JennyDigital/Tower-of-Eightness/Board Art/ANSI Mono vid board.png

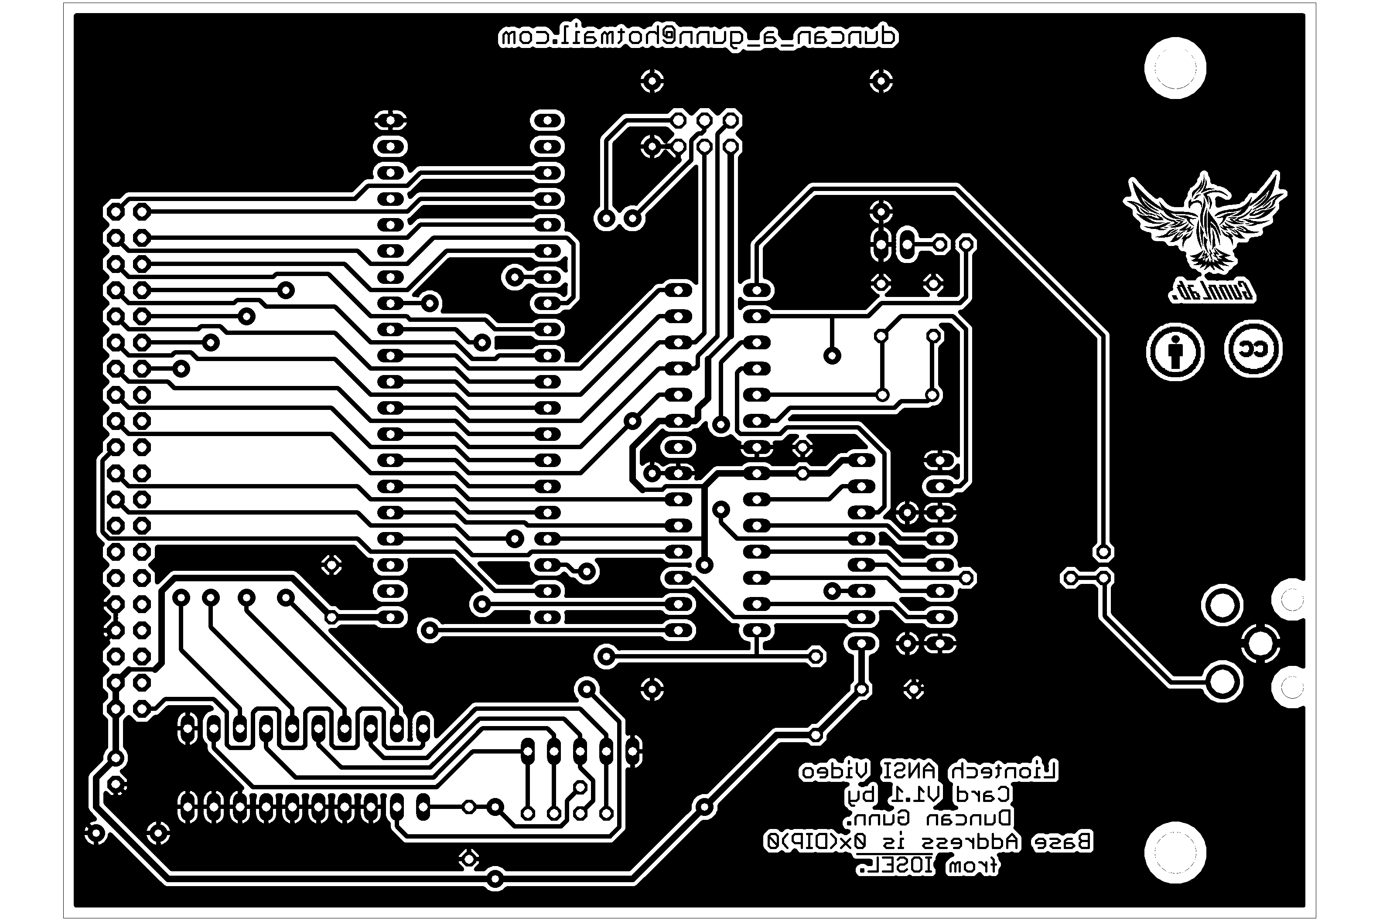
Board Art/ANSI Mono vid board.png
