JennyDigital/Tower-of-Eightness/Board Art/Bus IO Device Simulator.png

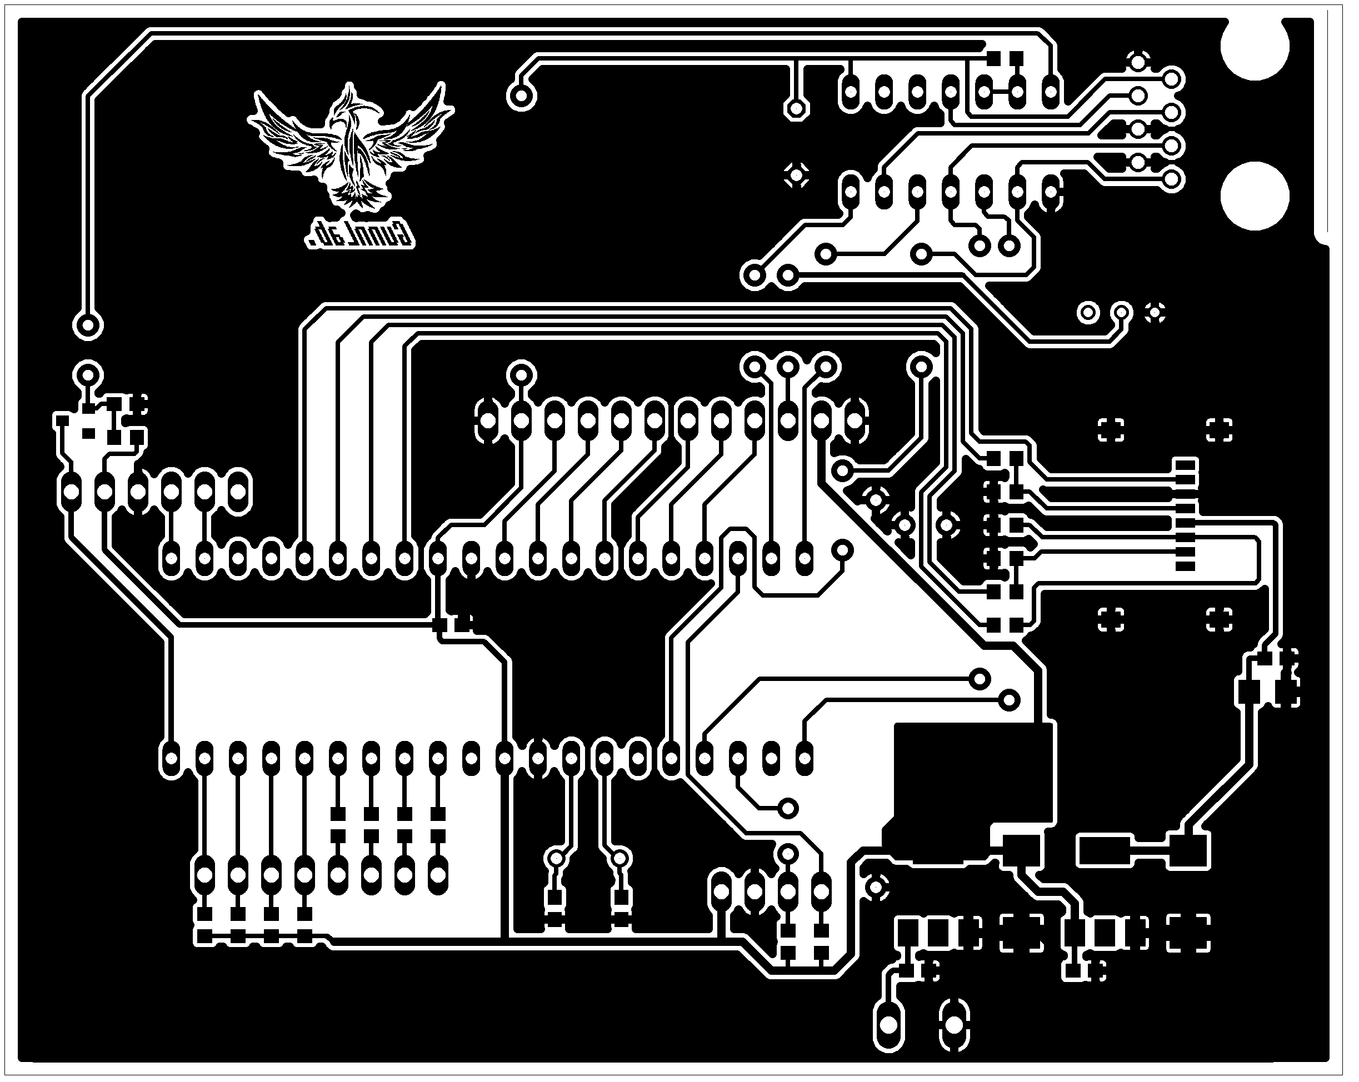
Board Art/Bus IO Device Simulator.png
