JennyDigital/Tower-of-Eightness/Board Art/Cardbus Card Extender.png

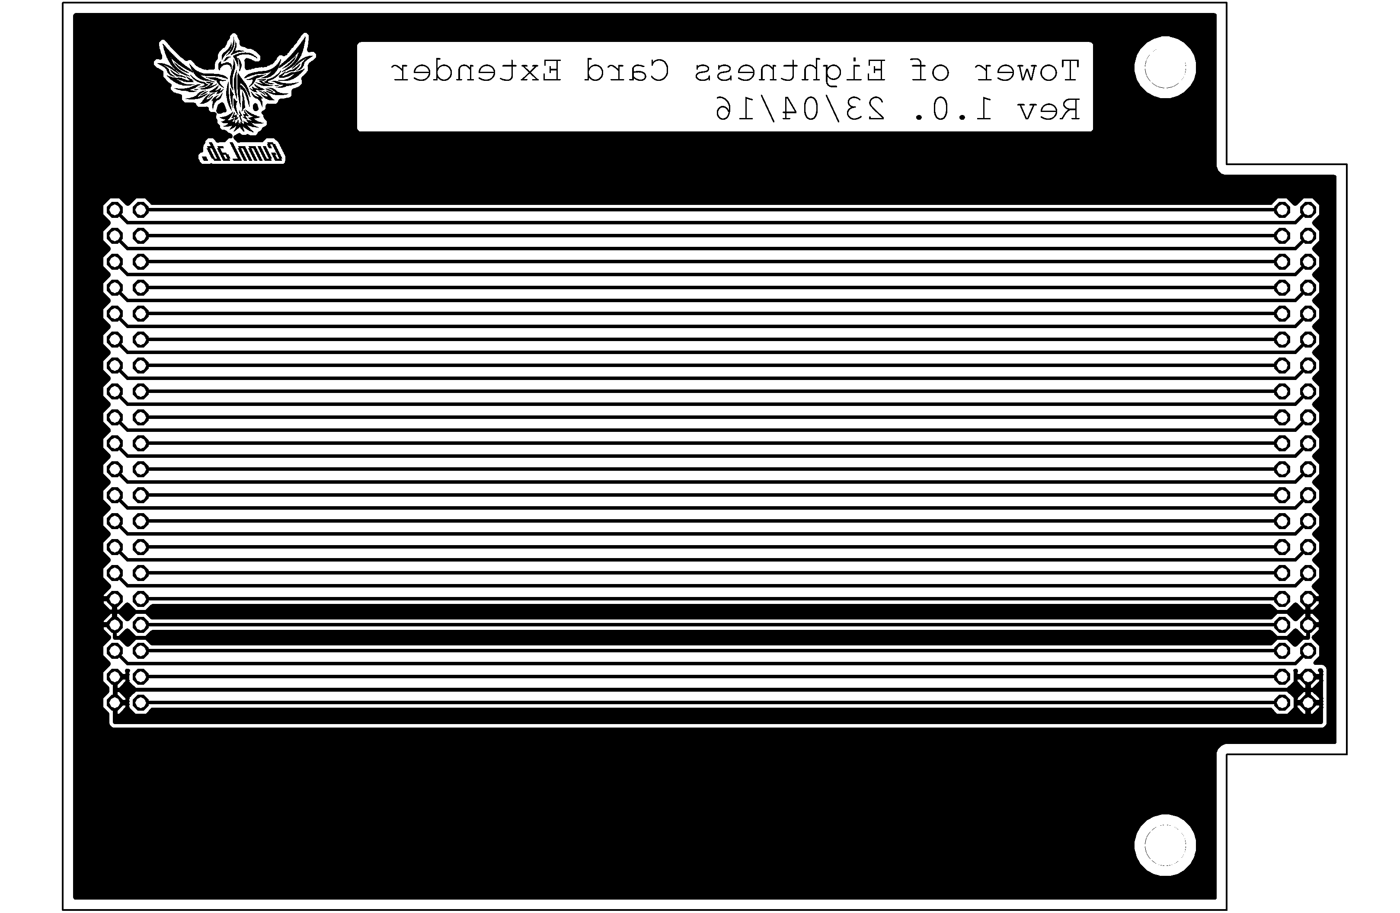
Board Art/Cardbus Card Extender.png
