JennyDigital/Tower-of-Eightness/Board Art/Serial Card V3.png

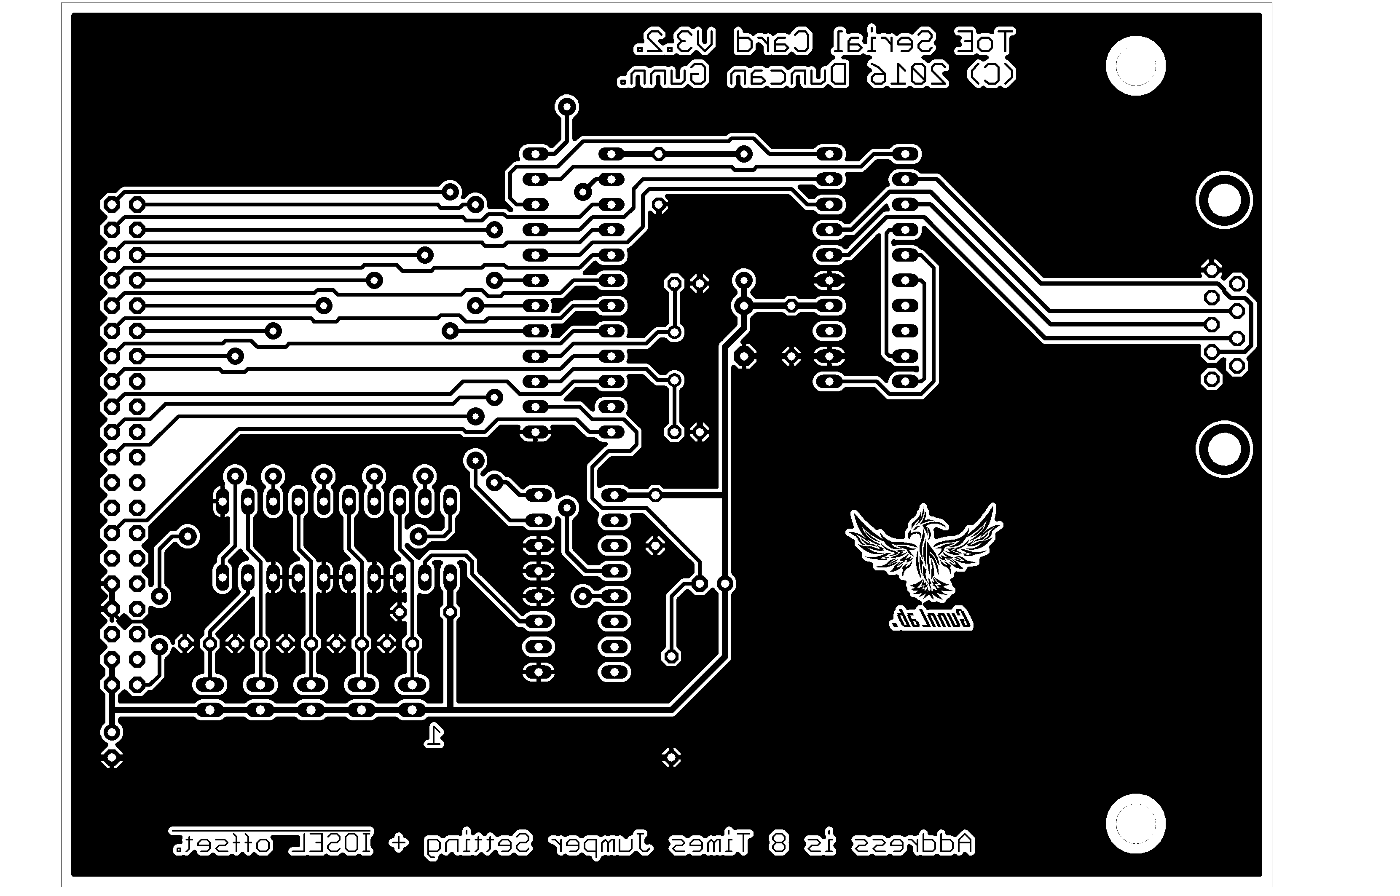
Board Art/Serial Card V3.png
