JennyDigital/Tower-of-Eightness/Board Art/Versatile IO Card.png

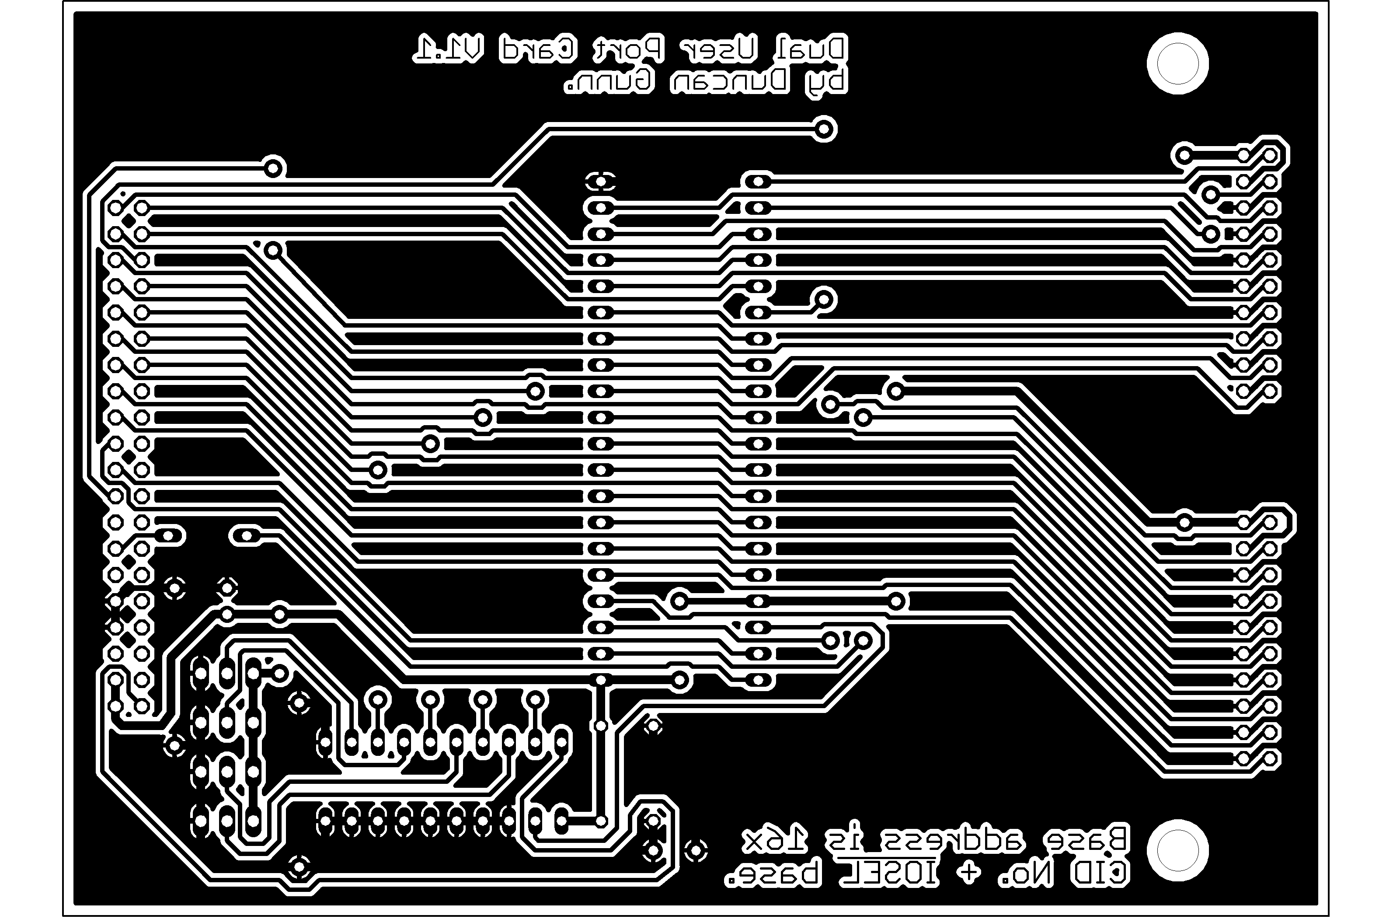
Board Art/Versatile IO Card.png
