JennyDigital/Tower-of-Eightness/Cases/Top Cap Assembly/STLs/Top Cap.stl

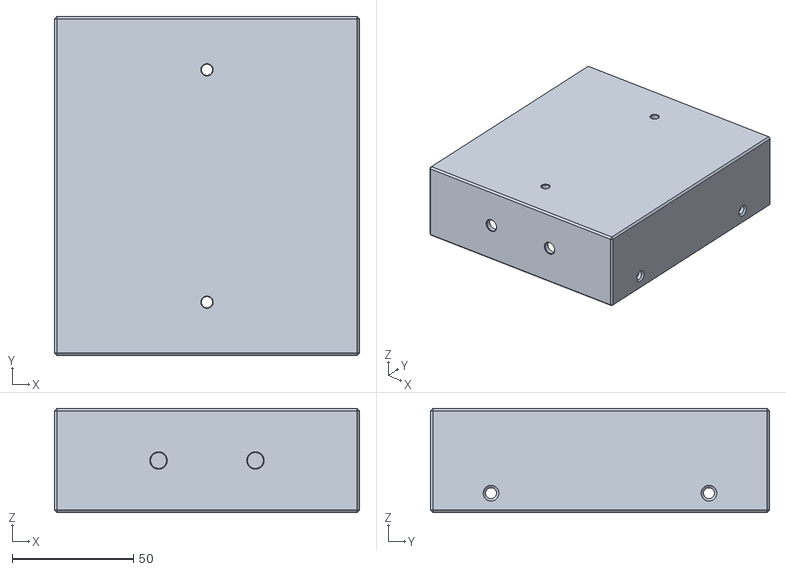
[picture p39: CAD file, 2021-09-05]
Cases/Top Cap Assembly/STLs/Top Cap.stl
126.0 x 140.0 x 43.0
