JennyDigital/Tower-of-Eightness/Cases/V3 Basetray/V3 Basetray.FCStd

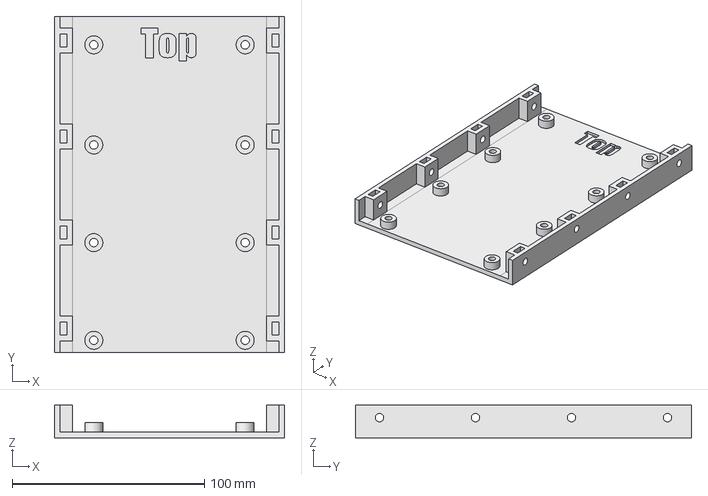
[picture p40: CAD file, 2021-09-05]
Cases/V3 Basetray/V3 Basetray.FCStd
120.0 x 175.0 x 17.0 mm
