JennyDigital/Tower-of-Eightness/Cases/Bottom cap assembly/Decorative Hoop.FCStd

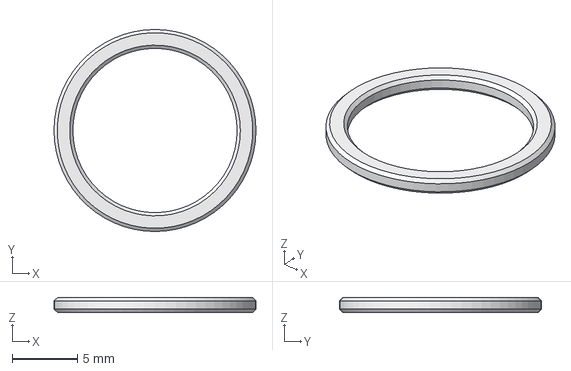
[picture p41: CAD file, 2021-09-05]
Cases/Bottom cap assembly/Decorative Hoop.FCStd
15.5 x 15.5 x 1.12 mm
