JennyDigital/Tower-of-Eightness/Cases/Bottom cap assembly/STLs/Frontplate.stl

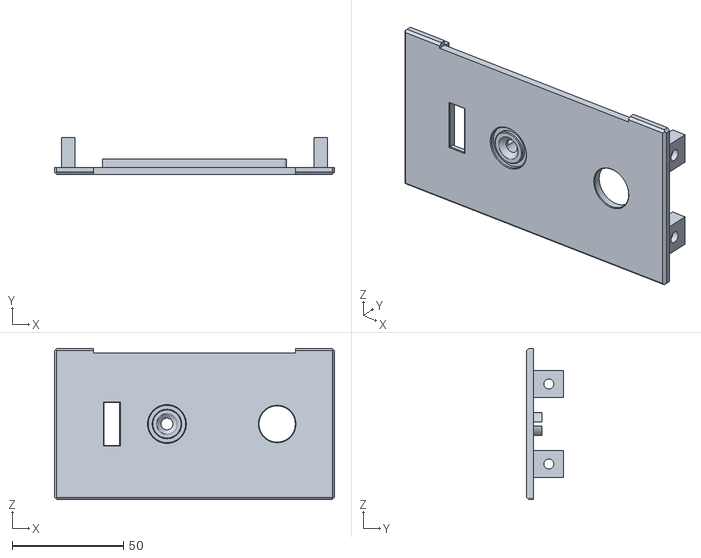
[picture p42: CAD file, 2023-03-17]
Cases/Bottom cap assembly/STLs/Frontplate.stl
126.0 x 16.5 x 68.0
