JennyDigital/Tower-of-Eightness/Cases/Faceplates/Bus Card Faceplate.fcstd

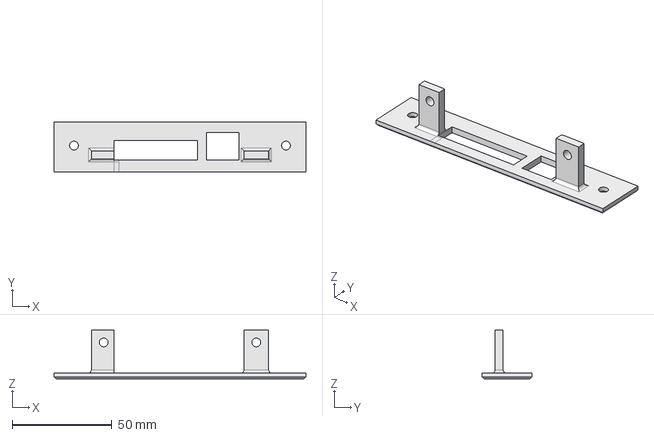
[picture p43: CAD file, 2018-06-14]
Cases/Faceplates/Bus Card Faceplate.fcstd
126.0 x 25.0 x 24.5 mm
