JennyDigital/Tower-of-Eightness/Cases/PS2 to RS232 kb adaptor (compact)/PS2 to RS232 base.FCStd

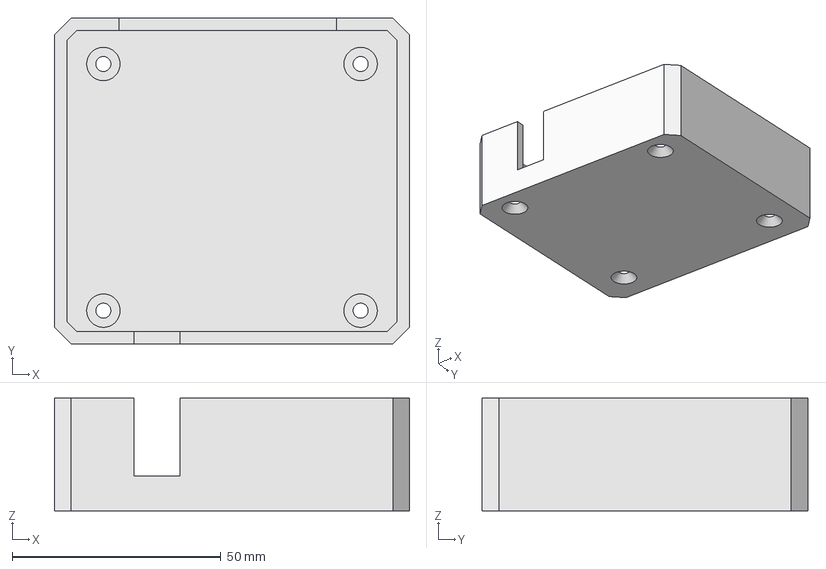
[picture p44: CAD file, 2023-03-17]
Cases/PS2 to RS232 kb adaptor (compact)/PS2 to RS232 base.FCStd
85.0 x 78.0 x 27.0 mm
