JennyDigital/Tower-of-Eightness/Cases/PS2 to Serial KB Adapter Enclosure (larger)/Foot.stl

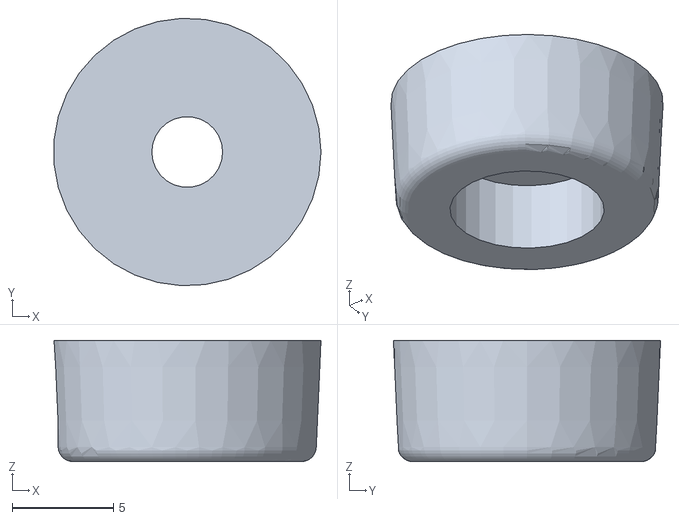
[picture p45: CAD file, 2023-03-17]
Cases/PS2 to Serial KB Adapter Enclosure (larger)/Foot.stl
13.2 x 13.2 x 6.00
