JennyDigital/Tower-of-Eightness/Cases/Sideplate/Sideplate with support edge.FCStd

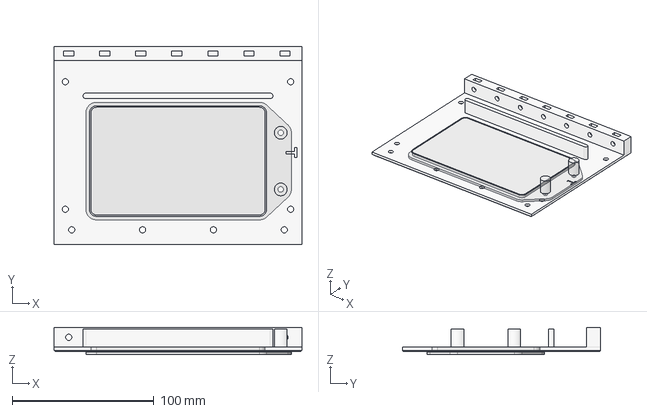
[picture p46: CAD file, 2023-03-17]
Cases/Sideplate/Sideplate with support edge.FCStd
175.0 x 140.0 x 19.2 mm
Sideplate
Vented cover
