JennyDigital/Tower-of-Eightness/Cases/Tape and Joystick Interface V1/Lid.stl

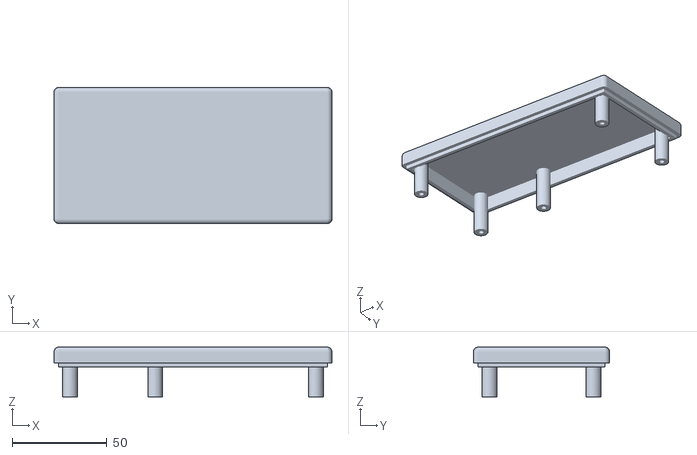
[picture p47: CAD file, 2021-09-05]
Cases/Tape and Joystick Interface V1/Lid.stl
147.0 x 72.0 x 26.4
