JennyDigital/Tower-of-Eightness/Cases/Assembly model (WIP)/Badge frame.stl

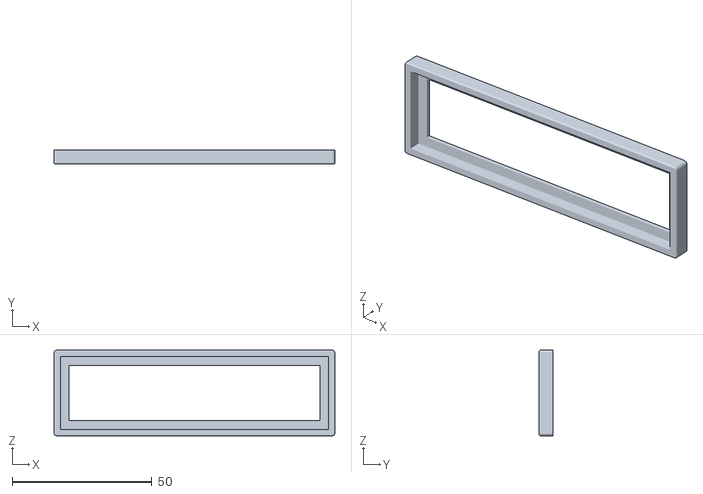
[picture p48: CAD file, 2023-03-17]
Cases/Assembly model (WIP)/Badge frame.stl
100.7 x 5.00 x 30.7
