JennyDigital/Tower-of-Eightness/Cases/Faceplates/Faceplate Blank V2.stl

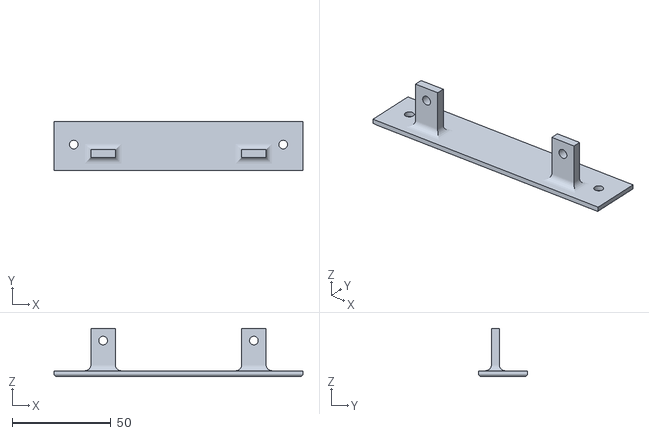
[picture p49: CAD file, 2018-06-14]
Cases/Faceplates/Faceplate Blank V2.stl
126.0 x 25.0 x 24.5
