JennyDigital/Tower-of-Eightness/Cases/PS2 to Serial KB Adapter Enclosure (larger)/Adapter.FCStd

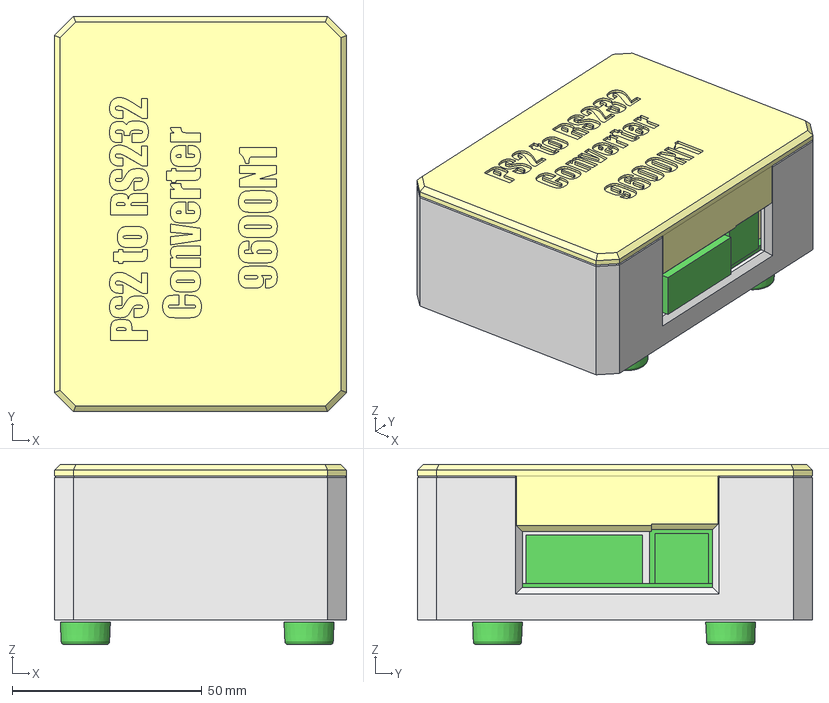
[picture p50: CAD file, 2023-03-17]
Cases/PS2 to Serial KB Adapter Enclosure (larger)/Adapter.FCStd
77.0 x 104.2 x 47.5 mm
PCB
Case base
Lid
Set of feet
