JennyDigital/Tower-of-Eightness/Cases/Sideplate/Tab.stl

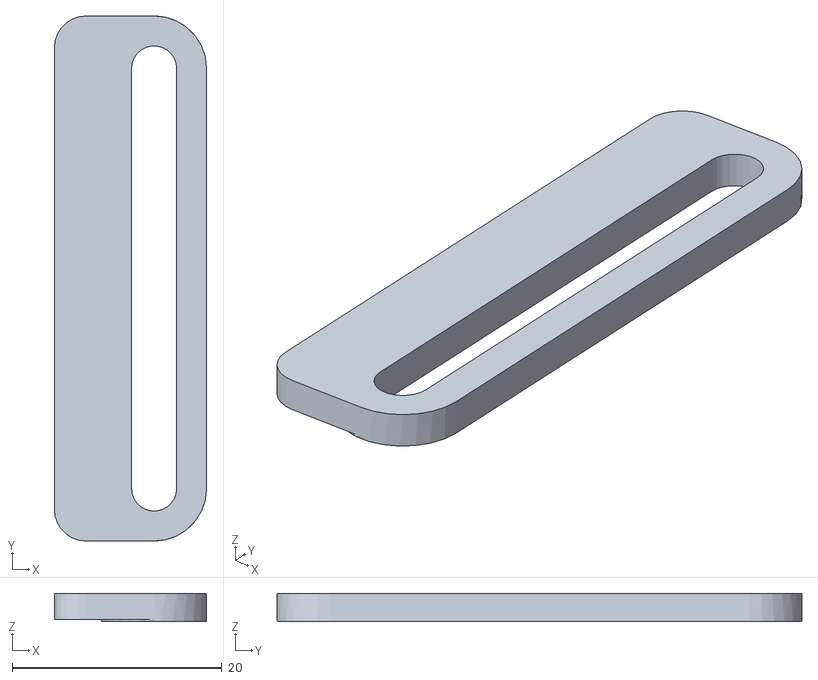
[picture p51: CAD file, 2023-03-17]
Cases/Sideplate/Tab.stl
14.5 x 50.0 x 2.70
