JennyDigital/Tower-of-Eightness/Cases/Bottom cap assembly/STLs/Backplate.stl

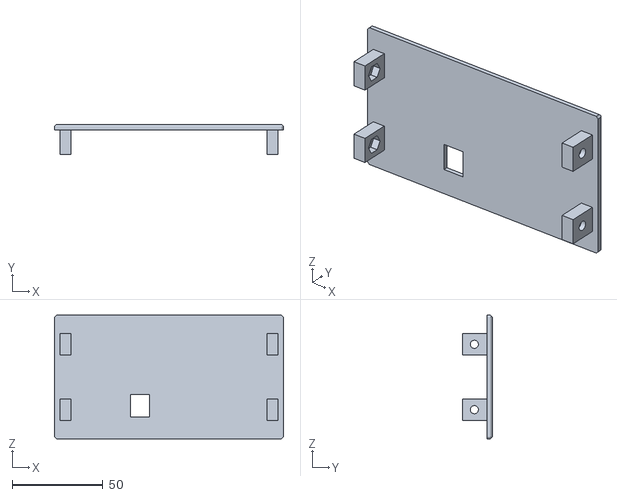
[picture p52: CAD file, 2021-09-05]
Cases/Bottom cap assembly/STLs/Backplate.stl
126.0 x 16.5 x 68.0
