JennyDigital/Tower-of-Eightness/Cases/Faceplates/Serial Faceplate.stl

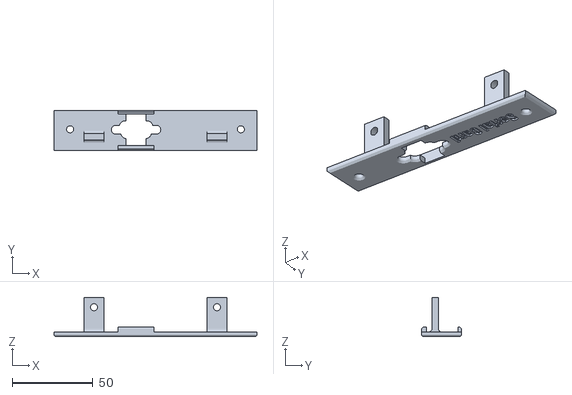
[picture p53: CAD file, 2018-06-14]
Cases/Faceplates/Serial Faceplate.stl
126.0 x 25.0 x 24.5
