JennyDigital/Tower-of-Eightness/Cases/PS2 to Serial KB Adapter Enclosure (larger)/Base.stl

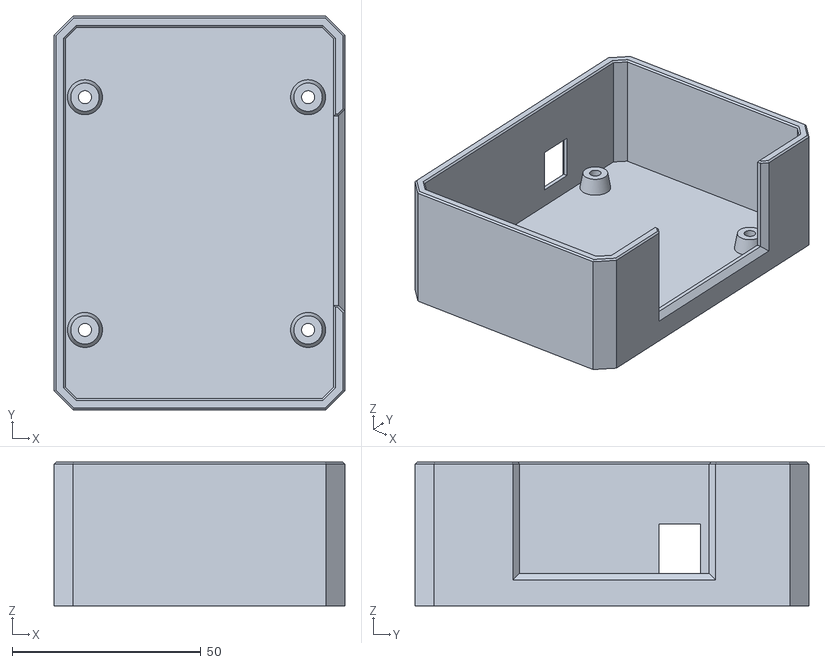
[picture p54: CAD file, 2023-03-17]
Cases/PS2 to Serial KB Adapter Enclosure (larger)/Base.stl
77.0 x 104.2 x 38.0
