JennyDigital/Tower-of-Eightness/Cases/Sideplate/Sideplate with support edges.step

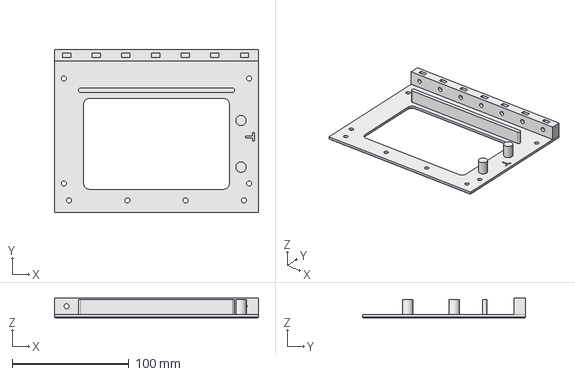
[picture p55: CAD file, 2023-03-17]
Cases/Sideplate/Sideplate with support edges.step
175.0 x 140.0 x 17.0 mm
