JennyDigital/Tower-of-Eightness/Cases/Tape and Joystick Interface V1/Tape and Joystick Interface V1.FCStd

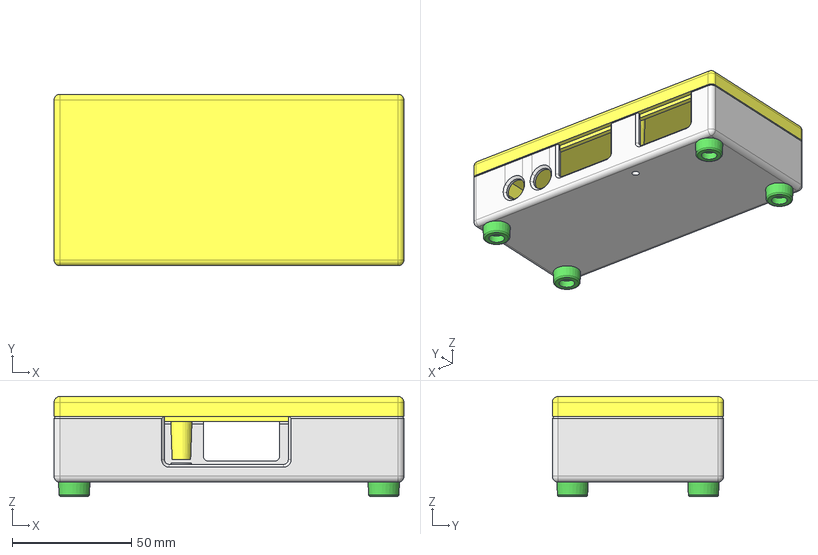
[picture p56: CAD file, 2021-09-05]
Cases/Tape and Joystick Interface V1/Tape and Joystick Interface V1.FCStd
147.0 x 72.0 x 42.0 mm
Box Base
Box Lid
Set of feet
