JennyDigital/Tower-of-Eightness/Cases/Bottom cap assembly/STLs/Hoop.stl

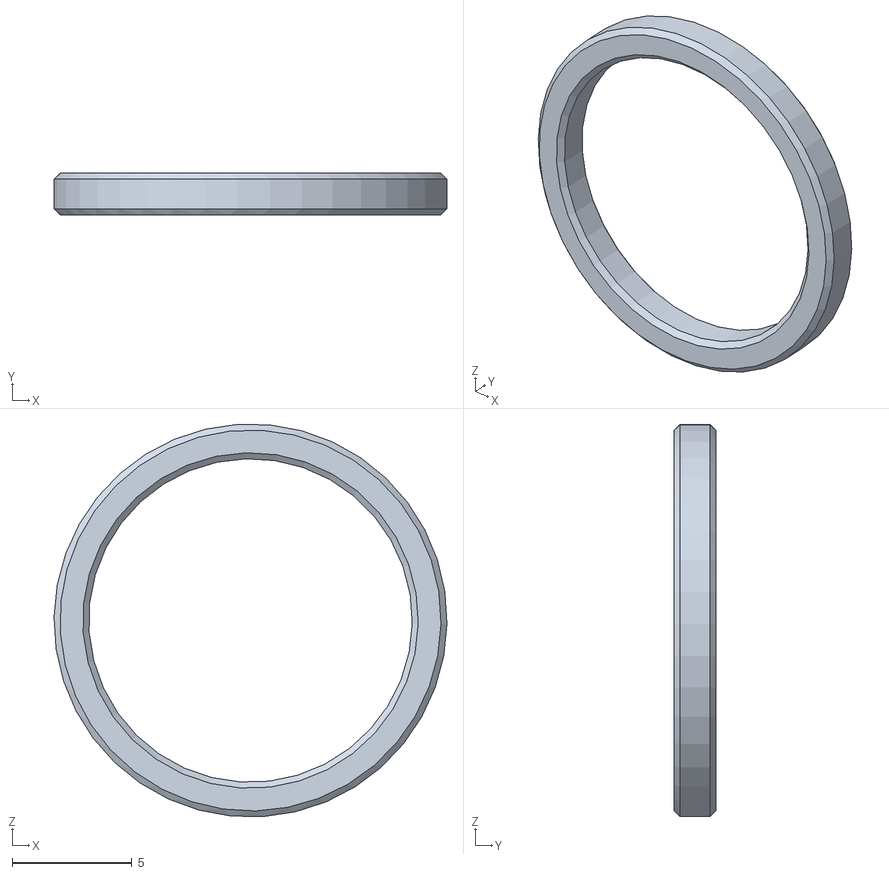
[picture p57: CAD file, 2021-09-05]
Cases/Bottom cap assembly/STLs/Hoop.stl
16.4 x 1.75 x 16.4
