JennyDigital/Tower-of-Eightness/Cases/Faceplates/Status Plate.fcstd

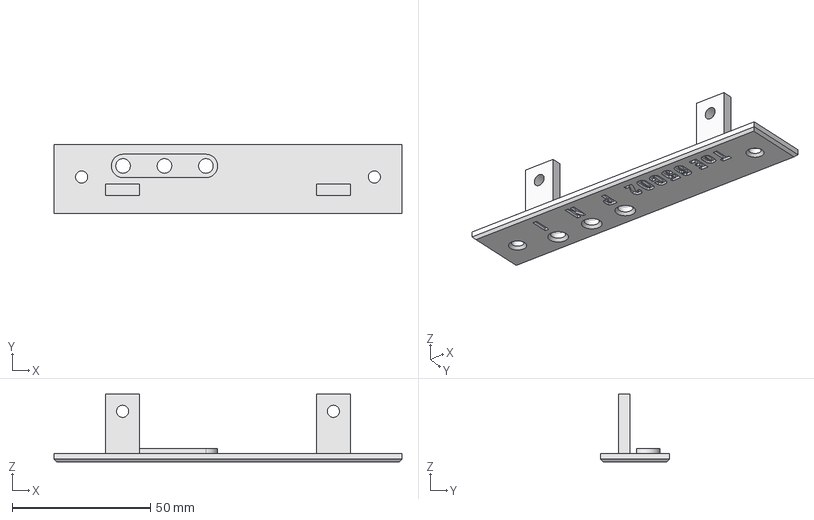
[picture p58: CAD file, 2018-06-14]
Cases/Faceplates/Status Plate.fcstd
126.0 x 25.0 x 24.5 mm
ChamferBody
