JennyDigital/Tower-of-Eightness/Cases/Sideplate/Sideplate with cover.FCStd

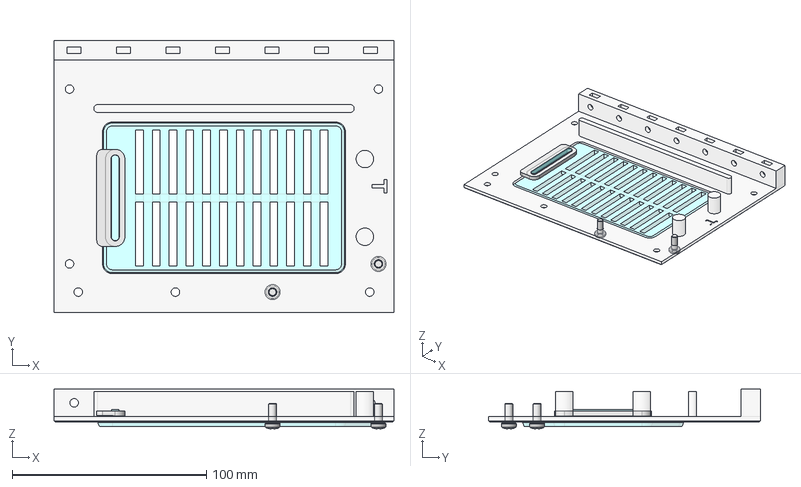
[picture p59: CAD file, 2023-03-17]
Cases/Sideplate/Sideplate with cover.FCStd
175.0 x 140.0 x 20.4 mm
Sideplate
Vented cover
Tab
M4 screw for testing
M4 screw for testing001
