JennyDigital/Tower-of-Eightness/Cases/Bottom cap assembly/STLs/Joining-bar.stl

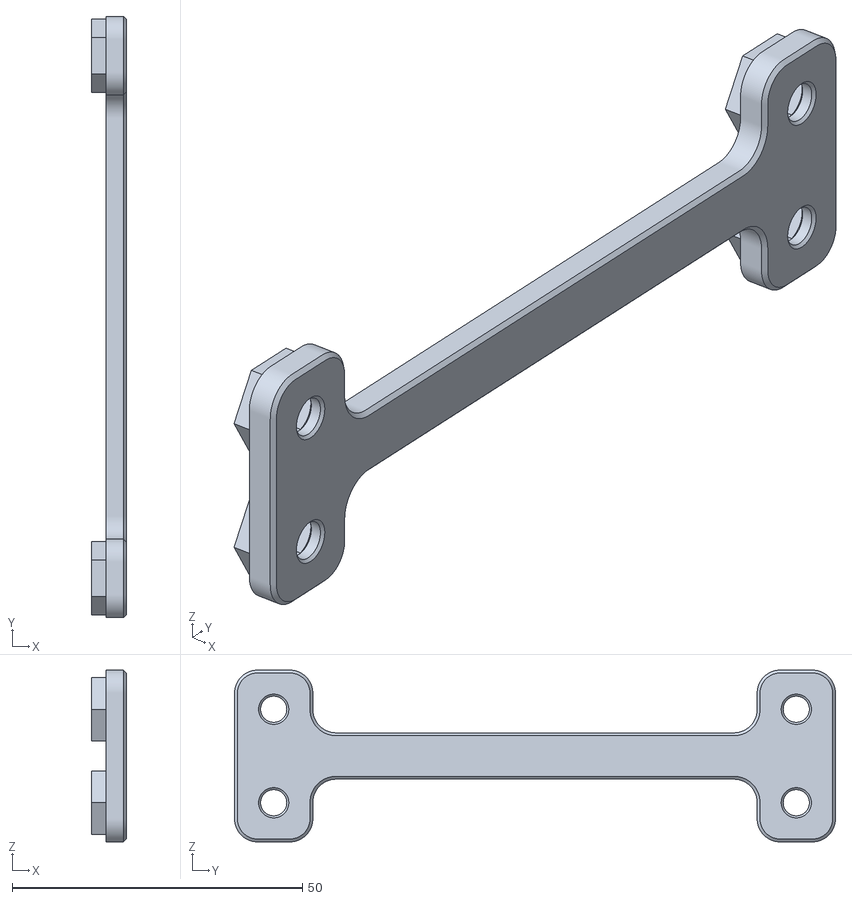
[picture p60: CAD file, 2021-09-05]
Cases/Bottom cap assembly/STLs/Joining-bar.stl
6.00 x 103.5 x 29.6
