JennyDigital/Tower-of-Eightness/Cases/Faceplates/Card Faceplate CPU V2.FCStd

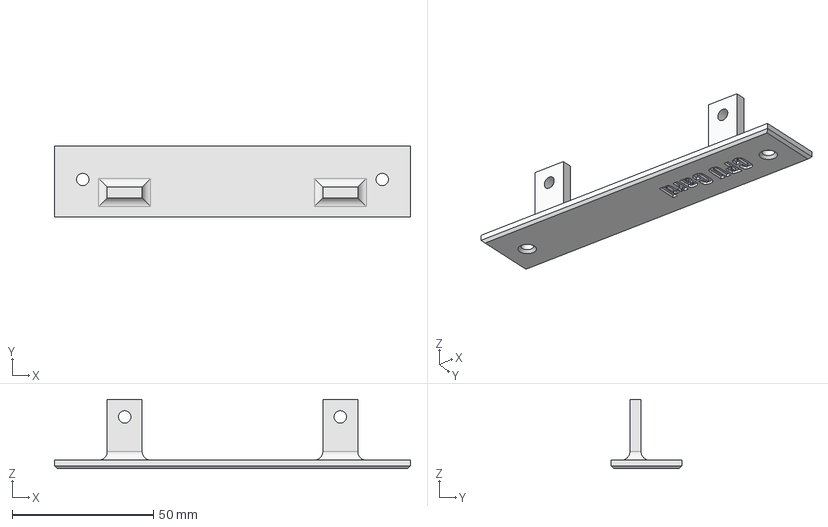
[picture p61: CAD file, 2018-06-14]
Cases/Faceplates/Card Faceplate CPU V2.FCStd
126.0 x 25.0 x 24.5 mm
