JennyDigital/Tower-of-Eightness/Cases/Finished Endcap blank.FCStd

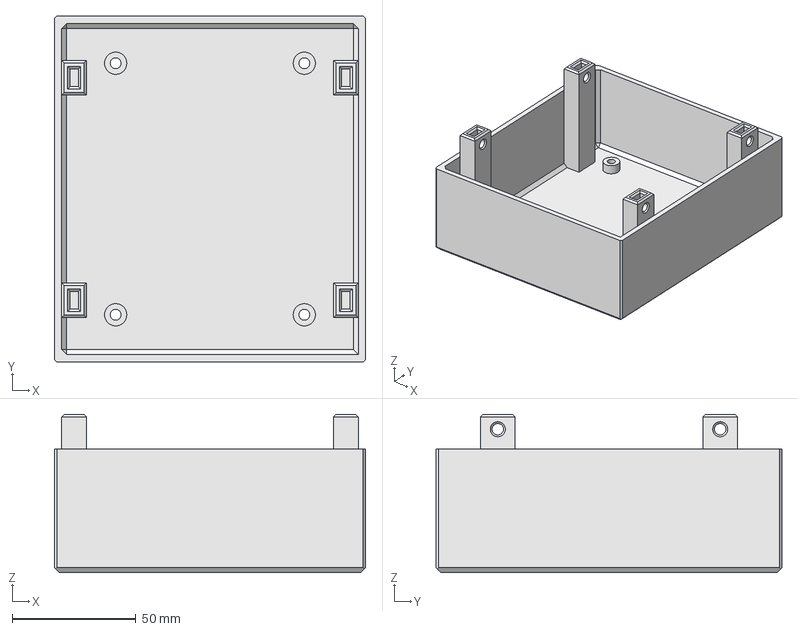
[picture p62: CAD file, 2018-06-14]
Cases/Finished Endcap blank.FCStd
126.0 x 140.0 x 64.0 mm
