JennyDigital/Tower-of-Eightness/Cases/Sideplate/Sideplate.FCStd

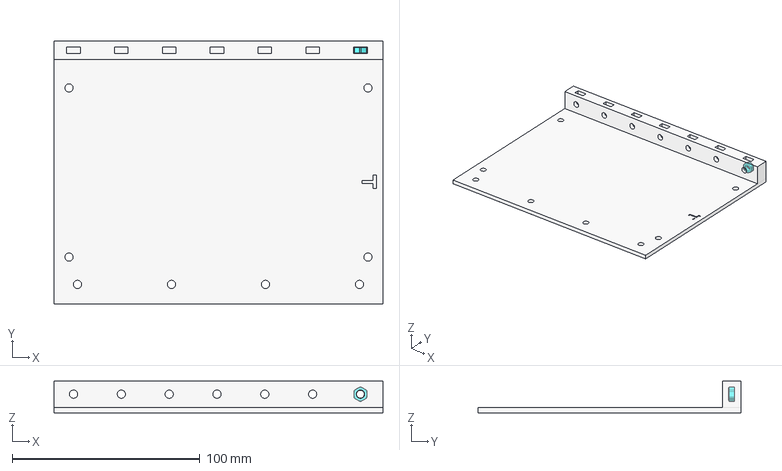
[picture p63: CAD file, 2023-03-17]
Cases/Sideplate/Sideplate.FCStd
175.0 x 140.0 x 17.0 mm
M4 Nut
