JennyDigital/Tower-of-Eightness/Cases/Bottom cap assembly/STLs/Baseplate.stl

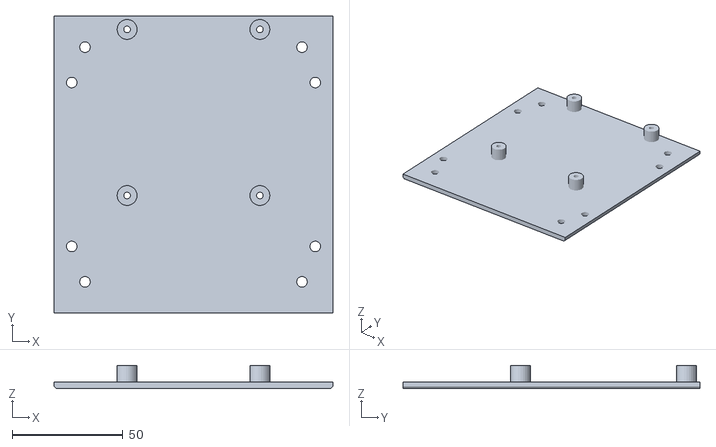
[picture p64: CAD file, 2021-09-05]
Cases/Bottom cap assembly/STLs/Baseplate.stl
126.0 x 134.0 x 10.4
