JennyDigital/Tower-of-Eightness/Cases/Guide Vee.FCStd

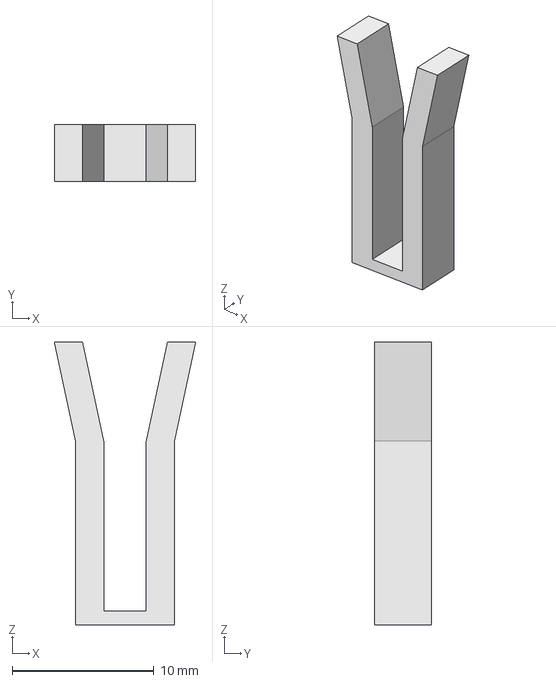
[picture p65: CAD file, 2018-06-14]
Cases/Guide Vee.FCStd
10.0 x 4.00 x 20.0 mm
