JennyDigital/Tower-of-Eightness/Cases/Guide Vee (Deeper).step

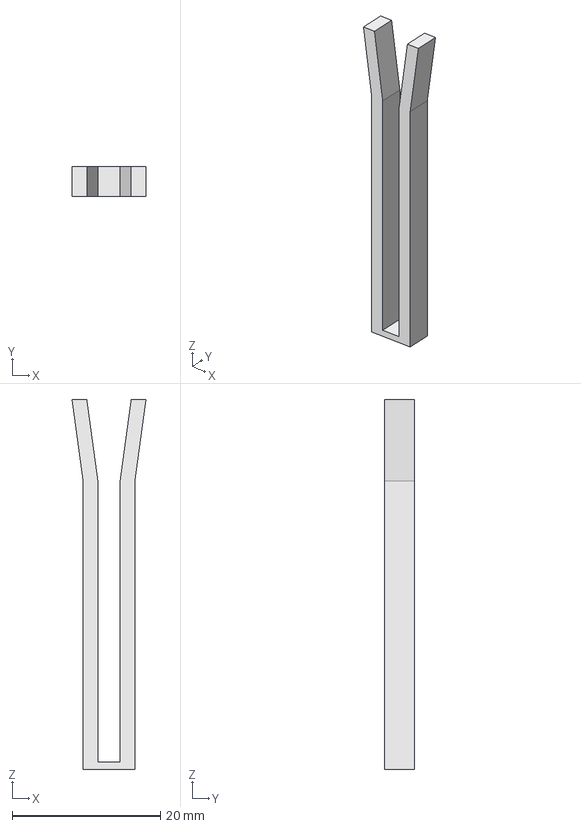
[picture p66: CAD file, 2018-06-14]
Cases/Guide Vee (Deeper).step
10.0 x 4.00 x 50.0 mm
