JennyDigital/Tower-of-Eightness/Cases/Faceplates/Sound Card V1.FCStd

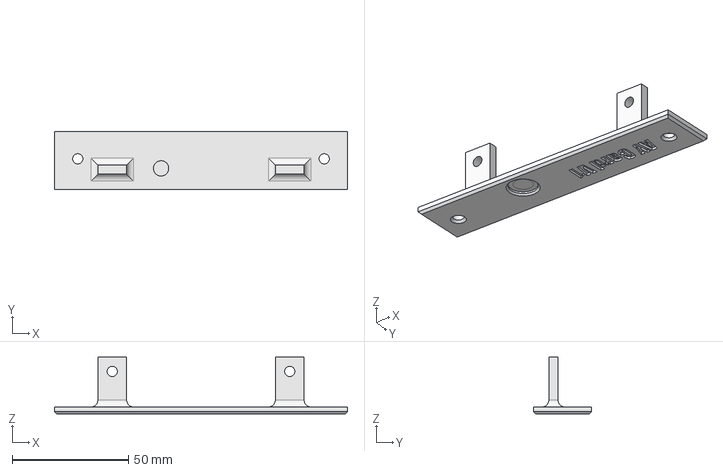
[picture p67: CAD file, 2018-06-14]
Cases/Faceplates/Sound Card V1.FCStd
126.0 x 25.0 x 24.5 mm
