JennyDigital/Tower-of-Eightness/Cases/Taller Card Guide.fcstd

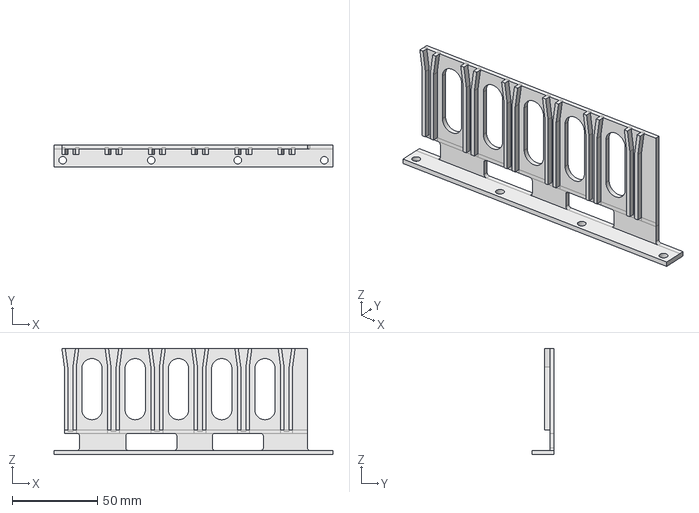
[picture p68: CAD file, 2018-06-14]
Cases/Taller Card Guide.fcstd
164.1 x 13.0 x 62.5 mm
