JennyDigital/Tower-of-Eightness/Cases/Endcap blank.FCStd

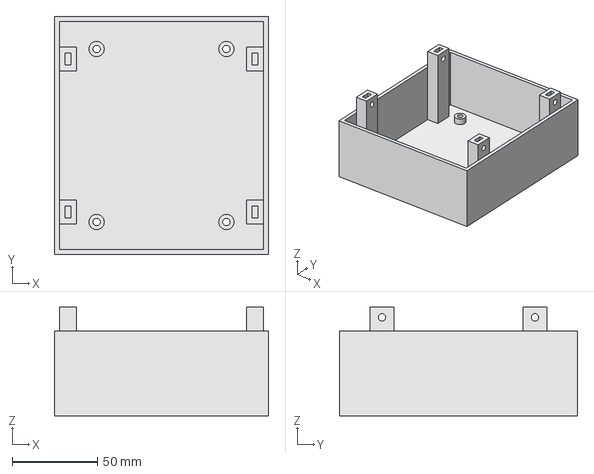
[picture p69: CAD file, 2018-06-14]
Cases/Endcap blank.FCStd
126.0 x 140.0 x 64.0 mm
