JennyDigital/Tower-of-Eightness/Cases/Faceplates/Memory Faceplate V2.FCStd

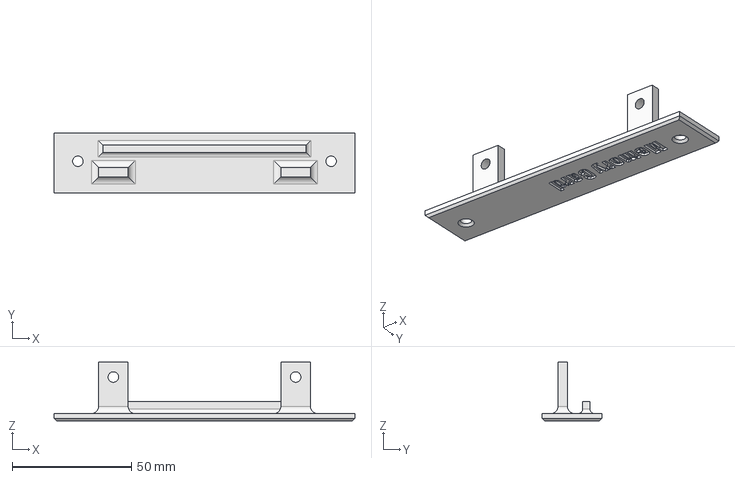
[picture p71: CAD file, 2018-06-14]
Cases/Faceplates/Memory Faceplate V2.FCStd
126.0 x 25.0 x 24.5 mm
