JennyDigital/Tower-of-Eightness/Schematics/ANSI-Video-Board/ANSI Mono vid board.brd

## EAGLE design Schematics/ANSI-Video-Board/ANSI Mono vid board.brd (2021-09-05)

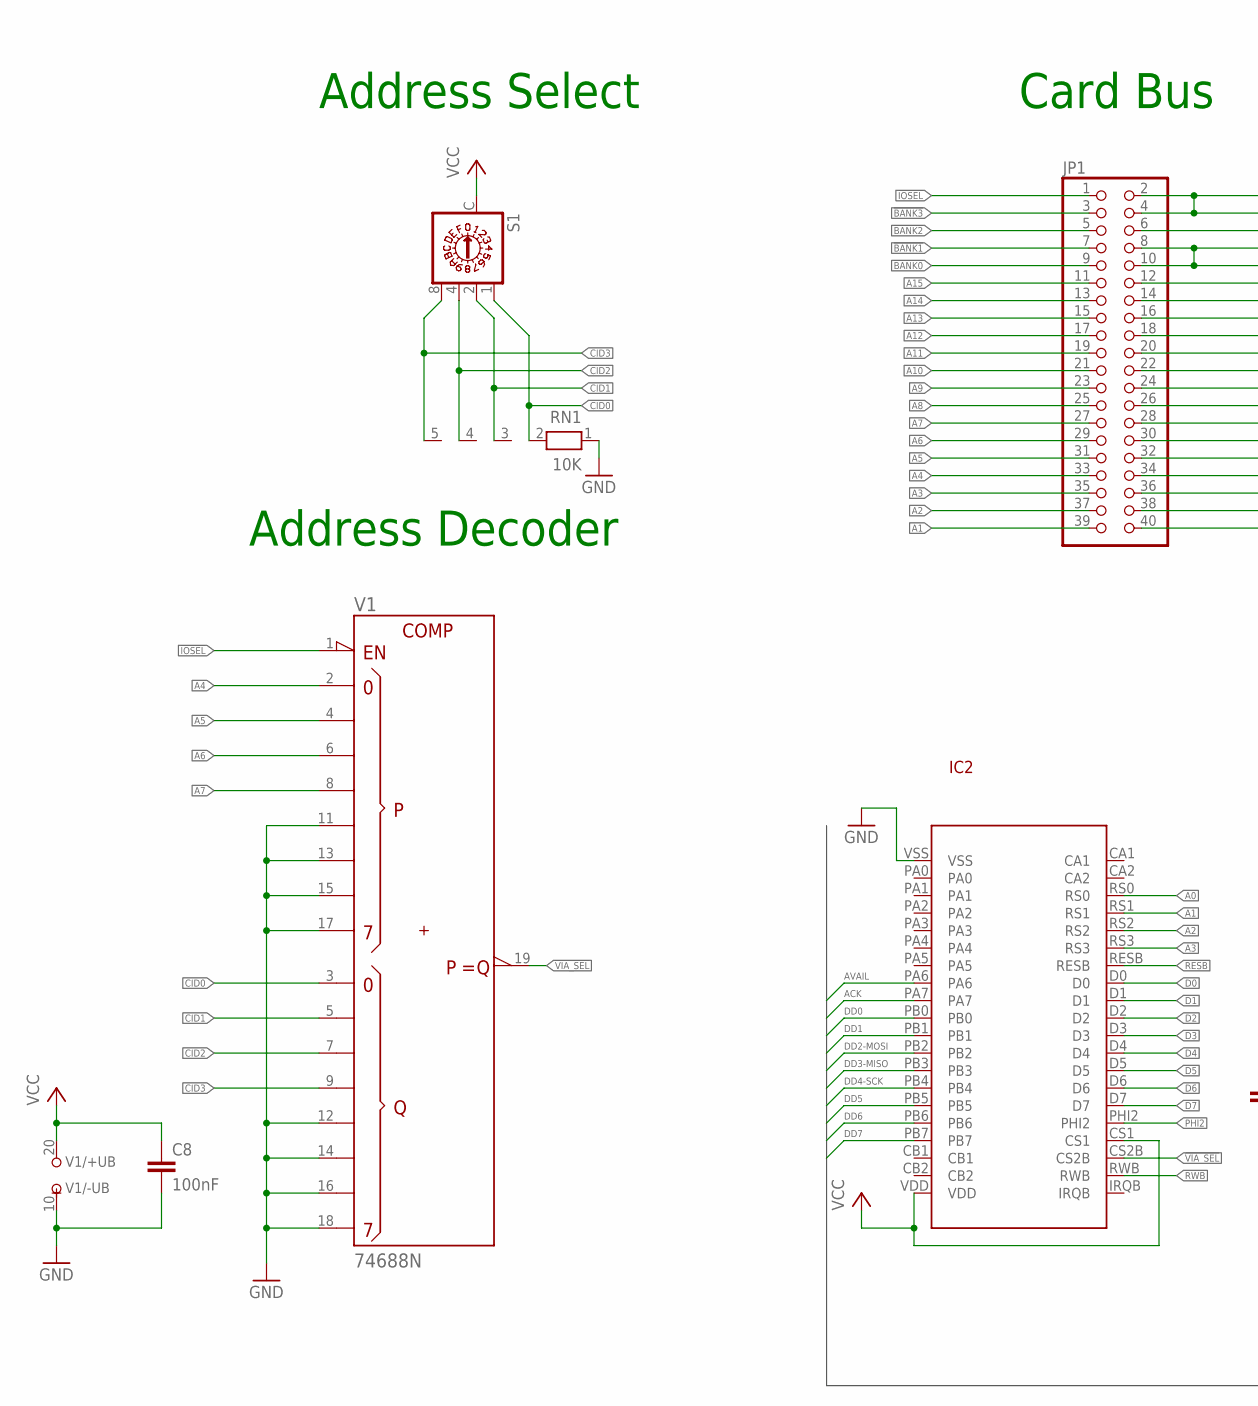
[picture p96: schematic ANSI Mono vid board.sch, part in row 1, column 1]

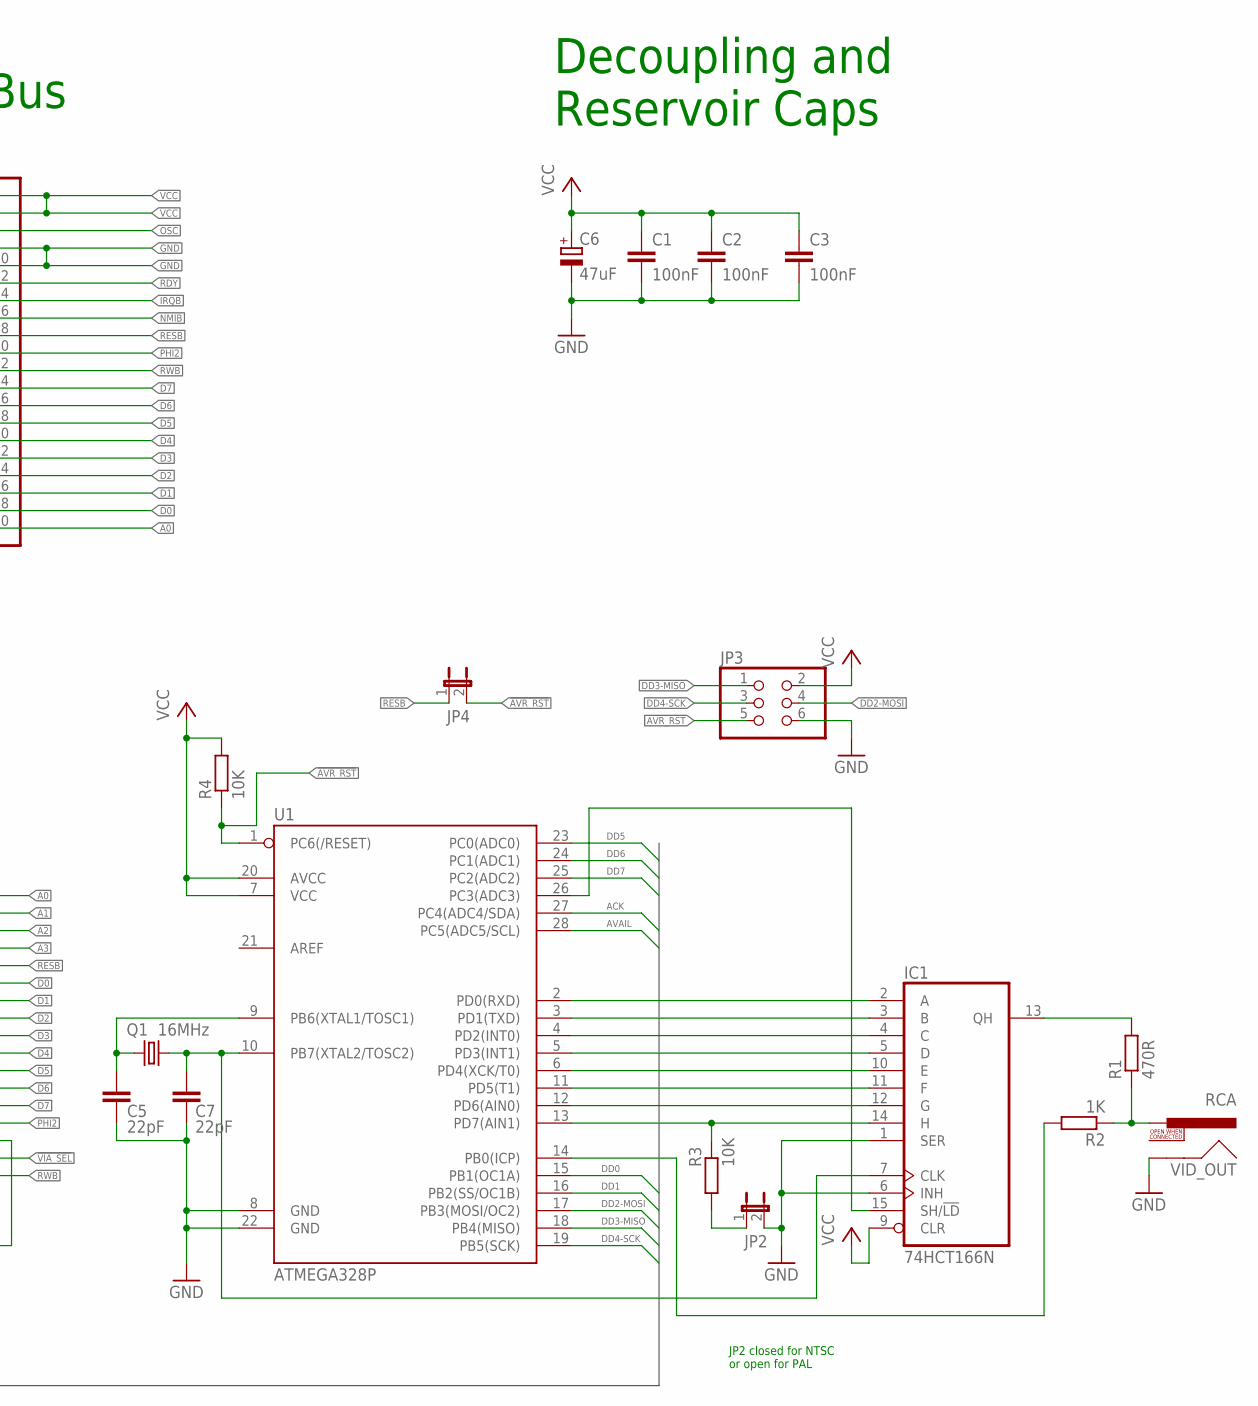
[picture p97: schematic ANSI Mono vid board.sch, part in row 1, column 2]

Parts:
C1, C2, C8: 100nF; C050-025X075
C3: 100nF; C025-025X050
C5, C7: 22pF; C050-025X075
C6: 47uF; E2,5-7
IC1: 74HCT166N; DIL16
IC2: W65C22; W65C22-DIP
JP1: PINHD-2X20/90; 2X20/90
JP2, JP4: JP1E; JP1
JP3: PINHD-2X3; 2X03
Q1: 16MHz; HC49U-V
R1: 470R; 0207/10
R2: 1K; 0207/10
R3: 10K; 0207/2V
R4: 10K; 0207/7
RN1: 10K; RN-5
S1: DRR3016; DRR3010
U1: ATMEGA328P; DIL28-3
V1: 74688N; DIL20
VID_OUT: RCA

Connections:
!AVR_RST: JP3.5, JP4.2, R4.1, U1.1 (PC6(/RESET))
!BANK0: JP1.9
!BANK1: JP1.7
!BANK2: JP1.5
!BANK3: JP1.3
!IOSEL: JP1.1, V1.1 (!G)
!VIA_SEL: IC2.CS2B, V1.19 (!P=Q)
A0: IC2.RS0, JP1.40
A1: IC2.RS1, JP1.39
A2: IC2.RS2, JP1.37
A3: IC2.RS3, JP1.35
A4: JP1.33, V1.2 (P0)
A5: JP1.31, V1.4 (P1)
A6: JP1.29, V1.6 (P2)
A7: JP1.27, V1.8 (P3)
A8: JP1.25
A9: JP1.23
A10: JP1.21
A11: JP1.19
A12: JP1.17
A13: JP1.15
A14: JP1.13
A15: JP1.11
ACK: IC2.PA7, U1.27 (PC4(ADC4/SDA))
AVAIL: IC2.PA6, U1.28 (PC5(ADC5/SCL))
CID0: RN1.2, S1.1, V1.3 (Q0)
CID1: RN1.3, S1.2, V1.5 (Q1)
CID2: RN1.4, S1.4, V1.7 (Q2)
CID3: RN1.5, S1.8, V1.9 (Q3)
D0: IC2.D0, JP1.38
D1: IC2.D1, JP1.36
D2: IC2.D2, JP1.34
D3: IC2.D3, JP1.32
D4: IC2.D4, JP1.30
D5: IC2.D5, JP1.28
D6: IC2.D6, JP1.26
D7: IC2.D7, JP1.24
DD0: IC2.PB0, U1.15 (PB1(OC1A))
DD1: IC2.PB1, U1.16 (PB2(SS/OC1B))
DD2-MOSI: IC2.PB2, JP3.4, U1.17 (PB3(MOSI/OC2))
DD3-MISO: IC2.PB3, JP3.1, U1.18 (PB4(MISO))
DD4-SCK: IC2.PB4, JP3.3, U1.19 (PB5(SCK))
DD5: IC2.PB5, U1.23 (PC0(ADC0))
DD6: IC2.PB6, U1.24 (PC1(ADC1))
DD7: IC2.PB7, U1.25 (PC2(ADC2))
GND: C1.2, C2.2, C3.2, C5.2, C6.-, C7.2, C8.2, IC1.1 (SER), IC1.6 (INH), IC1.8 (GND), IC2.VSS, JP1.8, JP1.10, JP2.2, JP3.6, RN1.1, U1.8 (GND), U1.22 (GND), V1.10 (-UB), V1.11 (P4), V1.12 (Q4), V1.13 (P5), V1.14 (Q5), V1.15 (P6), V1.16 (Q6), V1.17 (P7), V1.18 (Q7), VID_OUT.SHELL
IRQB: JP1.14
unnamed: JP2.1, R3.1
unnamed: C5.1, Q1.2, U1.9 (PB6(XTAL1/TOSC1))
unnamed: C7.1, IC1.7 (CLK), Q1.1, U1.10 (PB7(XTAL2/TOSC2))
unnamed: IC1.2 (A), U1.2 (PD0(RXD))
unnamed: IC1.3 (B), U1.3 (PD1(TXD))
unnamed: IC1.4 (C), U1.4 (PD2(INT0))
unnamed: IC1.5 (D), U1.5 (PD3(INT1))
unnamed: IC1.10 (E), U1.6 (PD4(XCK/T0))
unnamed: IC1.11 (F), U1.11 (PD5(T1))
unnamed: IC1.12 (G), U1.12 (PD6(AIN0))
unnamed: IC1.14 (H), R3.2, U1.13 (PD7(AIN1))
unnamed: IC1.13 (QH), R1.2
unnamed: R2.2, U1.14 (PB0(ICP))
unnamed: IC1.15 (SH/!LD), U1.26 (PC3(ADC3))
unnamed: R1.1, R2.1, VID_OUT.PIN
NMIB: JP1.16
OSC: JP1.6
PHI2: IC2.PHI2, JP1.20
RDY: JP1.12
RESB: IC2.RESB, JP1.18, JP4.1
RWB: IC2.RWB, JP1.22
VCC: C1.1, C2.1, C3.1, C6.+, C8.1, IC1.9 (CLR), IC1.16 (VCC), IC2.CS1, IC2.VDD, JP1.2, JP1.4, JP3.2, R4.2, S1.C, U1.7 (VCC), U1.20 (AVCC), V1.20 (+UB)

Notes on the sheet:
Card Bus
Decoupling and Reservoir Caps
JP2 closed for NTSC or open for PAL
Address Select
Address Decoder

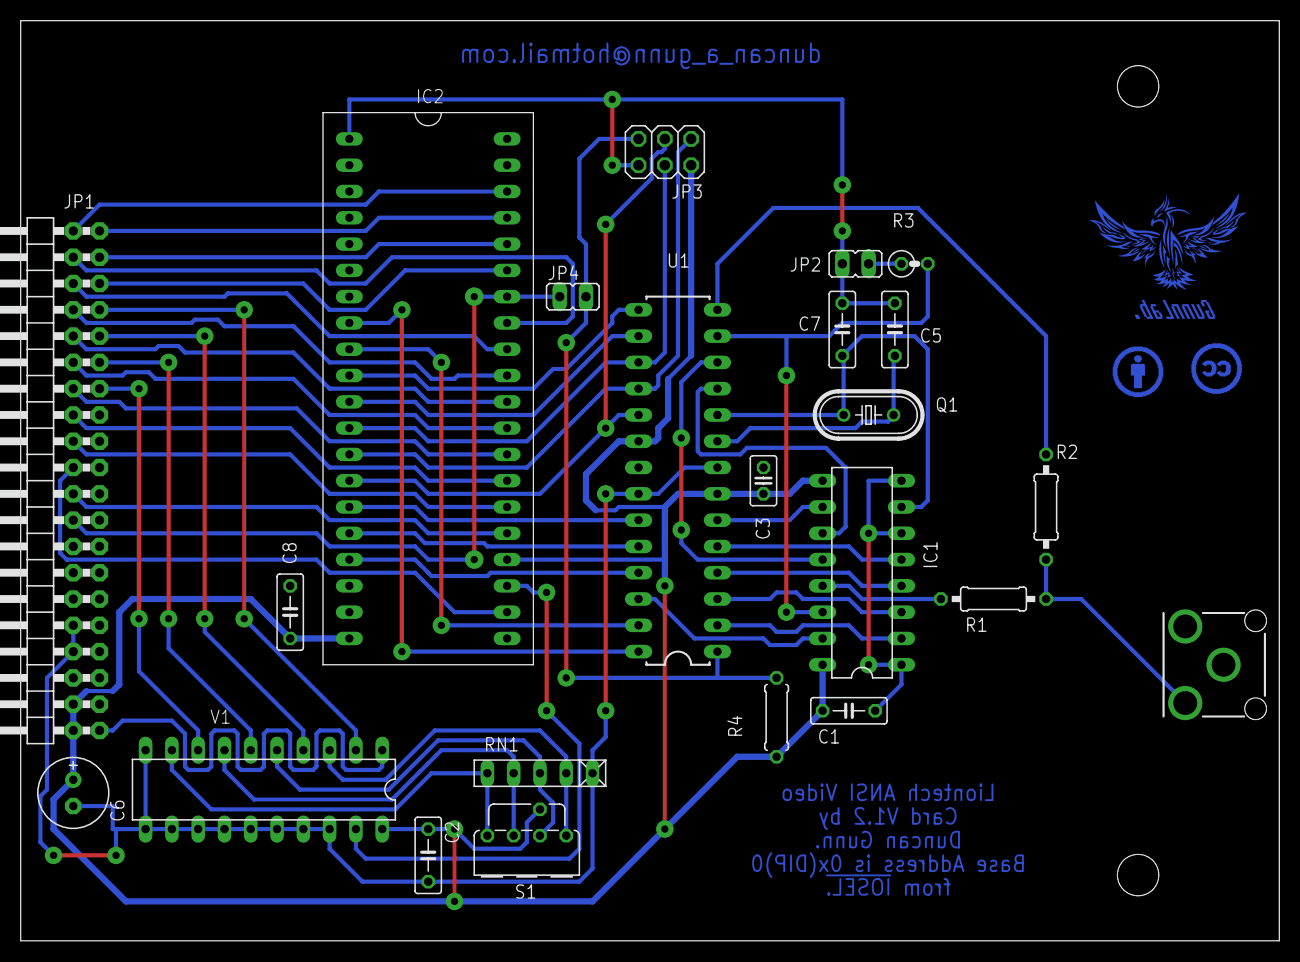
[picture p98: board ANSI Mono vid board.brd from above]

Board: 2 copper layers, 121.6 x 88.9 mm, 26 parts (0 on the bottom side), 53 nets.

Other parts of the board:
U$1: LIONTECH
U$2: CC
U$3: BY
