JennyDigital/Tower-of-Eightness/Schematics/Card-Extender/Cardbus Card Extender.brd

## EAGLE design Schematics/Card-Extender/Cardbus Card Extender.brd (2018-06-14)

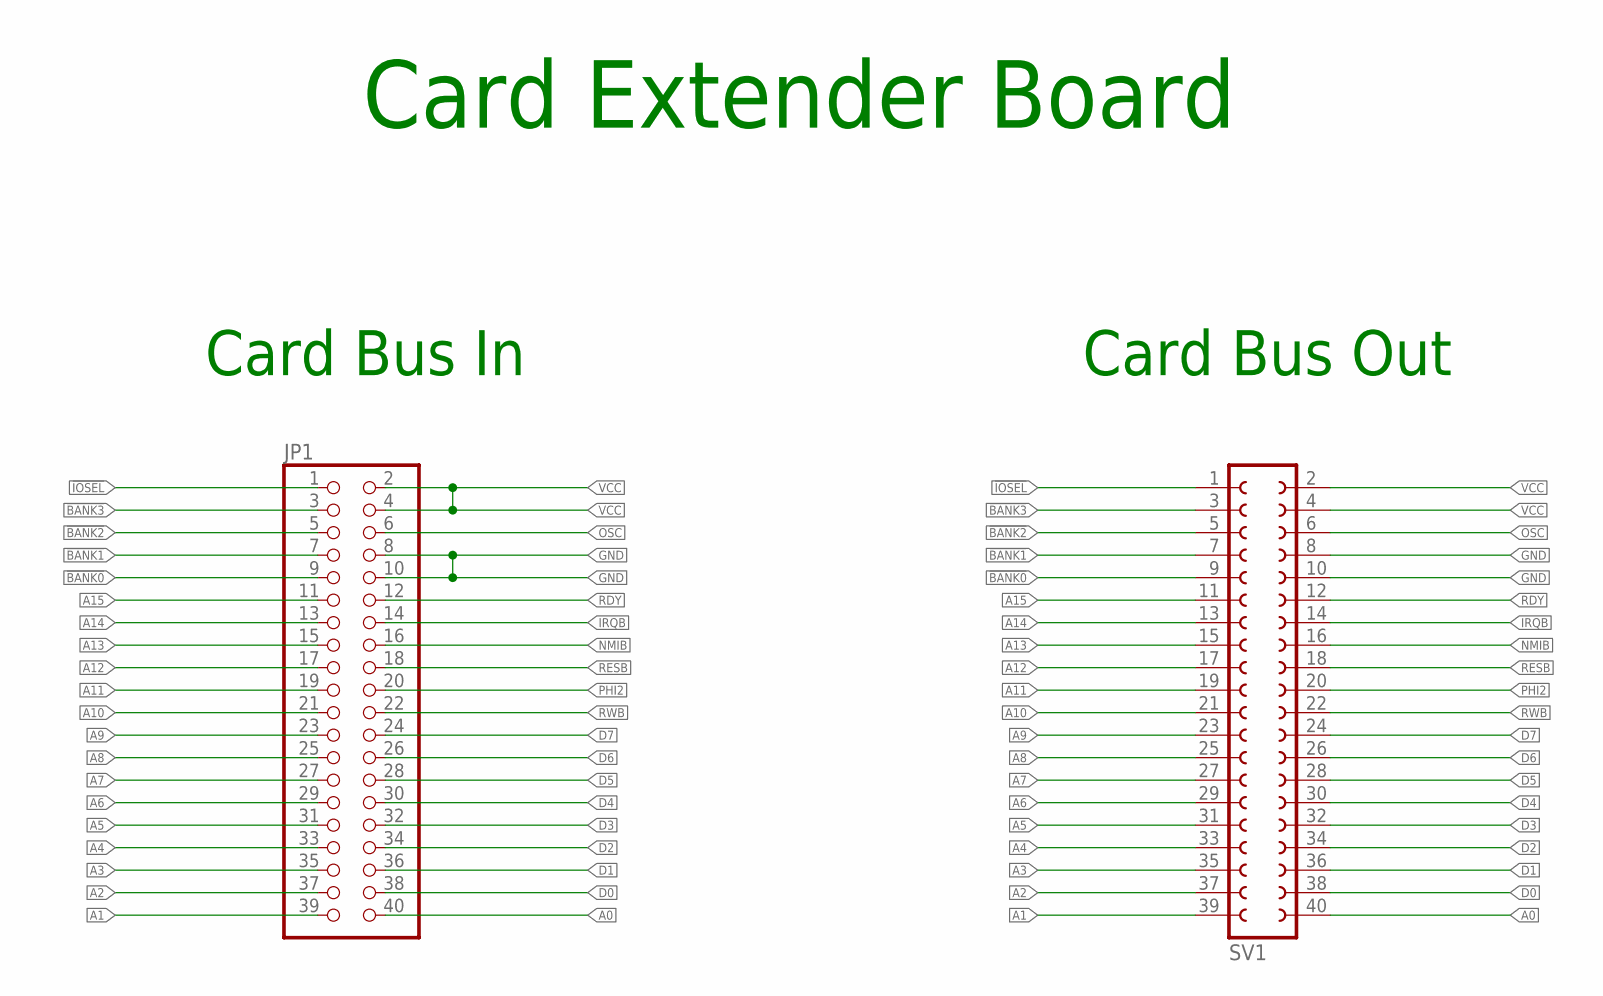
[picture p99: schematic Cardbus Card Extender.sch]

Parts:
JP1: PINHD-2X20/90; 2X20/90
SV1: FE20-2W

Connections:
!BANK0: JP1.9, SV1.9
!BANK1: JP1.7, SV1.7
!BANK2: JP1.5, SV1.5
!BANK3: JP1.3, SV1.3
!IOSEL: JP1.1, SV1.1
A0: JP1.40, SV1.40
A1: JP1.39, SV1.39
A2: JP1.37, SV1.37
A3: JP1.35, SV1.35
A4: JP1.33, SV1.33
A5: JP1.31, SV1.31
A6: JP1.29, SV1.29
A7: JP1.27, SV1.27
A8: JP1.25, SV1.25
A9: JP1.23, SV1.23
A10: JP1.21, SV1.21
A11: JP1.19, SV1.19
A12: JP1.17, SV1.17
A13: JP1.15, SV1.15
A14: JP1.13, SV1.13
A15: JP1.11, SV1.11
D0: JP1.38, SV1.38
D1: JP1.36, SV1.36
D2: JP1.34, SV1.34
D3: JP1.32, SV1.32
D4: JP1.30, SV1.30
D5: JP1.28, SV1.28
D6: JP1.26, SV1.26
D7: JP1.24, SV1.24
GND: JP1.8, JP1.10, SV1.8, SV1.10
IRQB: JP1.14, SV1.14
NMIB: JP1.16, SV1.16
OSC: JP1.6, SV1.6
PHI2: JP1.20, SV1.20
RDY: JP1.12, SV1.12
RESB: JP1.18, SV1.18
RWB: JP1.22, SV1.22
VCC: JP1.2, JP1.4, SV1.2, SV1.4

Notes on the sheet:
Card Bus In
Card Bus Out
Card Extender Board

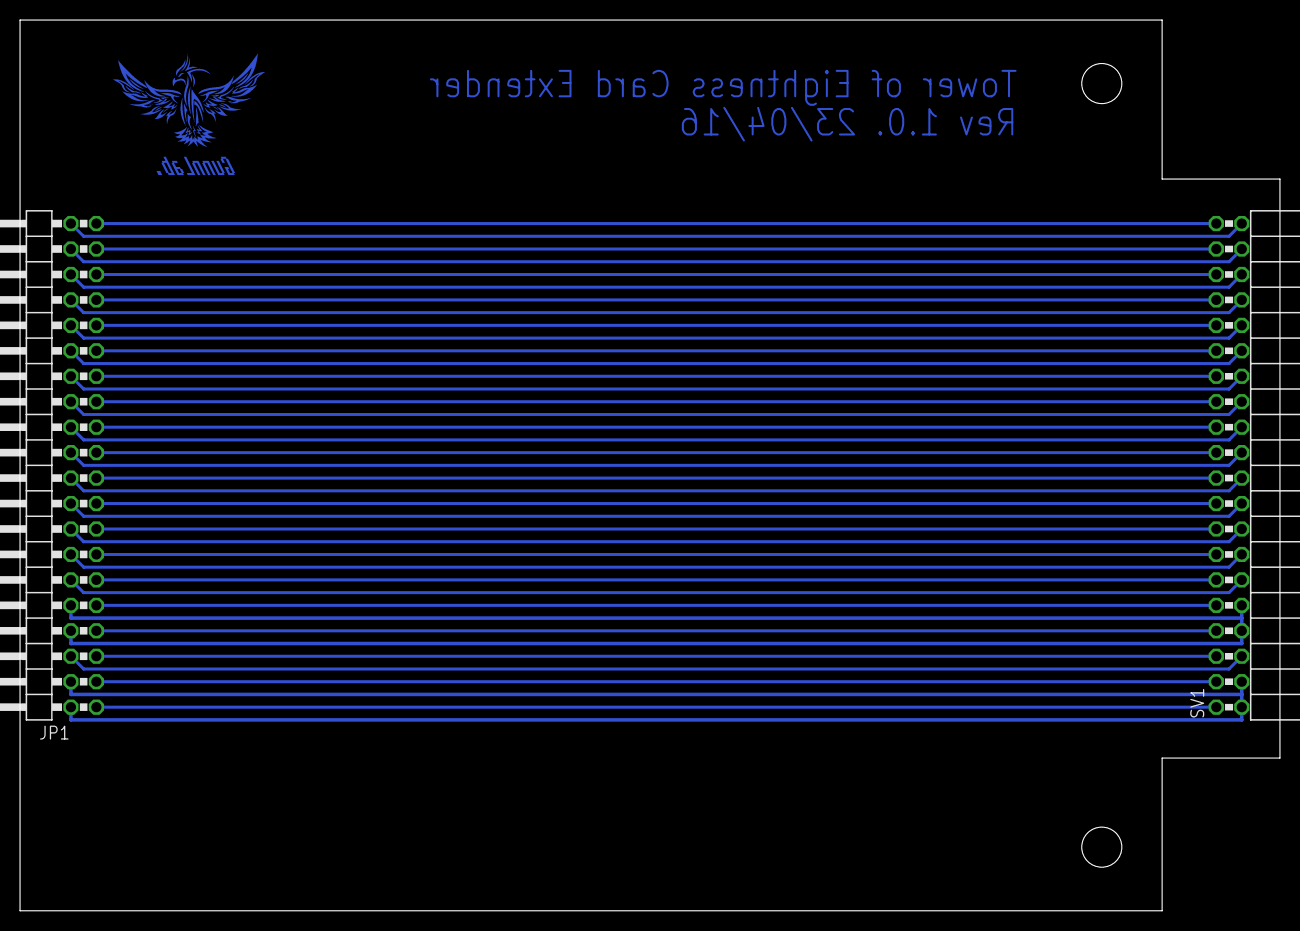
[picture p100: board Cardbus Card Extender.brd from above]

Board: 2 copper layers, 125.7 x 88.9 mm, 3 parts (0 on the bottom side), 38 nets.

Other parts of the board:
U$1: LIONTECH
