JennyDigital/Tower-of-Eightness/Schematics/Bus-IO-and_Centronics-Card/Bus IO and Centronics Card.brd

## EAGLE design Schematics/Bus-IO-and_Centronics-Card/Bus IO and Centronics Card.brd (2021-09-05)

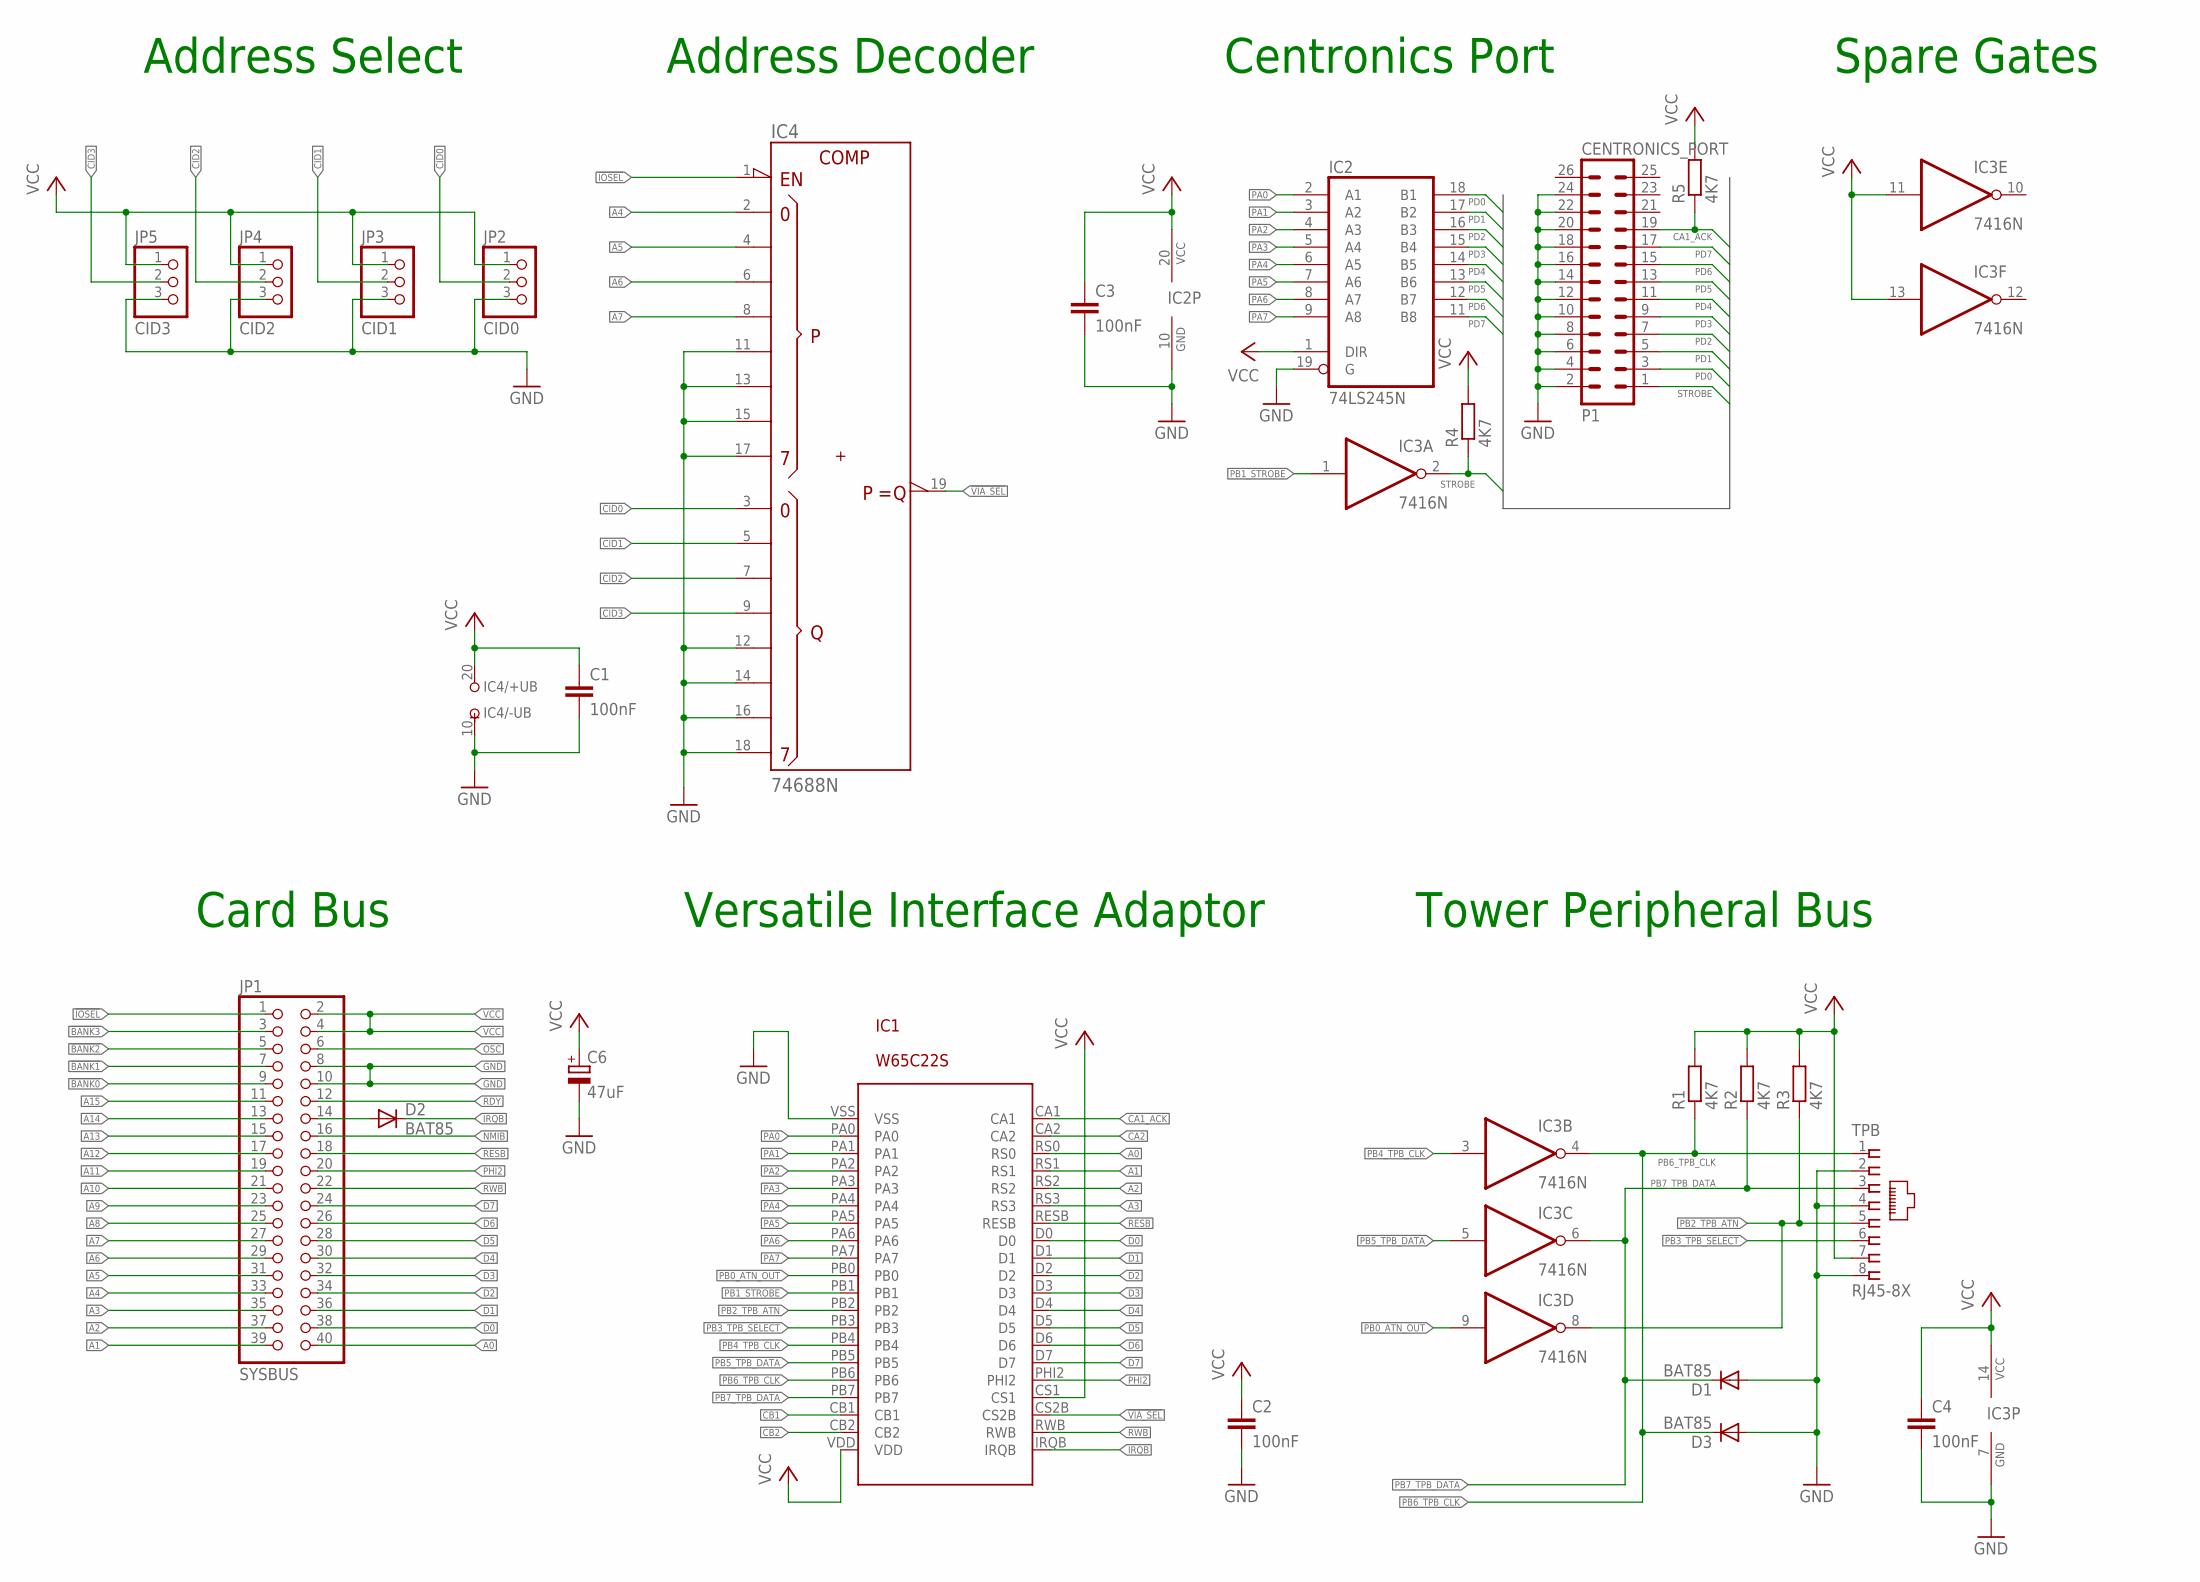
[picture p101: schematic Bus IO and Centronics Card.sch]

Parts:
C1, C2, C3, C4: 100nF; C050-025X075
C6: 47uF; E2,5-7
CENTRONICS_PORT: P1; ML26L
D1, D2, D3: BAT85; DO34-7
IC1: W65C22S; W65C22-DIP
IC2: 74LS245N; DIL20
IC3: 7416N; DIL14
IC4: 74688N; DIL20
JP1: SYSBUS; 2X20/90
JP2: CID0; 1X03
JP3: CID1; 1X03
JP4: CID2; 1X03
JP5: CID3; 1X03
R1, R2, R3, R4, R5: 4K7; 0207/10
TPB: RJ45-8X; RJ45-NO-SHIELD

Connections:
!BANK0: JP1.9
!BANK1: JP1.7
!BANK2: JP1.5
!BANK3: JP1.3
!IOSEL: IC4.1 (!G), JP1.1
!VIA_SEL: IC1.CS2B, IC4.19 (!P=Q)
A0: IC1.RS0, JP1.40
A1: IC1.RS1, JP1.39
A2: IC1.RS2, JP1.37
A3: IC1.RS3, JP1.35
A4: IC4.2 (P0), JP1.33
A5: IC4.4 (P1), JP1.31
A6: IC4.6 (P2), JP1.29
A7: IC4.8 (P3), JP1.27
A8: JP1.25
A9: JP1.23
A10: JP1.21
A11: JP1.19
A12: JP1.17
A13: JP1.15
A14: JP1.13
A15: JP1.11
CA1_ACK: CENTRONICS_PORT.19, IC1.CA1, R5.1
CA2: IC1.CA2
CB1: IC1.CB1
CB2: IC1.CB2
CID0: IC4.3 (Q0), JP2.2
CID1: IC4.5 (Q1), JP3.2
CID2: IC4.7 (Q2), JP4.2
CID3: IC4.9 (Q3), JP5.2
D0: IC1.D0, JP1.38
D1: IC1.D1, JP1.36
D2: IC1.D2, JP1.34
D3: IC1.D3, JP1.32
D4: IC1.D4, JP1.30
D5: IC1.D5, JP1.28
D6: IC1.D6, JP1.26
D7: IC1.D7, JP1.24
GND: C1.2, C2.2, C3.2, C4.2, C6.-, CENTRONICS_PORT.2, CENTRONICS_PORT.4, CENTRONICS_PORT.6, CENTRONICS_PORT.8, CENTRONICS_PORT.10, CENTRONICS_PORT.12, CENTRONICS_PORT.14, CENTRONICS_PORT.16, CENTRONICS_PORT.18, CENTRONICS_PORT.20, CENTRONICS_PORT.22, CENTRONICS_PORT.24, D1.A, D3.A, IC1.VSS, IC2.10 (GND), IC2.19 (G), IC3.7 (GND), IC4.10 (-UB), IC4.11 (P4), IC4.12 (Q4), IC4.13 (P5), IC4.14 (Q5), IC4.15 (P6), IC4.16 (Q6), IC4.17 (P7), IC4.18 (Q7), JP1.8, JP1.10, JP2.3, JP3.3, JP4.3, JP5.3, TPB.2, TPB.4, TPB.8
IRQB: D2.C, IC1.IRQB
unnamed: D2.A, JP1.14
NMIB: JP1.16
OSC: JP1.6
PA0: IC1.PA0, IC2.2 (A1)
PA1: IC1.PA1, IC2.3 (A2)
PA2: IC1.PA2, IC2.4 (A3)
PA3: IC1.PA3, IC2.5 (A4)
PA4: IC1.PA4, IC2.6 (A5)
PA5: IC1.PA5, IC2.7 (A6)
PA6: IC1.PA6, IC2.8 (A7)
PA7: IC1.PA7, IC2.9 (A8)
PB0_ATN_OUT: IC1.PB0, IC3.9 (I)
PB1_STROBE: IC1.PB1, IC3.1 (I)
PB2_TPB_ATN: IC1.PB2, IC3.8 (O), R3.1, TPB.5
PB3_TPB_SELECT: IC1.PB3, TPB.6
PB4_TPB_CLK: IC1.PB4, IC3.3 (I)
PB5_TPB_DATA: IC1.PB5, IC3.5 (I)
PB6_TPB_CLK: D3.C, IC1.PB6, IC3.4 (O), R1.1, TPB.1
PB7_TPB_DATA: D1.C, IC1.PB7, IC3.6 (O), R2.1, TPB.3
PD0: CENTRONICS_PORT.3, IC2.18 (B1)
PD1: CENTRONICS_PORT.5, IC2.17 (B2)
PD2: CENTRONICS_PORT.7, IC2.16 (B3)
PD3: CENTRONICS_PORT.9, IC2.15 (B4)
PD4: CENTRONICS_PORT.11, IC2.14 (B5)
PD5: CENTRONICS_PORT.13, IC2.13 (B6)
PD6: CENTRONICS_PORT.15, IC2.12 (B7)
PD7: CENTRONICS_PORT.17, IC2.11 (B8)
PHI2: IC1.PHI2, JP1.20
RDY: JP1.12
RESB: IC1.RESB, JP1.18
RWB: IC1.RWB, JP1.22
STROBE: CENTRONICS_PORT.1, IC3.2 (O), R4.1
VCC: C1.1, C2.1, C3.1, C4.1, C6.+, IC1.CS1, IC1.VDD, IC2.1 (DIR), IC2.20 (VCC), IC3.11 (I), IC3.13 (I), IC3.14 (VCC), IC4.20 (+UB), JP1.2, JP1.4, JP2.1, JP3.1, JP4.1, JP5.1, R1.2, R2.2, R3.2, R4.2, R5.2, TPB.7

Notes on the sheet:
Card Bus
Address Select
Address Decoder
Versatile Interface Adaptor
Centronics Port
Tower Peripheral Bus
Spare Gates

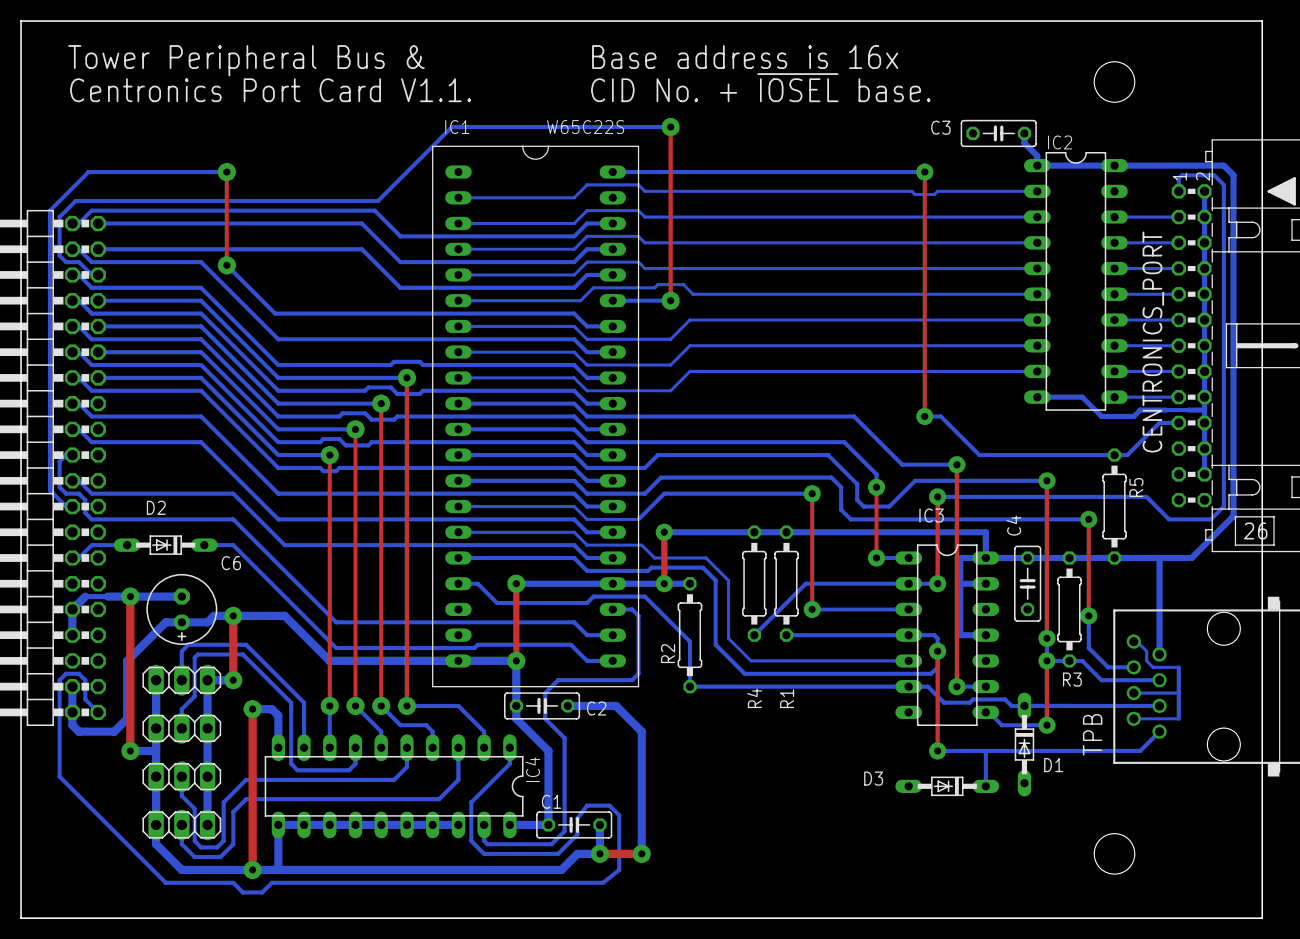
[picture p102: board Bus IO and Centronics Card.brd from above]

Board: 2 copper layers, 124.3 x 88.6 mm, 24 parts (0 on the bottom side), 55 nets.
