JennyDigital/Tower-of-Eightness/Schematics/Serial Card V2/Serial Card V2.brd

## EAGLE design Schematics/Serial Card V2/Serial Card V2.brd (2018-06-14, an earlier design)

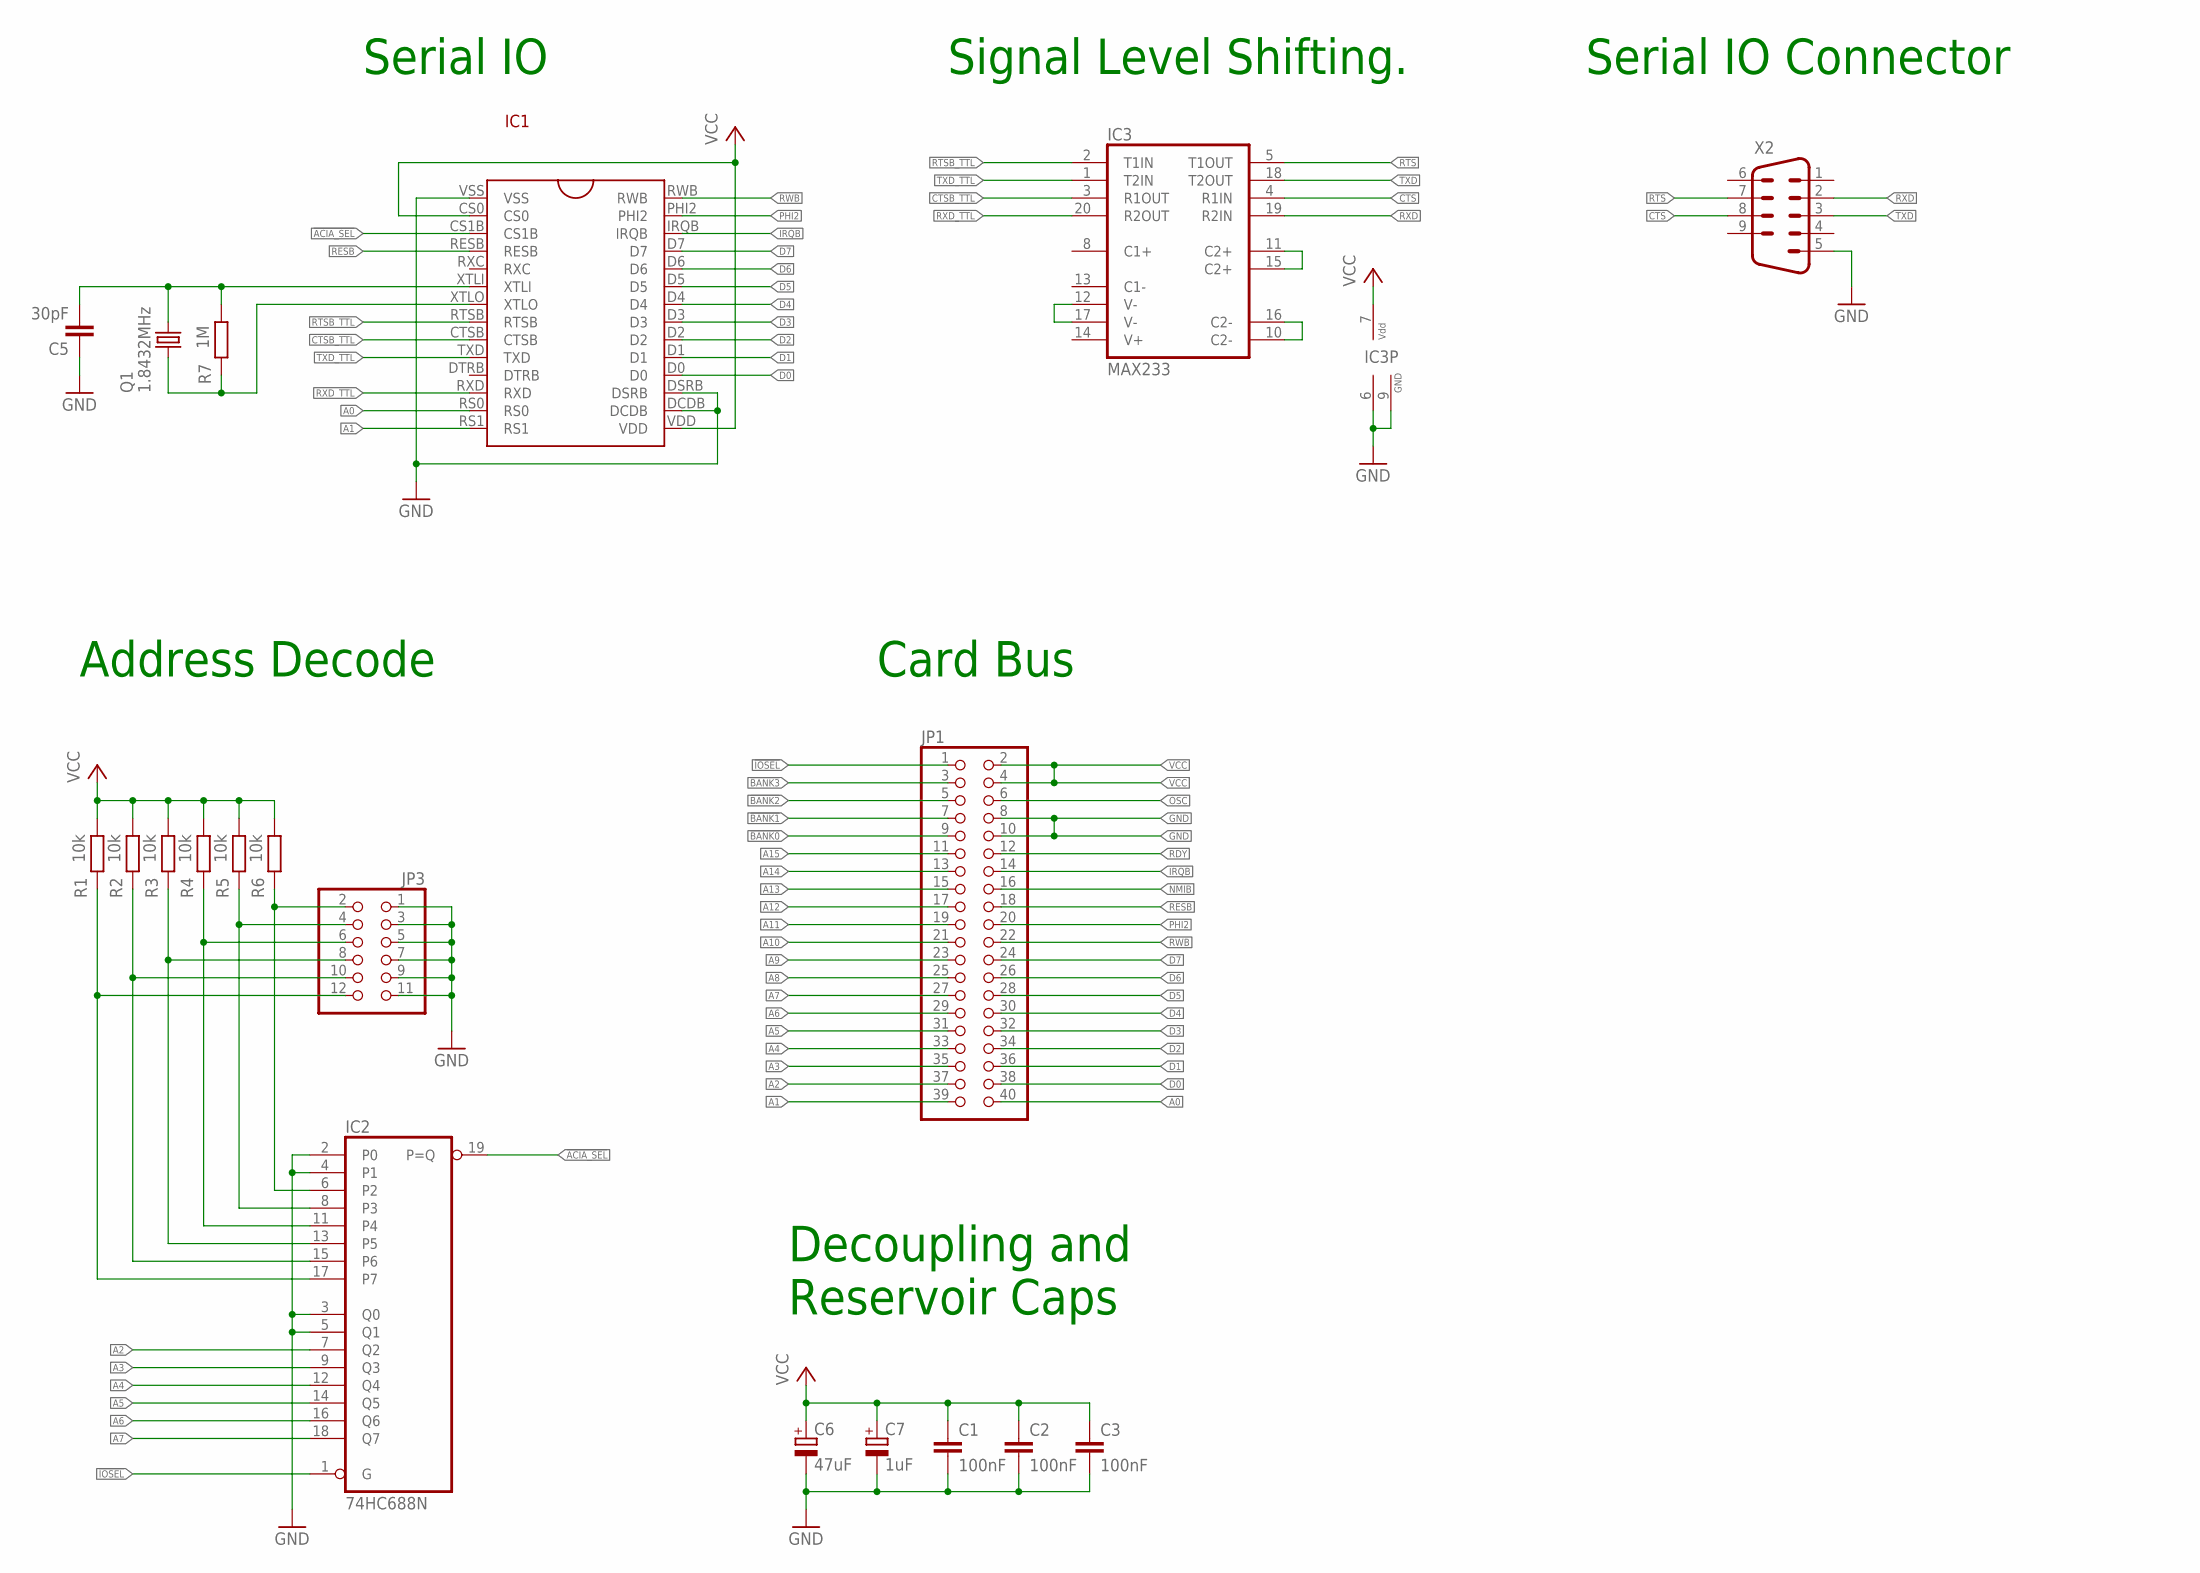
[picture p103: schematic Serial Card V2.sch]

Parts:
C1, C2, C3: 100nF; C050-025X075
C5: 30pF; C050-025X075
C6: 47uF; E2,5-7
C7: 1uF; E2,5-5
IC1: W65C51N-DIP
IC2: 74HC688N; DIL20
IC3: MAX233; DIL20
JP1: PINHD-2X20/90; 2X20/90
JP3: PINHD-2X6; 2X06
Q1: 1.8432MHz; HC49/S
R1, R2, R3, R4, R5, R6: 10k; 0207/2V
R7: 1M; 0207/2V
X2: M09HP

Connections:
!ACIA_SEL: IC1.CS1B, IC2.19 (P=Q)
!BANK0: JP1.9
!BANK1: JP1.7
!BANK2: JP1.5
!BANK3: JP1.3
!IOSEL: IC2.1 (G), JP1.1
A0: IC1.RS0, JP1.40
A1: IC1.RS1, JP1.39
A2: IC2.7 (Q2), JP1.37
A3: IC2.9 (Q3), JP1.35
A4: IC2.12 (Q4), JP1.33
A5: IC2.14 (Q5), JP1.31
A6: IC2.16 (Q6), JP1.29
A7: IC2.18 (Q7), JP1.27
A8: JP1.25
A9: JP1.23
A10: JP1.21
A11: JP1.19
A12: JP1.17
A13: JP1.15
A14: JP1.13
A15: JP1.11
CTS: IC3.4 (R1IN), X2.8
CTSB_TTL: IC1.CTSB, IC3.3 (R1OUT)
D0: IC1.D0, JP1.38
D1: IC1.D1, JP1.36
D2: IC1.D2, JP1.34
D3: IC1.D3, JP1.32
D4: IC1.D4, JP1.30
D5: IC1.D5, JP1.28
D6: IC1.D6, JP1.26
D7: IC1.D7, JP1.24
GND: C1.2, C2.2, C3.2, C5.1, C6.-, C7.-, IC1.DCDB, IC1.DSRB, IC1.VSS, IC2.2 (P0), IC2.3 (Q0), IC2.4 (P1), IC2.5 (Q1), IC2.10 (GND), IC3.6 (GND), IC3.9 (GND), JP1.8, JP1.10, JP3.1, JP3.3, JP3.5, JP3.7, JP3.9, JP3.11, X2.5
IRQB: IC1.IRQB, JP1.14
unnamed: C5.2, IC1.XTLI, Q1.2, R7.2
unnamed: IC1.XTLO, Q1.1, R7.1
unnamed: IC3.12 (V-), IC3.17 (V-)
unnamed: IC3.11 (C2+), IC3.15 (C2+)
unnamed: IC3.10 (C2-), IC3.16 (C2-)
NMIB: JP1.16
OSC: JP1.6
P2: IC2.6 (P2), JP3.2, R6.1
P3: IC2.8 (P3), JP3.4, R5.1
P4: IC2.11 (P4), JP3.6, R4.1
P5: IC2.13 (P5), JP3.8, R3.1
P6: IC2.15 (P6), JP3.10, R2.1
P7: IC2.17 (P7), JP3.12, R1.1
PHI2: IC1.PHI2, JP1.20
RDY: JP1.12
RESB: IC1.RESB, JP1.18
RTS: IC3.5 (T1OUT), X2.7
RTSB_TTL: IC1.RTSB, IC3.2 (T1IN)
RWB: IC1.RWB, JP1.22
RXD: IC3.19 (R2IN), X2.2
RXD_TTL: IC1.RXD, IC3.20 (R2OUT)
TXD: IC3.18 (T2OUT), X2.3
TXD_TTL: IC1.TXD, IC3.1 (T2IN)
VCC: C1.1, C2.1, C3.1, C6.+, C7.+, IC1.CS0, IC1.VDD, IC2.20 (VCC), IC3.7 (VDD), JP1.2, JP1.4, R1.2, R2.2, R3.2, R4.2, R5.2, R6.2

Notes on the sheet:
Card Bus
Decoupling and Reservoir Caps
Address Decode
Serial IO
Signal Level Shifting.
Serial IO Connector

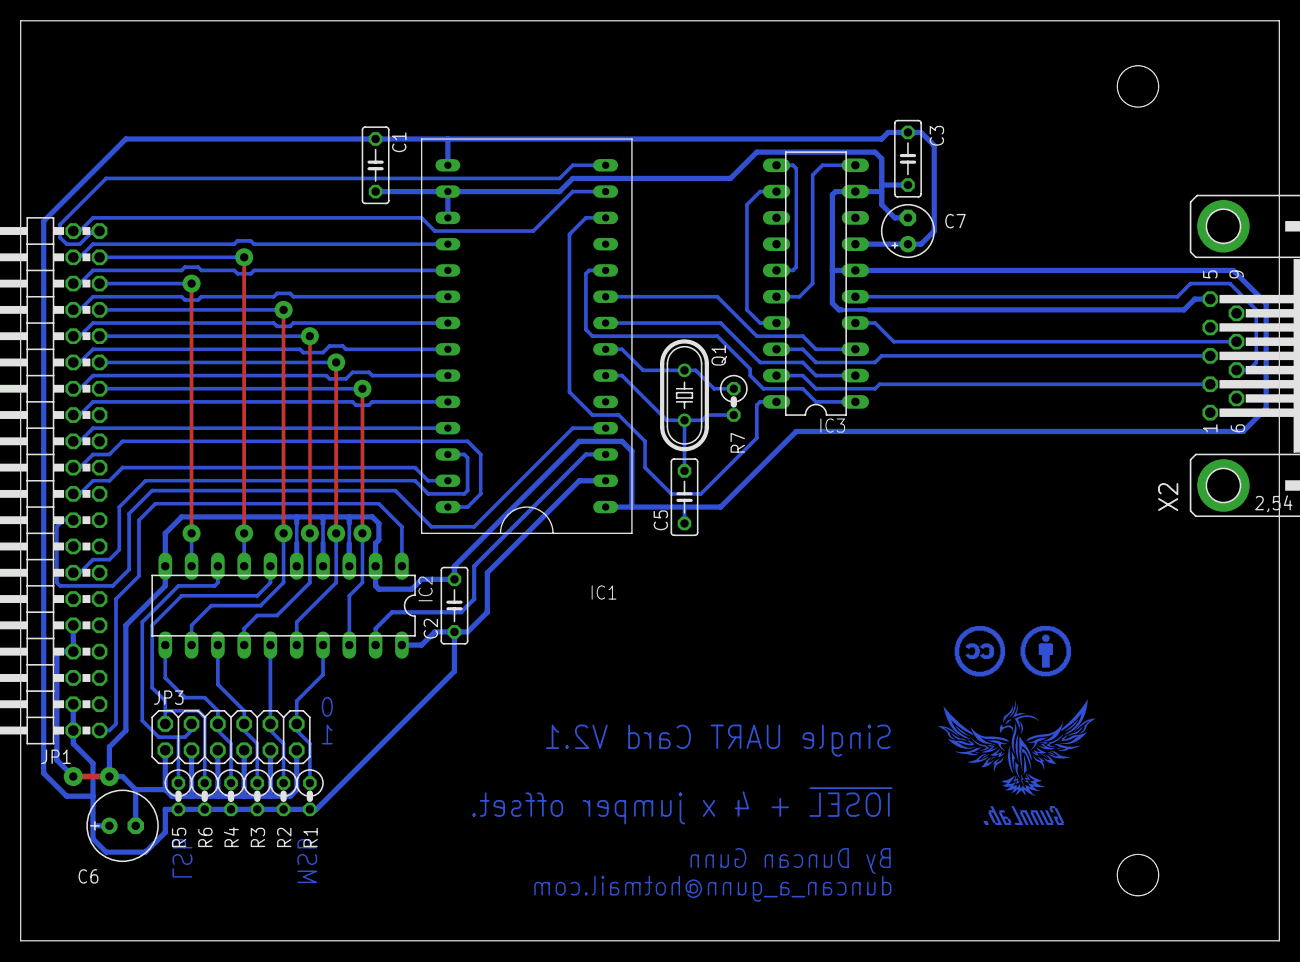
[picture p104: board Serial Card V2.brd from above]

Board: 2 copper layers, 121.6 x 88.9 mm, 23 parts (0 on the bottom side), 43 nets.

Other parts of the board:
U$1: LIONTECH
U$2: BY
U$3: CC
