JennyDigital/Tower-of-Eightness/Schematics/Bus-IO-Dev-Simulator/Bus IO Device Simulator.brd

## EAGLE design Schematics/Bus-IO-Dev-Simulator/Bus IO Device Simulator.brd (2018-06-14)

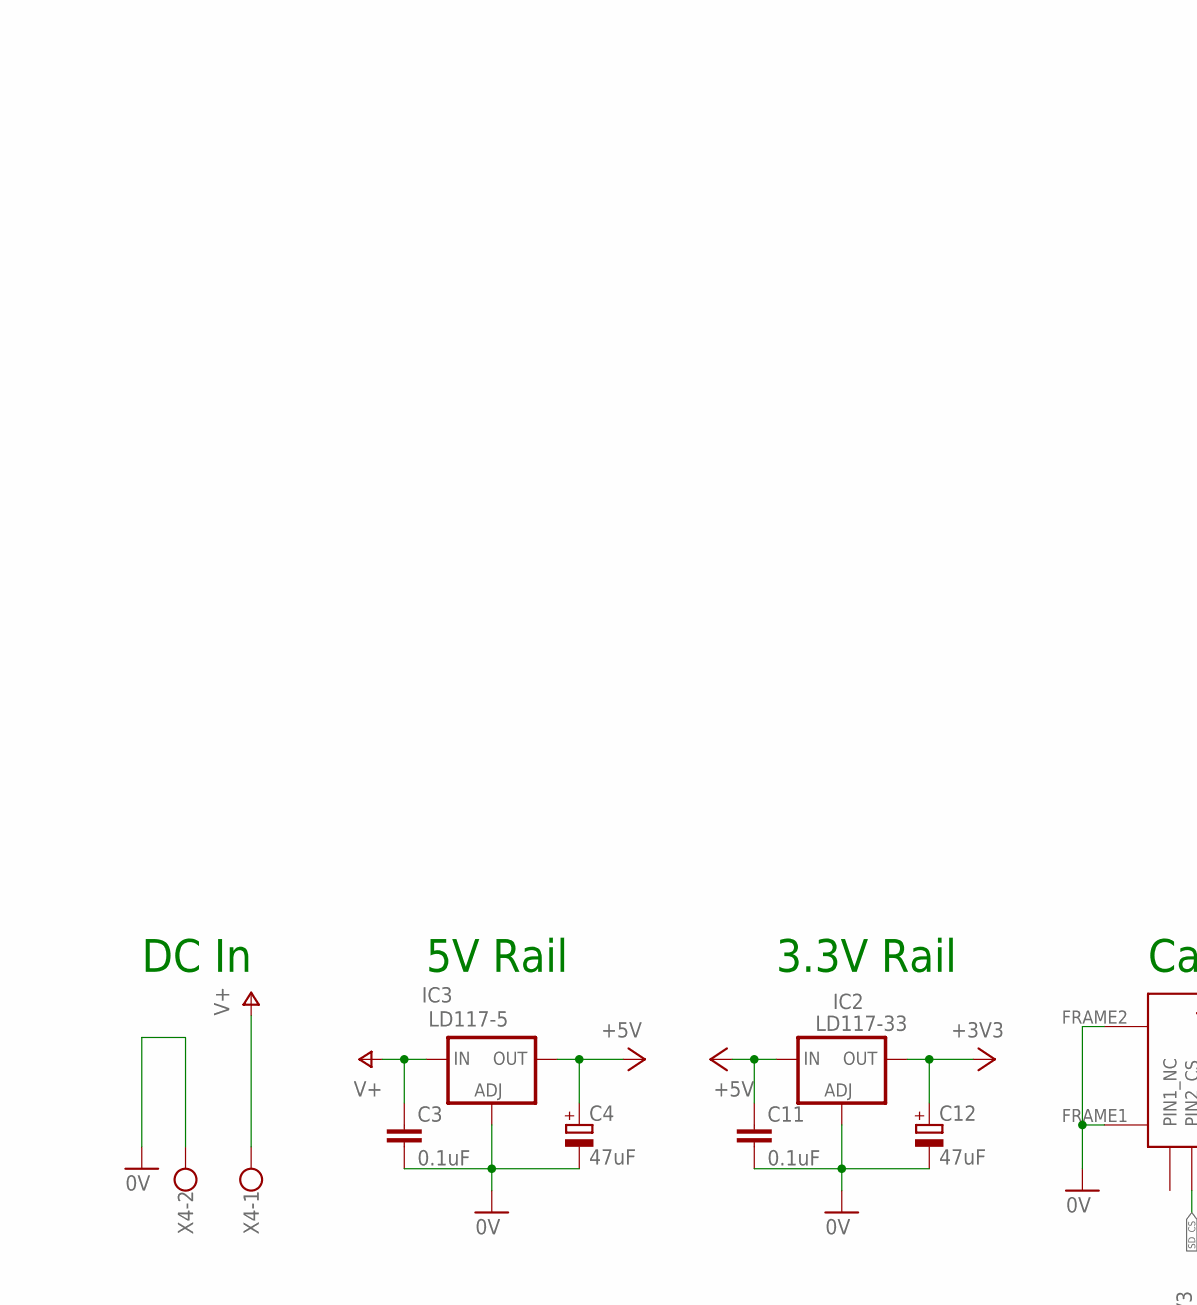
[picture p105: schematic Bus IO Device Simulator.sch, part in row 1, column 1]

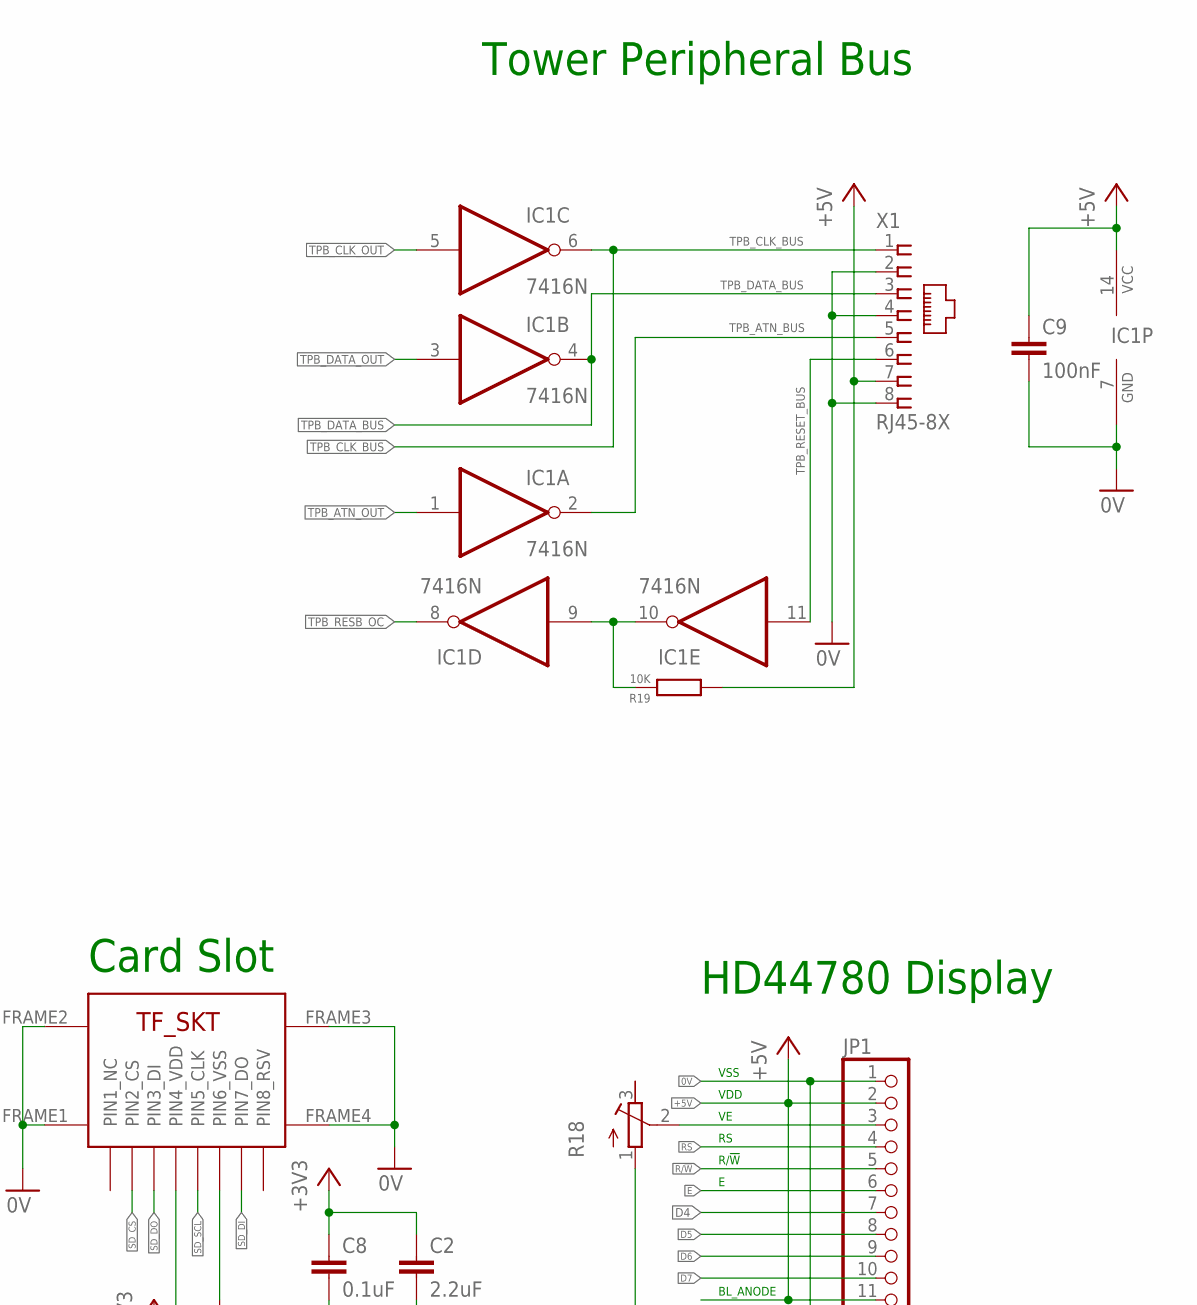
[picture p106: schematic Bus IO Device Simulator.sch, part in row 1, column 2]

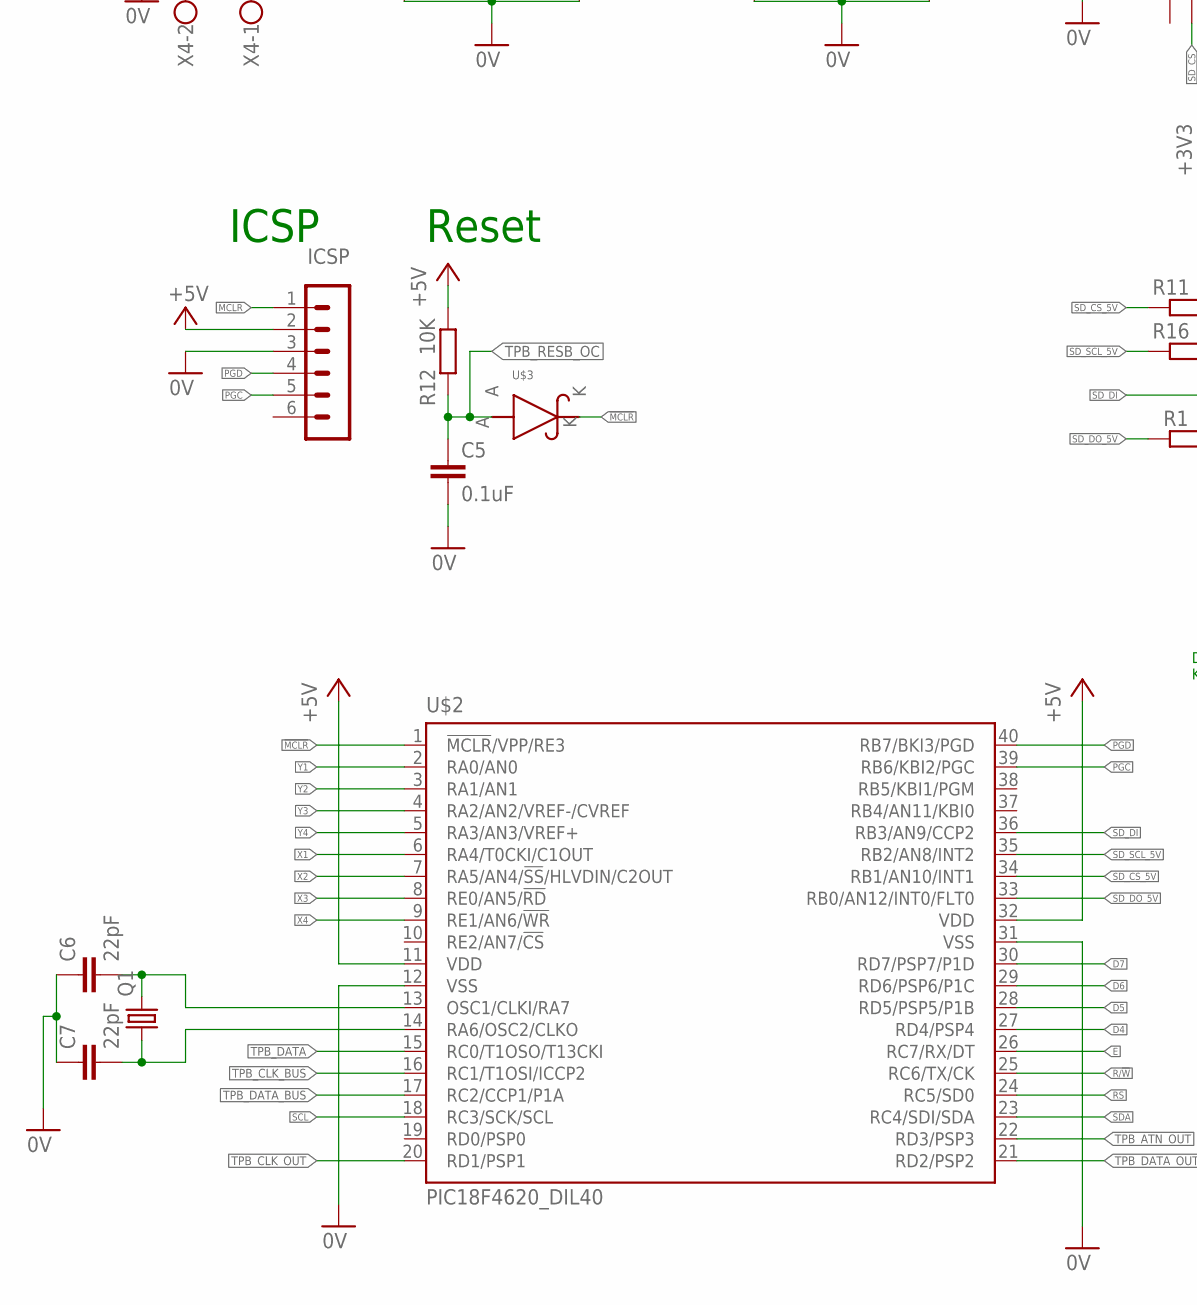
[picture p107: schematic Bus IO Device Simulator.sch, part in row 2, column 1]

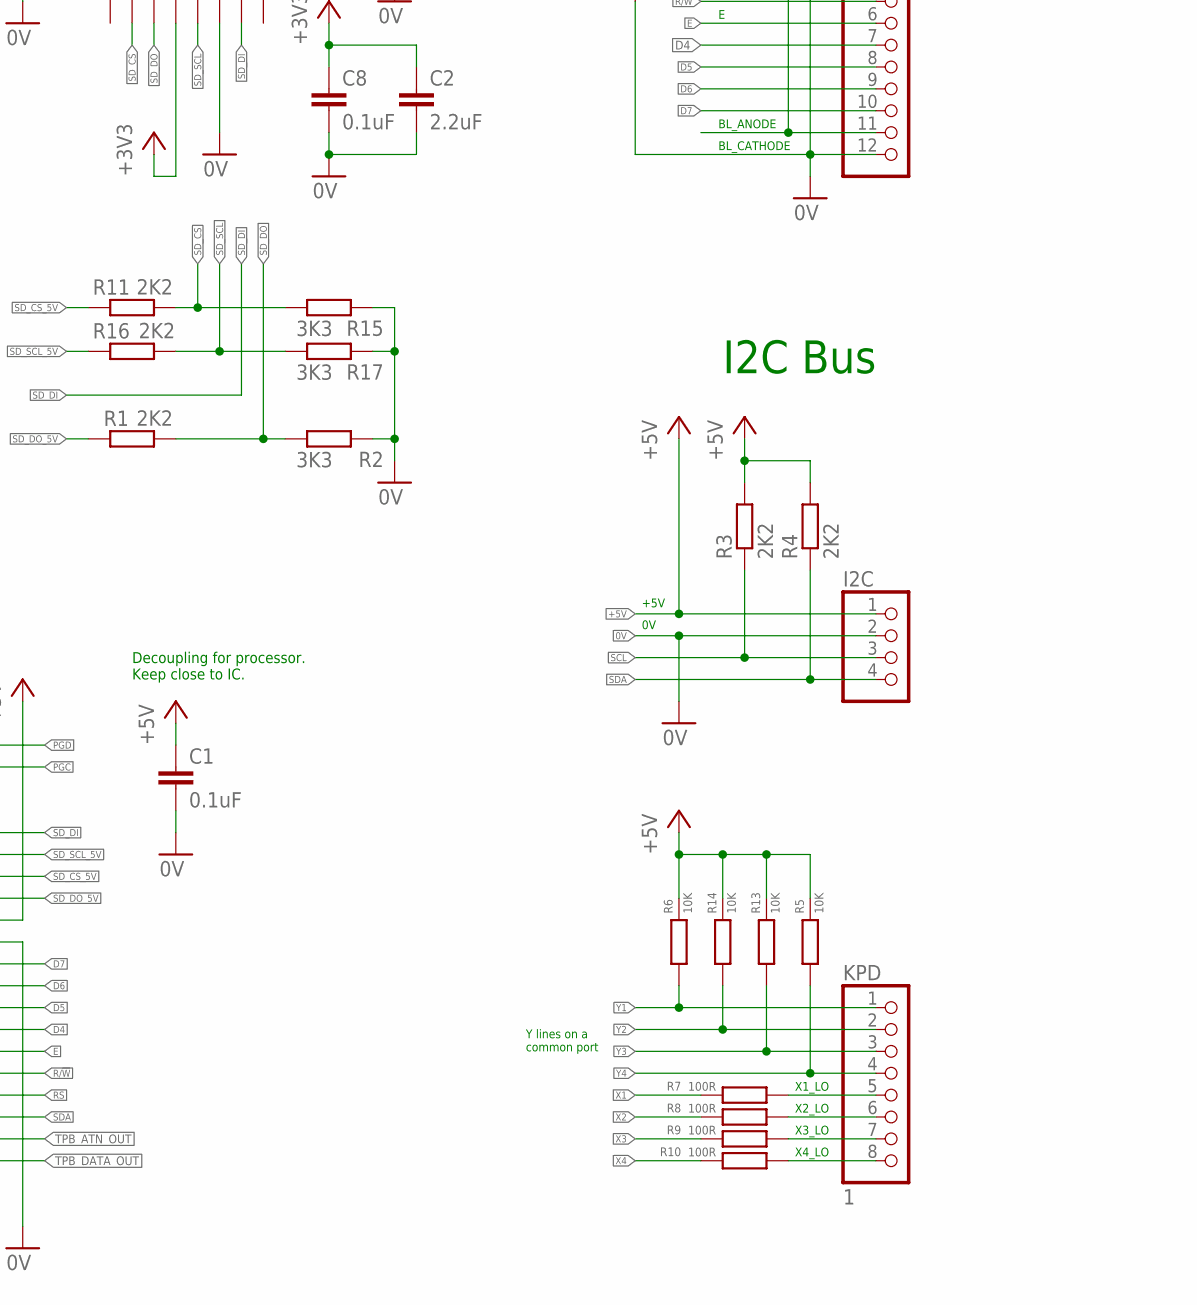
[picture p108: schematic Bus IO Device Simulator.sch, part in row 2, column 2]

Parts:
C1, C3, C5, C8, C11: 0.1uF; C0603
C2: 2.2uF; C1206
C4, C12: 47uF; SMC_D
C6, C7: 22pF; C0603
C9: 100nF; C050-025X075
I2C: PINHD-1X4; 1X04
IC1: 7416N; DIL14
IC2: LD117-33; SOT223
IC3: LD117-5; SOT223
ICSP: MA06-1
JP1: PINHD-1X12; 1X12
KPD: 1; 1X08
Q1: CRYSTALHC49U-V; HC49U-V
R1, R3, R4, R11, R16: 2K2; R0603
R2, R15, R17: 3K3; R0603
R5, R6, R12, R13, R14, R19: 10K; R0603
R7, R8, R9, R10: 100R; R0603
R18: R-TRIMM64W; RTRIM64W
U$1: TF_SKT; CLIP_DOWN
U$2: PIC18F4620_DIL40; DIL40
U$3: ZHCS750; SOT23
X1: RJ45-8X; RJ45-NO-SHIELD
X4: W237-102; MPN 237-102

Connections:
0V: C1.2, C2.2, C3.2, C4.-, C5.2, C6.1, C7.1, C8.2, C9.2, C11.2, C12.-, I2C.2, IC1.7 (GND), IC2.1 (ADJ), IC3.1 (ADJ), ICSP.3, JP1.1, JP1.12, R2.1, R15.1, R17.1, R18.1 (E), U$1.FRAME1, U$1.FRAME2, U$1.FRAME3, U$1.FRAME4, U$1.PIN6_VSS, U$2.12 (VSS), U$2.31 (VSS), X1.2, X1.4, X1.8, X4.2
!MCLR: ICSP.1, U$2.1 (!MCLR!/VPP/RE3), U$3.K
+3V3: C2.1, C8.1, C12.+, IC2.4 (OUT), U$1.PIN4_VDD
+5V: C1.1, C4.+, C9.1, C11.1, I2C.1, IC1.14 (VCC), IC2.3 (IN), IC3.4 (OUT), ICSP.2, JP1.2, JP1.11, R3.2, R4.2, R5.2, R6.2, R12.2, R13.2, R14.2, R19.1, U$2.11 (VDD), U$2.32 (VDD), X1.7
D4: JP1.7, U$2.27 (RD4/PSP4)
D5: JP1.8, U$2.28 (RD5/PSP5/P1B)
D6: JP1.9, U$2.29 (RD6/PSP6/P1C)
D7: JP1.10, U$2.30 (RD7/PSP7/P1D)
E: JP1.6, U$2.26 (RC7/RX/DT)
unnamed: C6.2, Q1.2, U$2.13 (OSC1/CLKI/RA7)
unnamed: C7.2, Q1.1, U$2.14 (RA6/OSC2/CLKO)
unnamed: JP1.3, R18.2 (S)
unnamed: IC1.9 (I), IC1.10 (O), R19.2
PGC: ICSP.5, U$2.39 (RB6/KBI2/PGC)
PGD: ICSP.4, U$2.40 (RB7/BKI3/PGD)
R/!W: JP1.5, U$2.25 (RC6/TX/CK)
RS: JP1.4, U$2.24 (RC5/SD0)
SCL: I2C.3, R3.1, U$2.18 (RC3/SCK/SCL)
SDA: I2C.4, R4.1, U$2.23 (RC4/SDI/SDA)
SD_CS: R11.1, R15.2, U$1.PIN2_CS
SD_CS_5V: R11.2, U$2.34 (RB1/AN10/INT1)
SD_DI: U$1.PIN7_DO, U$2.36 (RB3/AN9/CCP2)
SD_DO: R1.1, R2.2, U$1.PIN3_DI
SD_DO_5V: R1.2, U$2.33 (RB0/AN12/INT0/FLT0)
SD_SCL: R16.1, R17.2, U$1.PIN5_CLK
SD_SCL_5V: R16.2, U$2.35 (RB2/AN8/INT2)
TPB_ATN_BUS: IC1.2 (O), X1.5
TPB_ATN_OUT: IC1.1 (I), U$2.22 (RD3/PSP3)
TPB_CLK_BUS: IC1.6 (O), U$2.16 (RC1/T1OSI/ICCP2), X1.1
TPB_CLK_OUT: IC1.5 (I), U$2.20 (RD1/PSP1)
TPB_DATA: U$2.15 (RC0/T1OSO/T13CKI)
TPB_DATA_BUS: IC1.4 (O), U$2.17 (RC2/CCP1/P1A), X1.3
TPB_DATA_OUT: IC1.3 (I), U$2.21 (RD2/PSP2)
TPB_RESB_OC: C5.1, IC1.8 (O), R12.1, U$3.A
TPB_RESET_BUS: IC1.11 (I), X1.6
V+: C3.1, IC3.3 (IN), X4.1
X1: R7.2, U$2.6 (RA4/T0CKI/C1OUT)
X1_LO: KPD.5, R7.1
X2: R8.2, U$2.7 (RA5/AN4/!SS!/HLVDIN/C2OUT)
X2_LO: KPD.6, R8.1
X3: R9.2, U$2.8 (RE0/AN5/!RD)
X3_LO: KPD.7, R9.1
X4: R10.2, U$2.9 (RE1/AN6/!WR)
X4_LO: KPD.8, R10.1
Y1: KPD.1, R6.1, U$2.2 (RA0/AN0)
Y2: KPD.2, R14.1, U$2.3 (RA1/AN1)
Y3: KPD.3, R13.1, U$2.4 (RA2/AN2/VREF-/CVREF)
Y4: KPD.4, R5.1, U$2.5 (RA3/AN3/VREF+)

Notes on the sheet:
5V Rail
DC In
Reset
Card Slot
3.3V Rail
Decoupling for processor. Keep close to IC.
HD44780 Display
VSS
VDD
R/!W
BL_ANODE
BL_CATHODE
ICSP
I2C Bus
+5V
X1_LO
X2_LO
X3_LO
X4_LO
Y lines on a common port
Tower Peripheral Bus

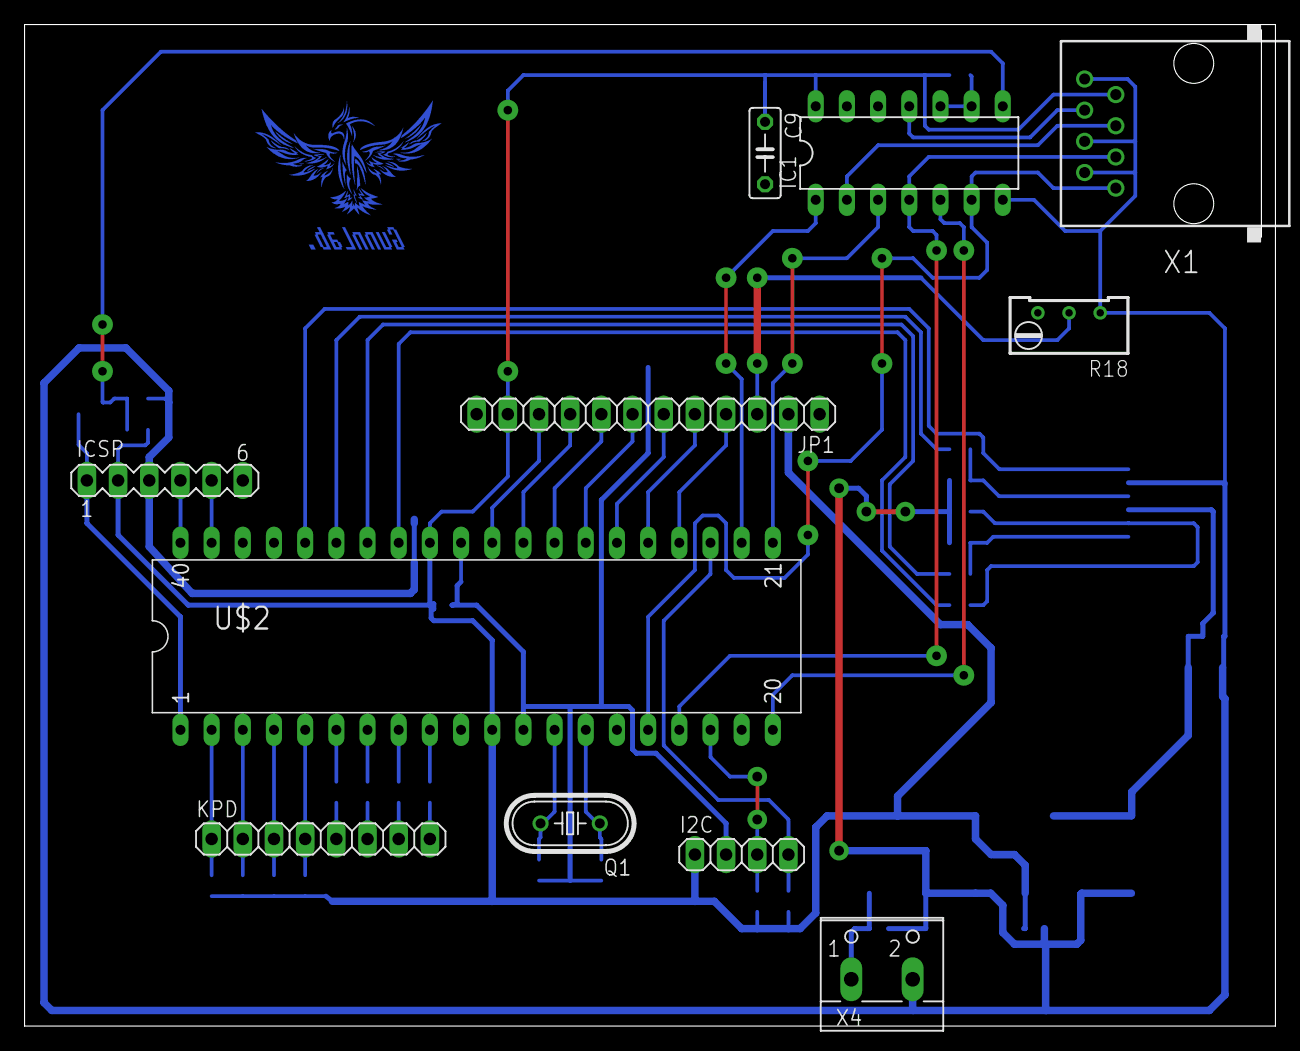
[picture p109: board Bus IO Device Simulator.brd from above]

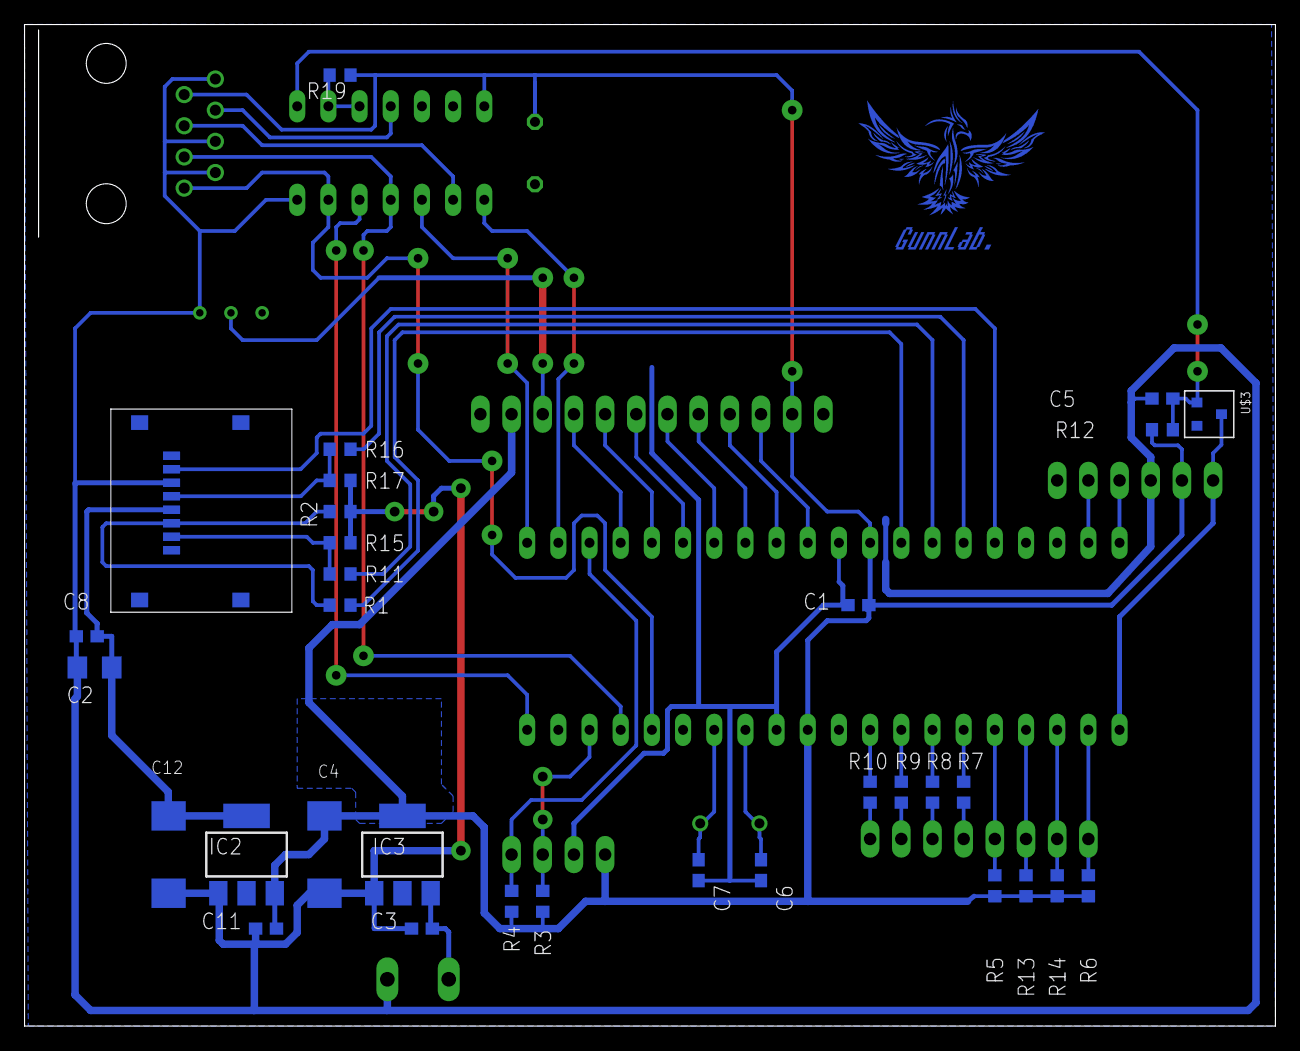
[picture p110: board Bus IO Device Simulator.brd from below]

Board: 2 copper layers, 101.9 x 81.6 mm, 44 parts (32 on the bottom side), 47 nets.

Other parts of the board:
U$4: LIONTECH
