JennyDigital/Tower-of-Eightness/Schematics/Serial Card V3/Serial Card V3.brd

## EAGLE design Schematics/Serial Card V3/Serial Card V3.brd (2018-06-14)

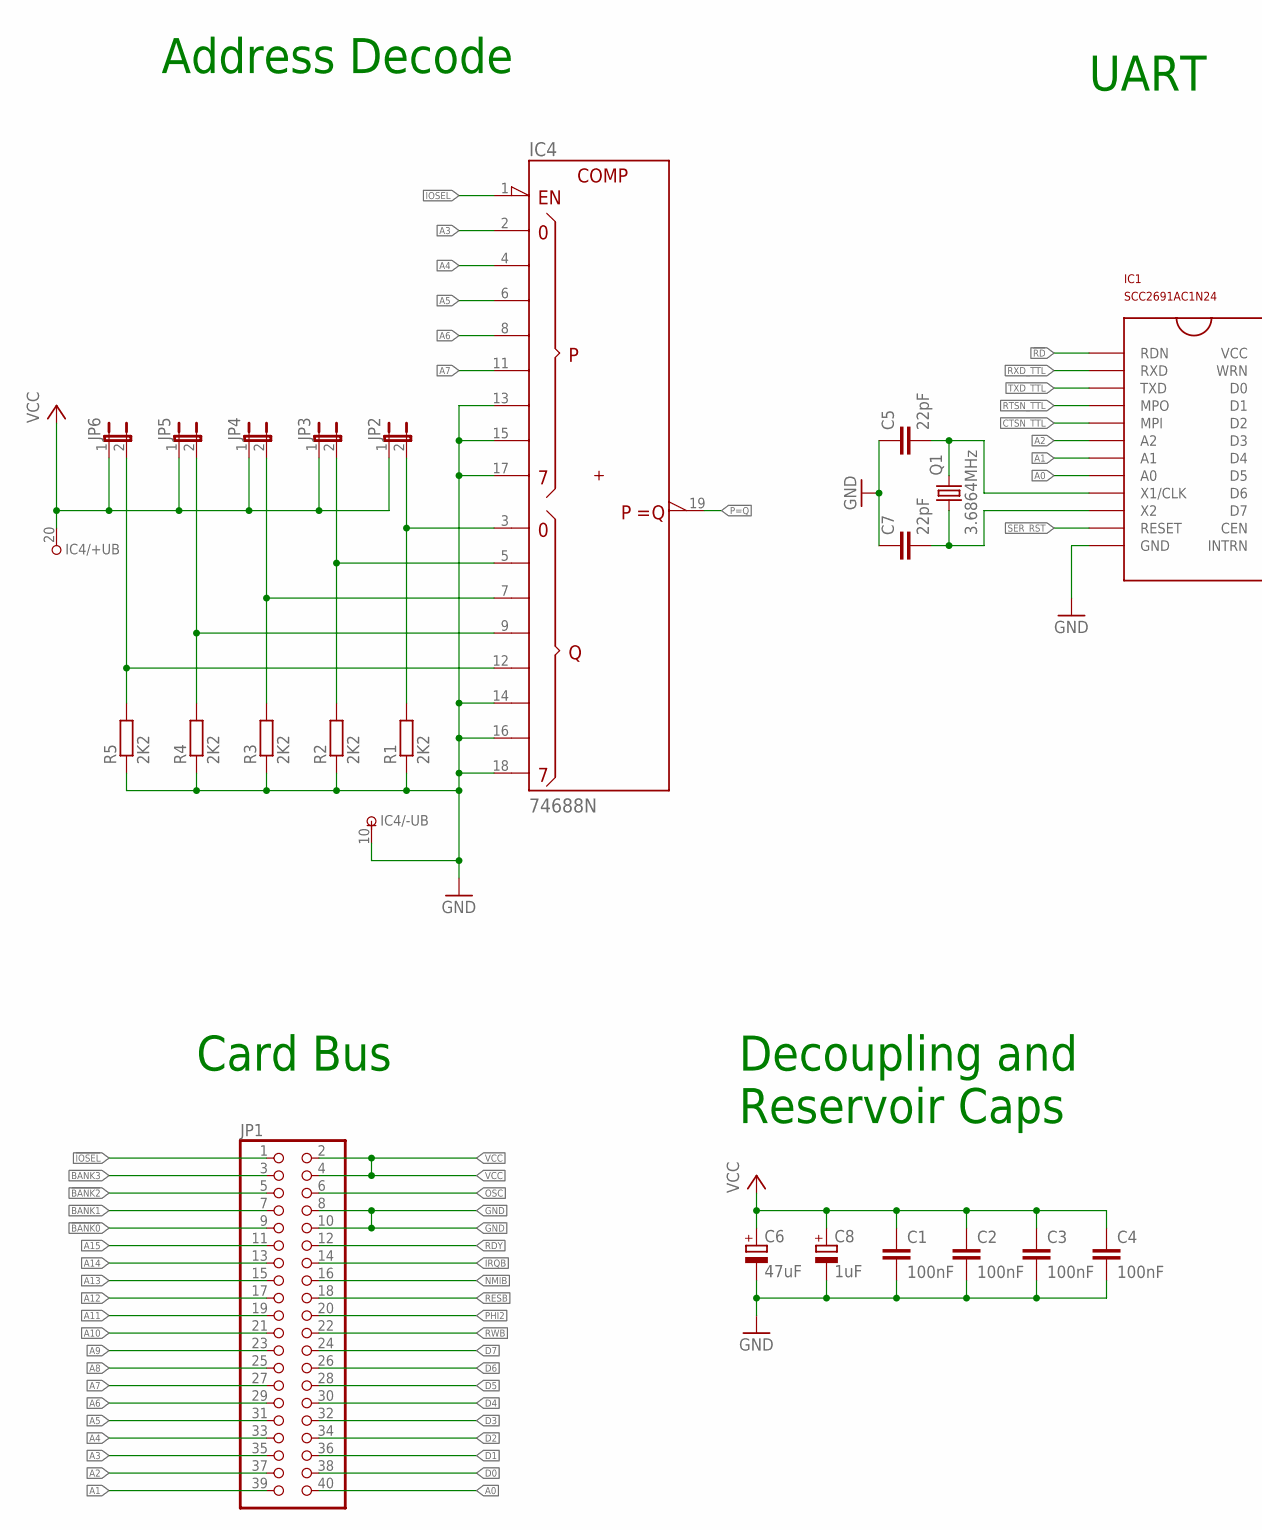
[picture p111: schematic Serial Card V3.sch, part in row 1, column 1]

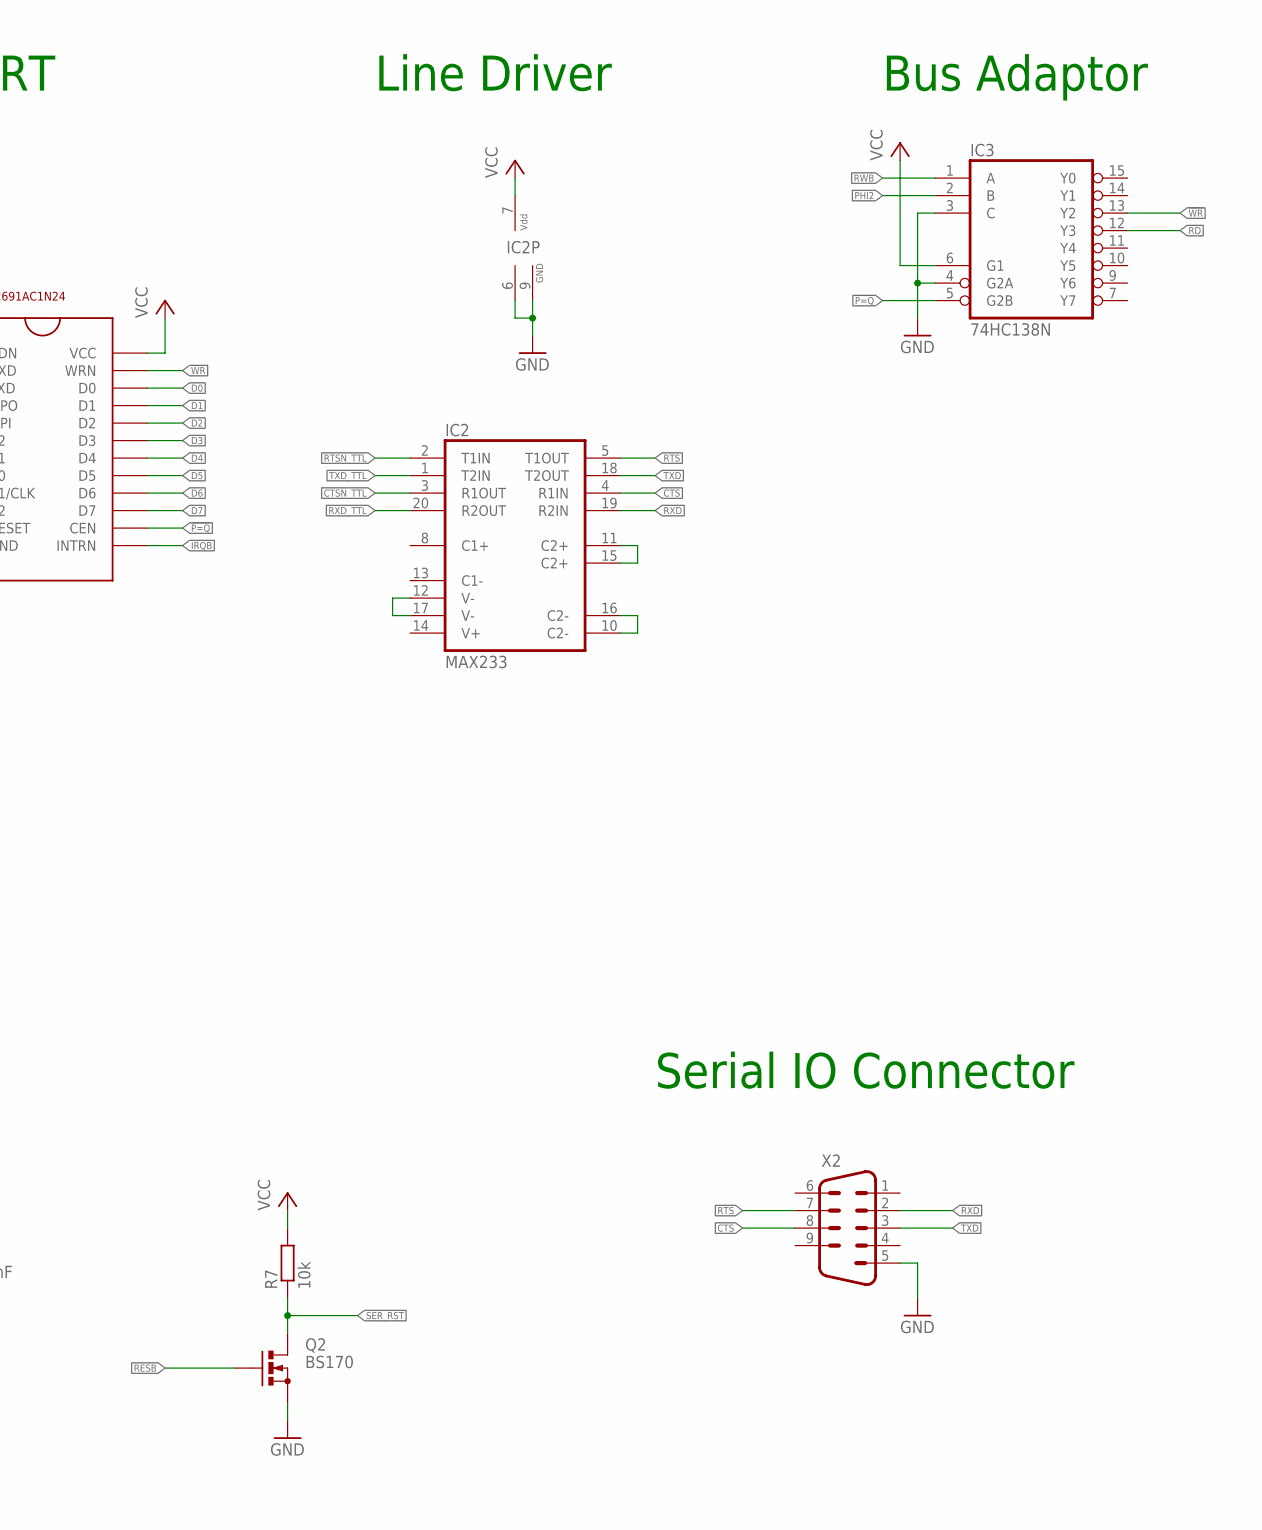
[picture p112: schematic Serial Card V3.sch, part in row 1, column 2]

Parts:
C1, C2, C3, C4: 100nF; C050-025X075
C5, C7: 22pF; C025-024X044
C6: 47uF; E2,5-7
C8: 1uF; E5-5
IC1: SCC2691AC1N24; DIP
IC2: MAX233; DIL20
IC3: 74HC138N; DIL16
IC4: 74688N; DIL20
JP1: PINHD-2X20/90; 2X20/90
JP2, JP3, JP4, JP5, JP6: JP1E; JP1
Q1: 3.6864MHz; HC49/S
Q2: BS170; SOT54E
R1, R2, R3, R4, R5: 2K2; 0207/2V
R7: 10k; 0207/2V
X2: M09HP

Connections:
!BANK0: JP1.9
!BANK1: JP1.7
!BANK2: JP1.5
!BANK3: JP1.3
!IOSEL: IC4.1 (!G), JP1.1
!P=Q: IC1.CEN, IC3.5 (G2B), IC4.19 (!P=Q)
!RD: IC1.RDN, IC3.12 (Y3)
!WR: IC1.WRN, IC3.13 (Y2)
A0: IC1.A0, JP1.40
A1: IC1.A1, JP1.39
A2: IC1.A2, JP1.37
A3: IC4.2 (P0), JP1.35
A4: IC4.4 (P1), JP1.33
A5: IC4.6 (P2), JP1.31
A6: IC4.8 (P3), JP1.29
A7: IC4.11 (P4), JP1.27
A8: JP1.25
A9: JP1.23
A10: JP1.21
A11: JP1.19
A12: JP1.17
A13: JP1.15
A14: JP1.13
A15: JP1.11
CTS: IC2.4 (R1IN), X2.8
CTSN_TTL: IC1.MPI, IC2.3 (R1OUT)
D0: IC1.D0, JP1.38
D1: IC1.D1, JP1.36
D2: IC1.D2, JP1.34
D3: IC1.D3, JP1.32
D4: IC1.D4, JP1.30
D5: IC1.D5, JP1.28
D6: IC1.D6, JP1.26
D7: IC1.D7, JP1.24
GND: C1.2, C2.2, C3.2, C4.2, C5.1, C6.-, C7.1, C8.-, IC1.GND, IC2.6 (GND), IC2.9 (GND), IC3.3 (C), IC3.4 (G2A), IC3.8 (GND), IC4.10 (-UB), IC4.13 (P5), IC4.14 (Q5), IC4.15 (P6), IC4.16 (Q6), IC4.17 (P7), IC4.18 (Q7), JP1.8, JP1.10, Q2.S, R1.1, R2.1, R3.1, R4.1, R5.1, X2.5
IRQB: IC1.INTRN, JP1.14
unnamed: C5.2, IC1.X1/CLK, Q1.2
unnamed: C7.2, IC1.X2, Q1.1
unnamed: IC4.3 (Q0), JP2.2, R1.2
unnamed: IC4.5 (Q1), JP3.2, R2.2
unnamed: IC4.7 (Q2), JP4.2, R3.2
unnamed: IC4.9 (Q3), JP5.2, R4.2
unnamed: IC4.12 (Q4), JP6.2, R5.2
unnamed: IC2.11 (C2+), IC2.15 (C2+)
unnamed: IC2.10 (C2-), IC2.16 (C2-)
unnamed: IC2.12 (V-), IC2.17 (V-)
NMIB: JP1.16
OSC: JP1.6
PHI2: IC3.2 (B), JP1.20
RDY: JP1.12
RESB: JP1.18, Q2.G
RTS: IC2.5 (T1OUT), X2.7
RTSN_TTL: IC1.MPO, IC2.2 (T1IN)
RWB: IC3.1 (A), JP1.22
RXD: IC2.19 (R2IN), X2.2
RXD_TTL: IC1.RXD, IC2.20 (R2OUT)
SER_RST: IC1.RESET, Q2.D, R7.1
TXD: IC2.18 (T2OUT), X2.3
TXD_TTL: IC1.TXD, IC2.1 (T2IN)
VCC: C1.1, C2.1, C3.1, C4.1, C6.+, C8.+, IC1.VCC, IC2.7 (VDD), IC3.6 (G1), IC3.16 (VCC), IC4.20 (+UB), JP1.2, JP1.4, JP2.1, JP3.1, JP4.1, JP5.1, JP6.1, R7.2

Notes on the sheet:
Card Bus
Decoupling and Reservoir Caps
Serial IO Connector
Address Decode
UART
Line Driver
Bus Adaptor

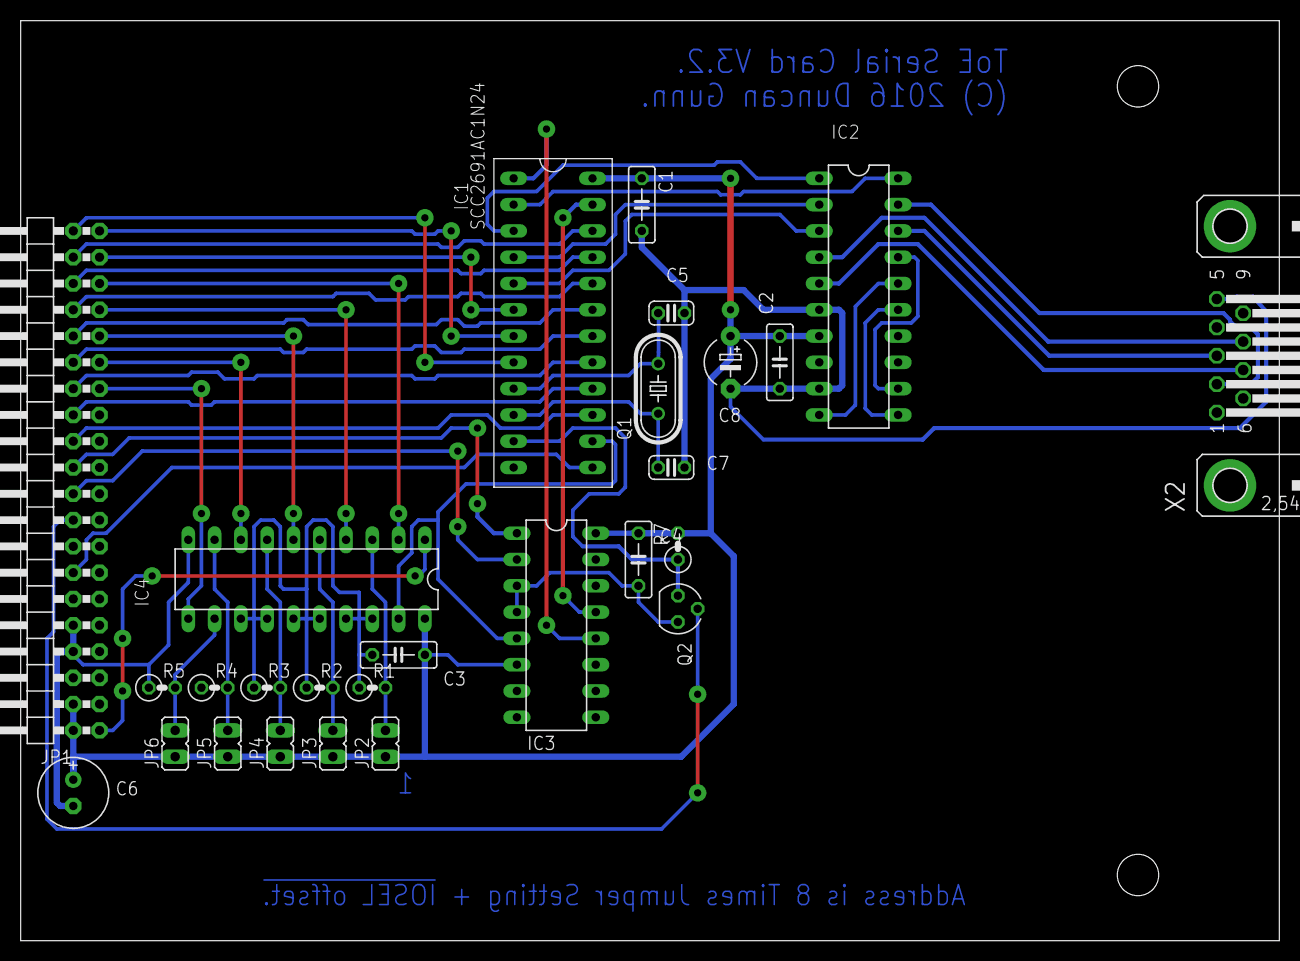
[picture p113: board Serial Card V3.brd from above]

Board: 2 copper layers, 121.6 x 88.9 mm, 27 parts (0 on the bottom side), 45 nets.
