JennyDigital/Tower-of-Eightness/Schematics/Versatile-IO-Card/Versatile IO Card.brd

## EAGLE design Schematics/Versatile-IO-Card/Versatile IO Card.brd (2018-06-14)

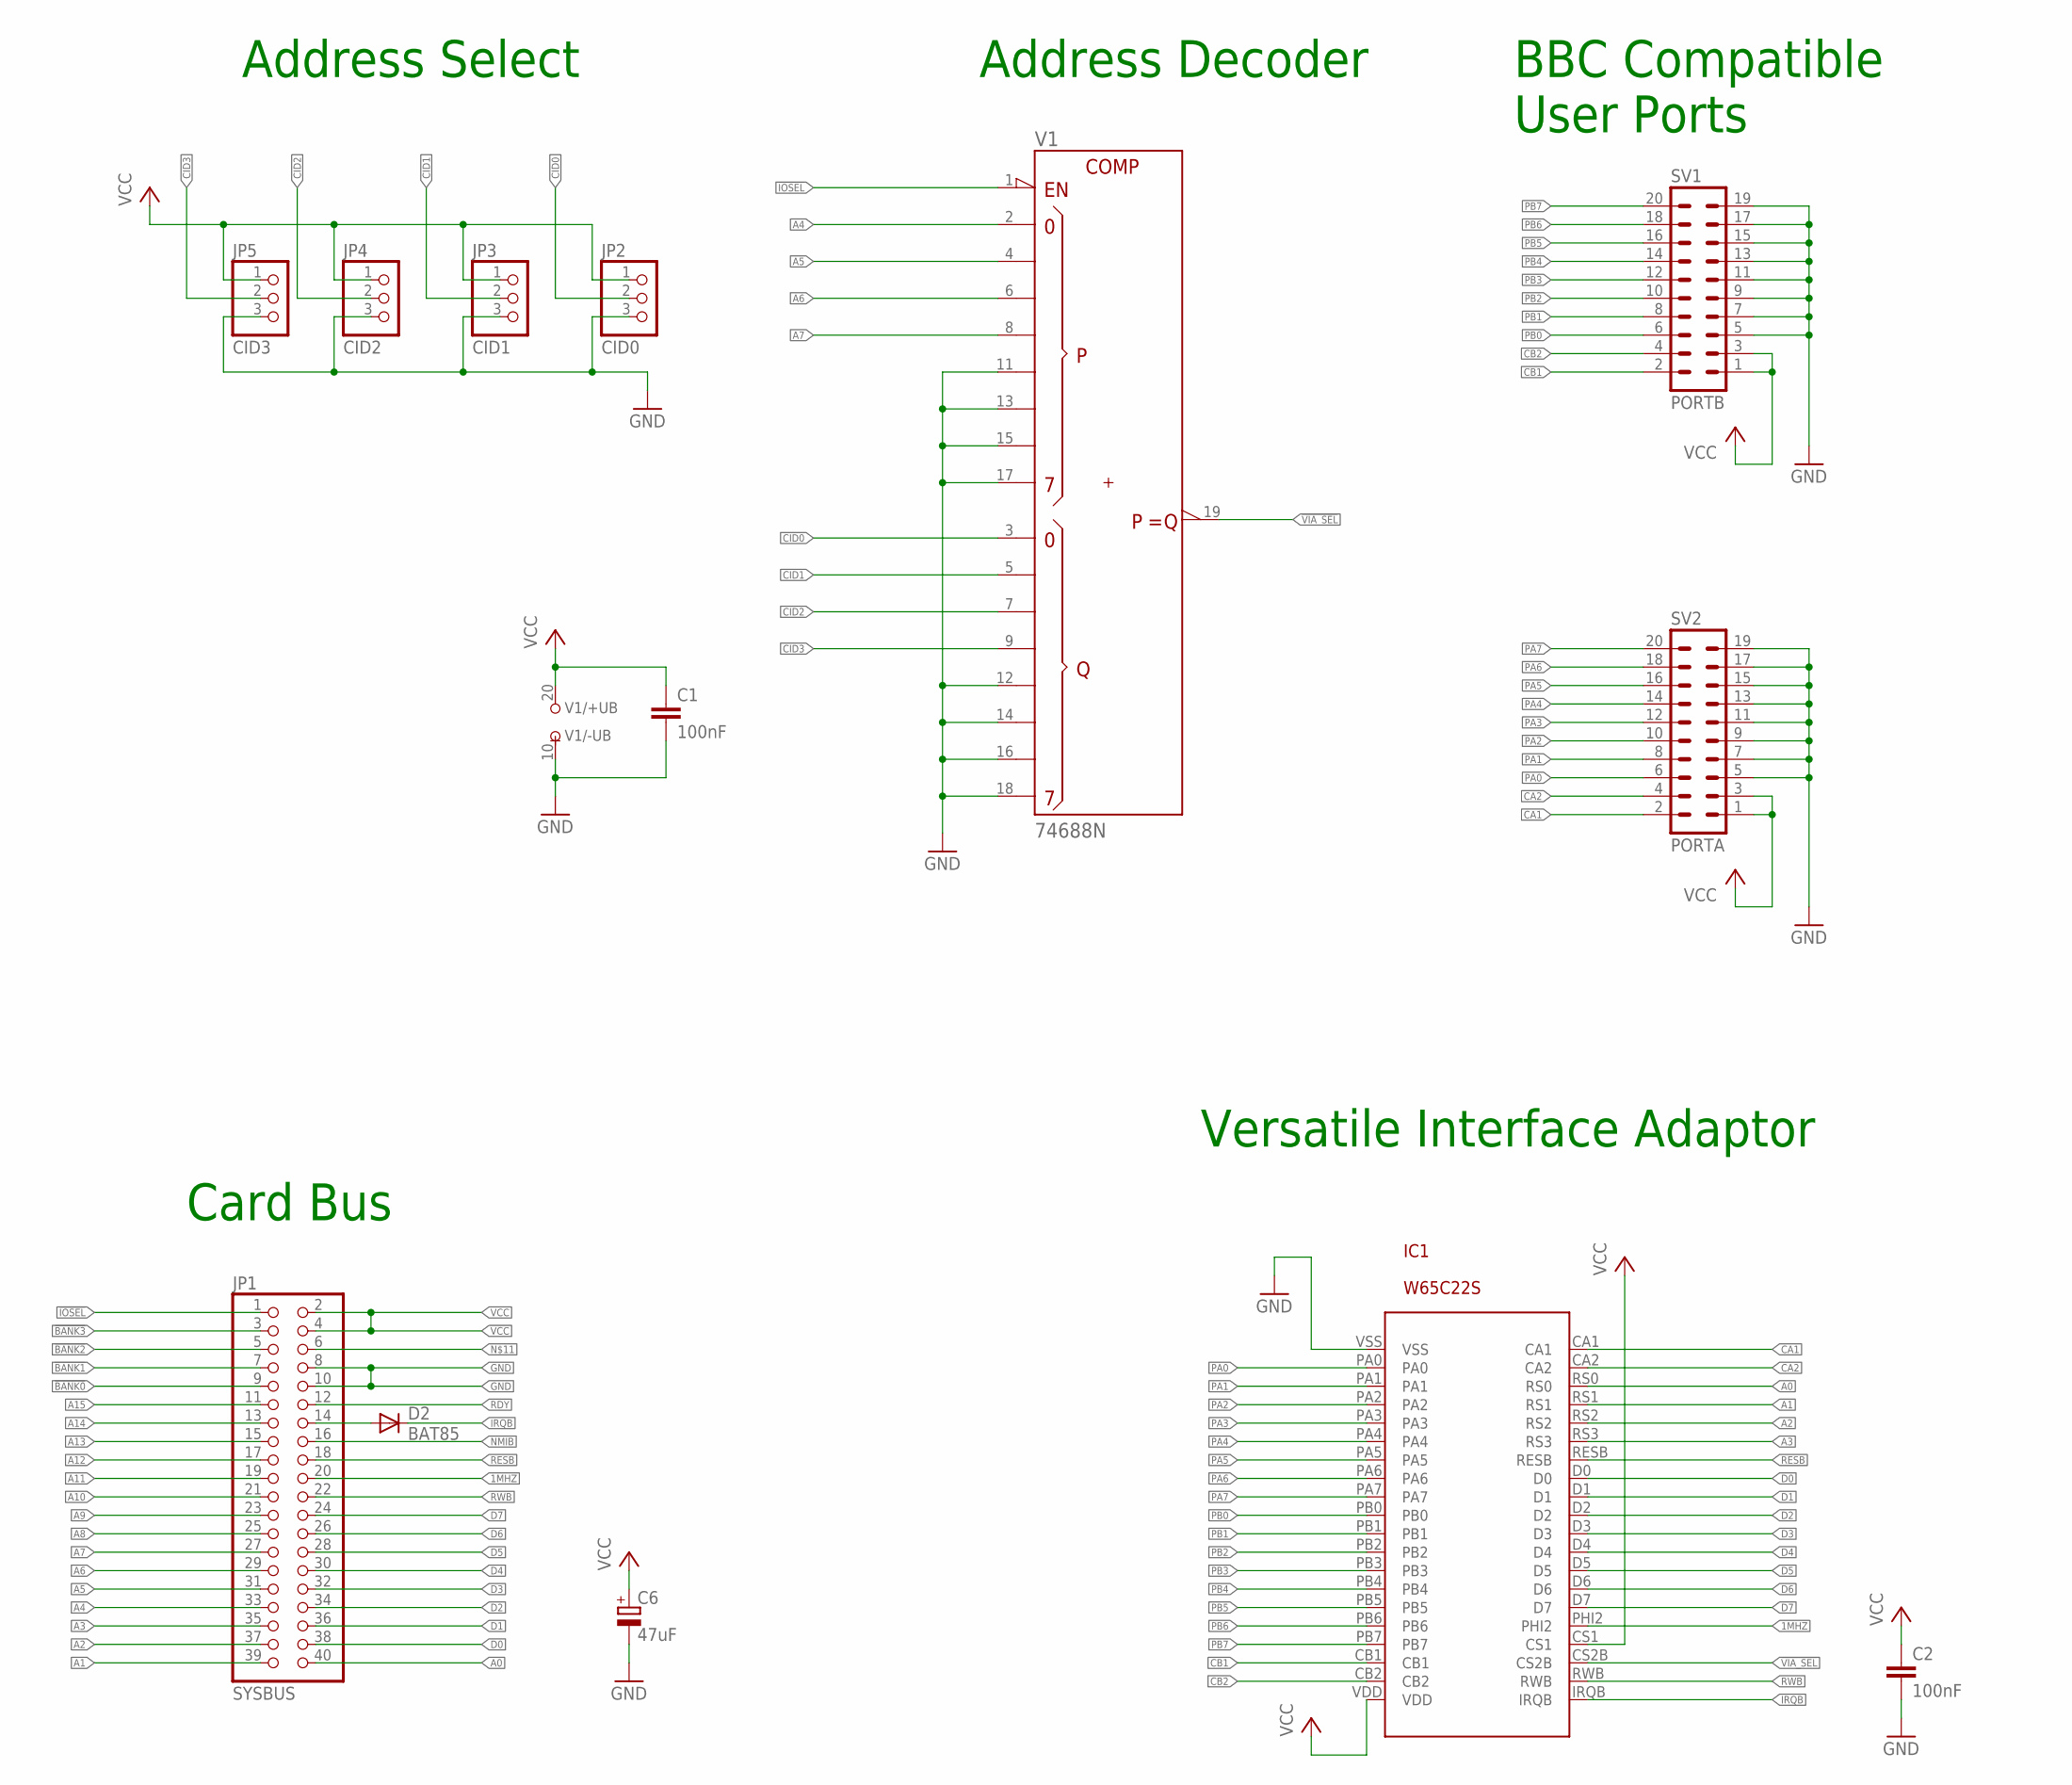
[picture p114: schematic Versatile IO Card.sch]

Parts:
C1, C2: 100nF; C050-025X075
C6: 47uF; E2,5-7
D2: BAT85; DO34-7
IC1: W65C22S; W65C22-DIP
JP1: SYSBUS; 2X20/90
JP2: CID0; 1X03
JP3: CID1; 1X03
JP4: CID2; 1X03
JP5: CID3; 1X03
SV1: PORTB; ML20L
SV2: PORTA; ML20L
V1: 74688N; DIL20

Connections:
1MHZ: IC1.PHI2, JP1.20
!BANK0: JP1.9
!BANK1: JP1.7
!BANK2: JP1.5
!BANK3: JP1.3
!IOSEL: JP1.1, V1.1 (!G)
!VIA_SEL: IC1.CS2B, V1.19 (!P=Q)
A0: IC1.RS0, JP1.40
A1: IC1.RS1, JP1.39
A2: IC1.RS2, JP1.37
A3: IC1.RS3, JP1.35
A4: JP1.33, V1.2 (P0)
A5: JP1.31, V1.4 (P1)
A6: JP1.29, V1.6 (P2)
A7: JP1.27, V1.8 (P3)
A8: JP1.25
A9: JP1.23
A10: JP1.21
A11: JP1.19
A12: JP1.17
A13: JP1.15
A14: JP1.13
A15: JP1.11
CA1: IC1.CA1, SV2.2
CA2: IC1.CA2, SV2.4
CB1: IC1.CB1, SV1.2
CB2: IC1.CB2, SV1.4
CID0: JP2.2, V1.3 (Q0)
CID1: JP3.2, V1.5 (Q1)
CID2: JP4.2, V1.7 (Q2)
CID3: JP5.2, V1.9 (Q3)
D0: IC1.D0, JP1.38
D1: IC1.D1, JP1.36
D2: IC1.D2, JP1.34
D3: IC1.D3, JP1.32
D4: IC1.D4, JP1.30
D5: IC1.D5, JP1.28
D6: IC1.D6, JP1.26
D7: IC1.D7, JP1.24
GND: C1.2, C2.2, C6.-, IC1.VSS, JP1.8, JP1.10, JP2.3, JP3.3, JP4.3, JP5.3, SV1.5, SV1.7, SV1.9, SV1.11, SV1.13, SV1.15, SV1.17, SV1.19, SV2.5, SV2.7, SV2.9, SV2.11, SV2.13, SV2.15, SV2.17, SV2.19, V1.10 (-UB), V1.11 (P4), V1.12 (Q4), V1.13 (P5), V1.14 (Q5), V1.15 (P6), V1.16 (Q6), V1.17 (P7), V1.18 (Q7)
IRQB: D2.C, IC1.IRQB
unnamed: D2.A, JP1.14
NMIB: JP1.16
PA0: IC1.PA0, SV2.6
PA1: IC1.PA1, SV2.8
PA2: IC1.PA2, SV2.10
PA3: IC1.PA3, SV2.12
PA4: IC1.PA4, SV2.14
PA5: IC1.PA5, SV2.16
PA6: IC1.PA6, SV2.18
PA7: IC1.PA7, SV2.20
PB0: IC1.PB0, SV1.6
PB1: IC1.PB1, SV1.8
PB2: IC1.PB2, SV1.10
PB3: IC1.PB3, SV1.12
PB4: IC1.PB4, SV1.14
PB5: IC1.PB5, SV1.16
PB6: IC1.PB6, SV1.18
PB7: IC1.PB7, SV1.20
RDY: JP1.12
RESB: IC1.RESB, JP1.18
RWB: IC1.RWB, JP1.22
VCC: C1.1, C2.1, C6.+, IC1.CS1, IC1.VDD, JP1.2, JP1.4, JP2.1, JP3.1, JP4.1, JP5.1, SV1.1, SV1.3, SV2.1, SV2.3, V1.20 (+UB)

Notes on the sheet:
Card Bus
Address Select
Address Decoder
BBC Compatible User Ports
Versatile Interface Adaptor
