JennyDigital/Tower-of-Eightness/Schematics/Versatile-IO-Card/Versatile IO Card.brd

## EAGLE design Schematics/Versatile-IO-Card/Versatile IO Card.brd (continued)

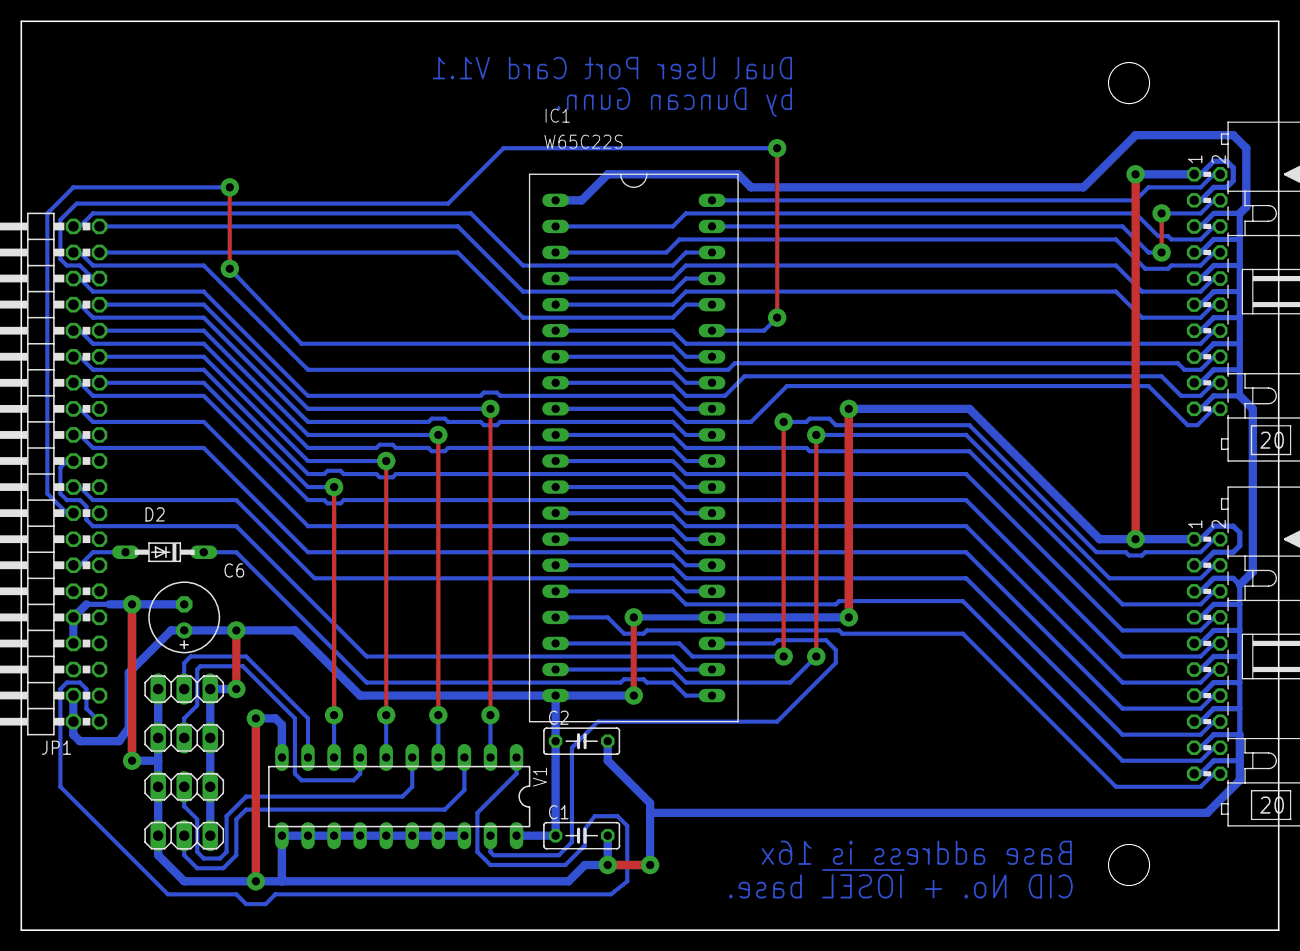
[picture p115: board Versatile IO Card.brd from above]

Board: 2 copper layers, 122.5 x 88.6 mm, 13 parts (0 on the bottom side), 49 nets.
