JennyDigital/Tower-of-Eightness/BASIC-Listings/Mplayer.bas

1 tempo=200
10 REM Musical score player
20 :
30 RESTORE 8000
40 CLS
50 DIM f(93): REM 93 notes
60 FOR i=0 TO 93
70 READ f(i) : NEXT i
100 :
110 REM Score player
120 :
130 RESTORE 1000
140 :
150 REM -1 = END
160 REM -2 = channel select follows
170 REM -3 = pause followed by count
180 REM -4 = set mode
190 :
195 READ score : PRINT score
200 IF score=-1 THEN GOTO 7000 : REM Execute all stop
210 IF score=-2 THEN GOSUB 6000 : REM set channel
220 IF score=-3 THEN READ pause : FOR i=0 TO pause*(1000/tempo) : NEXT i
230 IF score=-4 THEN READ md,m: ENVELOPE md,m
240 GOTO 190 : REM keep going until complete.
997 :
998 REM Sample sound
999 :
1000 DATA -2,0,36,16
1007 DATA -4,32000,0
1010 DATA -3,250
1020 DATA -2,1,40,16
1024 DATA -4,32000,0
1025 DATA -4,16000,0
1030 DATA -3,250
1040 DATA -2,2,43,16
1045 DATA -4,32000,0
1050 DATA -3,2000
1060 DATA -1
5997 :
5998 REM Channel setup
5999 :
6000 READ i,j,k
6010 SOUND i,f(j),k : RETURN
6997 :
6998 REM All STOP!
6999 :
7000 SOUND 0,0,0:SOUND 1,0,0:SOUND 2,0,0
7010 PRINT "Thank you for listening."
7020 END
7997 :
7998 REM Frequency table
7999 :
8000 DATA 7071,6647,6274,5919,5539,5274,4979,4699,4435,4186
8010 DATA 3951,3729,3521,3323,3136,3397,2794,2637,2489,2349
8020 DATA 2218,2093,1976,1865,1760,1661,1568,1480,1397,1319
8030 DATA 1245,1175,1109,1047,0988,0932,0880,0831,0784,0740
8040 DATA 0699,0659,0622,0587,0554,0523,0494,0466,0440,0415
8050 DATA 0392,0370,0349,0330,0311,0294,0277,0262,0247,0233
8060 DATA 0220,0211,0196,0185,0175,0165,0156,0147,0139,0131
8070 DATA 0123,0117,0110,0104,0098,0093,0087,0082,0078,0073
8090 DATA 0069,0065,0062,0058,0055,0052,0049,0046,0044,0041
8100 DATA 0039,0037,0035,0033
9997 :
9998 REM Musical instruction score
9999 :
