JennyDigital/Tower-of-Eightness/BASIC-Listings/banner print.bas

1 DOKE $85,$B000:CLEAR : REM Make Make space for font.
2 B1$=CHR$($DB):W1$=" ": cb=$BB00
3 lo=17
4 B$=B1$+B1$+B1$+B1$+B1$:W$=W1$+W1$+W1$+W1$+W1$
5 IF PEEK(cb-1)=1 THEN GOTO 30
10 PRINT "Loading BBC Font file"
20 LOAD "BBC Font" cb
30 :
40 POKE cb-1,1
50 CLS
60 PRINT "Enter string to print";
70 INPUT ms$
80 GOSUB 2000
90 FOR c=1 TO LEN(ms$)
100 c$=MID$(ms$,c,1)
110 GOSUB 1000 : REM char print
120 NEXT c
130 END
997 :
998 REM Char print
999 :
1000 co=(ASC(c$)-32)*8
1002 IF hc=0 THEN GOTO 1010
1005 BITSET $5E0,2
1010 FOR bit=7 TO 0 STEP -1
1020 l$=""
1030 FOR bo=7 TO 0 STEP -1
1040 IF BITTST(cb+bo+co,bit) THEN l$=l$+B$ ELSE l$=l$+W$
1050 NEXT bo
1060 PRINT TAB(lo);l$
1070 PRINT TAB(lo);l$
1080 NEXT bit
1085 BITCLR $5E0,2
1090 RETURN
1997 :
1998 REM YN Grab
1999 :
2000 PRINT "Hardcopy (Y/N):";
2010 DO
2020 GET K$
2030 LOOP UNTIL K$<>""
2040 K$=UCASE$(K$)
2050 IF K$="Y" OR K$="N" THEN PRINT K$ ELSE 2010
2060 IF K$="Y" THEN hc=1 ELSE hc=0
2070 RETURN
