JennyDigital/Tower-of-Eightness/BASIC-Listings/pi_calc.bas

100 DIM N(104)
110 FOR T=1 TO 104:N(T)=2:NEXT
120 FOR D=1 TO 31
130 Q=0
140 FOR T=104 TO 1 STEP -1
150 B=2*T-1
160 IF T=1 THEN B=10
170 R=T*Q+N(T)*10:Q=INT(R/B):N(T)=R-Q*B
180 NEXT
190 PRINT RIGHT$(STR$(Q),1);
200 IF D=1 THEN PRINT ".";
210 NEXT
