JennyDigital/Tower-of-Eightness/BASIC-Listings/Joytest 2.0.bas

10 CLS: PRINT CHR$(2);CHR$(0);
20 LOCATE 0,2 : M$="Joystick Tester V2.00"
30 GOSUB 2000
40 GOSUB 3000 : REM Print Arrows
50 LOCATE 0,22: PRINT "Press any key to exit."
60 PB=$C040
70 DO
80 J=1 : GOSUB 4000
90 J=2 : GOSUB 4000
100 GET K$
110 LOOP UNTIL K$<>""
120 PRINT CHR$(2);"_";CHR$(3);
130 END
140 :
1998 REM Centered Test Print Function
1999 :
2000 ml = LEN(M$)
2010 PRINT SPC(39-(ml/2));M$
2020 RETURN
2997 :
2998 REM Arrow set printer
2999 :
3000 EC$=CHR$($1A) : REM Escape for PCDOS chars
3010 LA$=EC$+CHR$($1B) : RA$=EC$+CHR$($1A)
3020 UA$=EC$+CHR$($18) : DA$=EC$+CHR$($19)
3030 SX$=CHR$($0E)     : SY$=CHR$($0F)
3040 :
3050 LOCATE 15,10 : PRINT UA$:LOCATE 60,10:PRINT UA$
3060 LOCATE 13,12 : PRINT LA$;" 1 ";RA$
3070 LOCATE 58,12 : PRINT LA$;" 2 ";RA$
3080 LOCATE 15,14 : PRINT DA$: LOCATE 60,14 : PRINT DA$
3090 RETURN 
3997 :
3998 REM Joystick Scan and Print function
3999 :
4000 IF J=1 THEN XO=12 ELSE XO=57
4010 YO=9
4020 IF J=1 THEN BITCLR PB,0 ELSE BITSET PB,0
4030 JV=($FF EOR PEEK(PB))
4035 REM up
4040 LOCATE XO+3,YO
4050 IF (JV AND 2)<>0 THEN PRINT "*"; ELSE PRINT " ";
4055 REM left
4060 LOCATE XO,YO+3
4070 IF (JV AND 8)<>0 THEN PRINT "*"; ELSE PRINT " ";
4075 REM right
4080 LOCATE XO+6,YO+3
4090 IF (JV AND 16)<>0 THEN PRINT "*"; ELSE PRINT " ";
4095 REM bottom
4100 LOCATE XO+3,YO+6
4110 IF (JV AND 4)<>0 THEN PRINT "*"; ELSE PRINT " ";
4115 REM fire
4120 LOCATE XO+1,YO+8
4130 IF (JV AND 32)<>0 THEN PRINT "FIRE!!"; ELSE PRINT "      ";
4140 RETURN
